architecture-building-systems/Wireless-Sensor-Network/Gateway/Gateway_Feather/Images/Gateway_collage.jpg

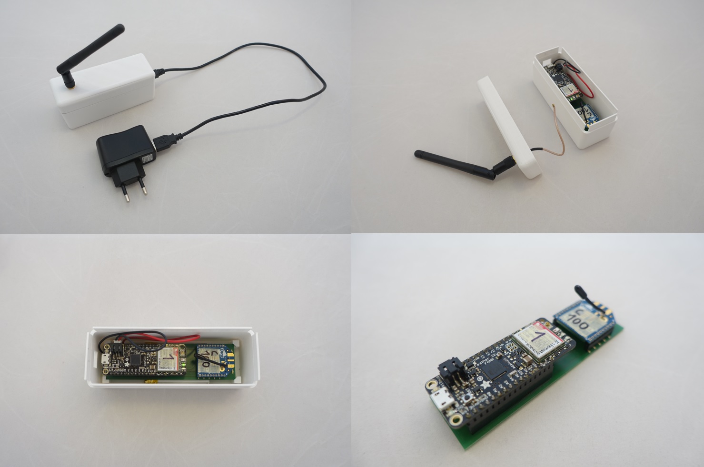
Gateway/Gateway_Feather/Images/Gateway_collage.jpg
