architecture-building-systems/Wireless-Sensor-Network/Gateway/Gateway_Mega/Images/gatweay_mega_with_enclosure_4.jpg

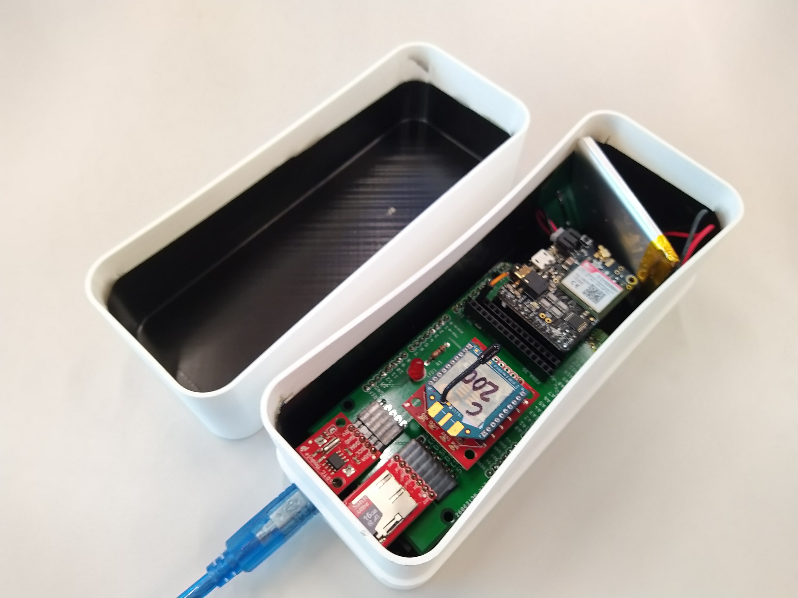
Gateway/Gateway_Mega/Images/gatweay_mega_with_enclosure_4.jpg
