architecture-building-systems/Wireless-Sensor-Network/Miscellaneous/Images/predecessor_systems/wsn_1_sensor_node_1.jpg

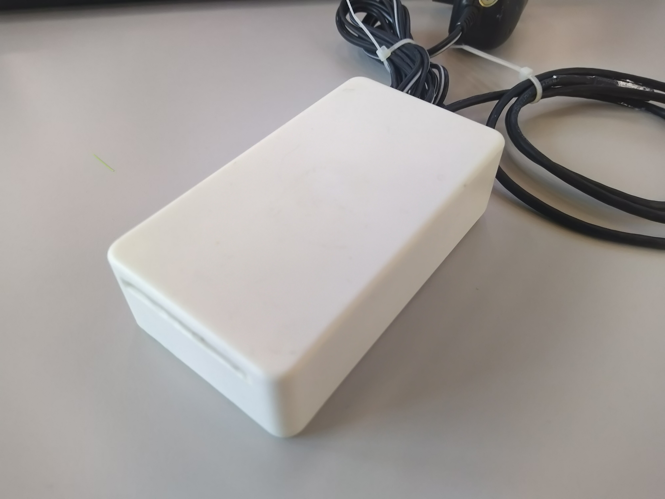
Miscellaneous/Images/predecessor_systems/wsn_1_sensor_node_1.jpg
