architecture-building-systems/Wireless-Sensor-Network/Miscellaneous/Images/predecessor_systems/wsn_2_router_node_2.jpg

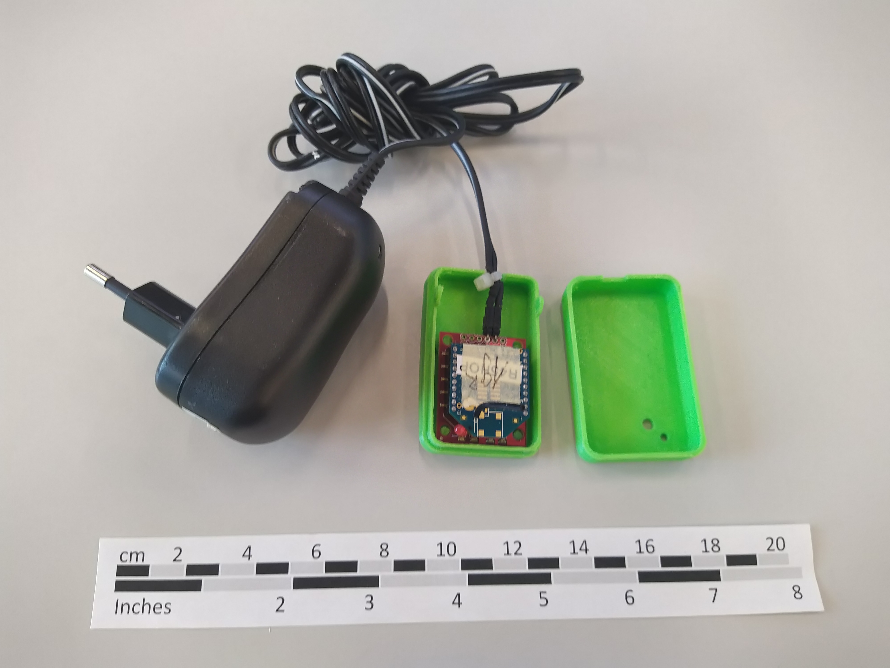
Miscellaneous/Images/predecessor_systems/wsn_2_router_node_2.jpg
