architecture-building-systems/Wireless-Sensor-Network/Miscellaneous/Images/predecessor_systems/wsn_2_router_node_4.jpg

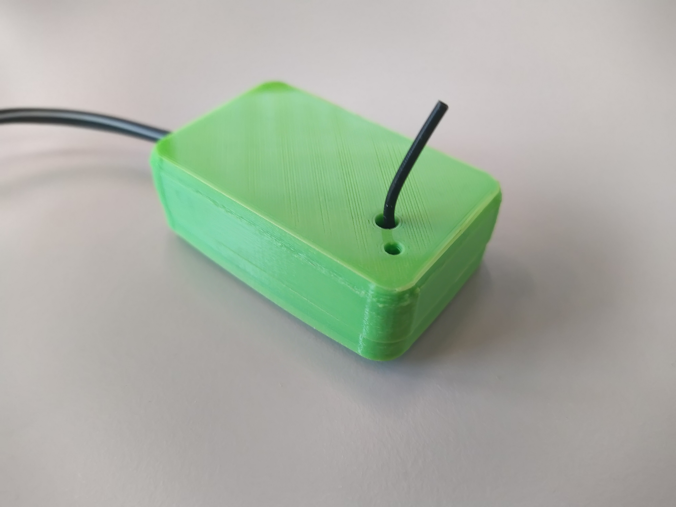
Miscellaneous/Images/predecessor_systems/wsn_2_router_node_4.jpg
