architecture-building-systems/Wireless-Sensor-Network/Miscellaneous/Images/predecessor_systems/wsn_2_sensor_node_5.jpg

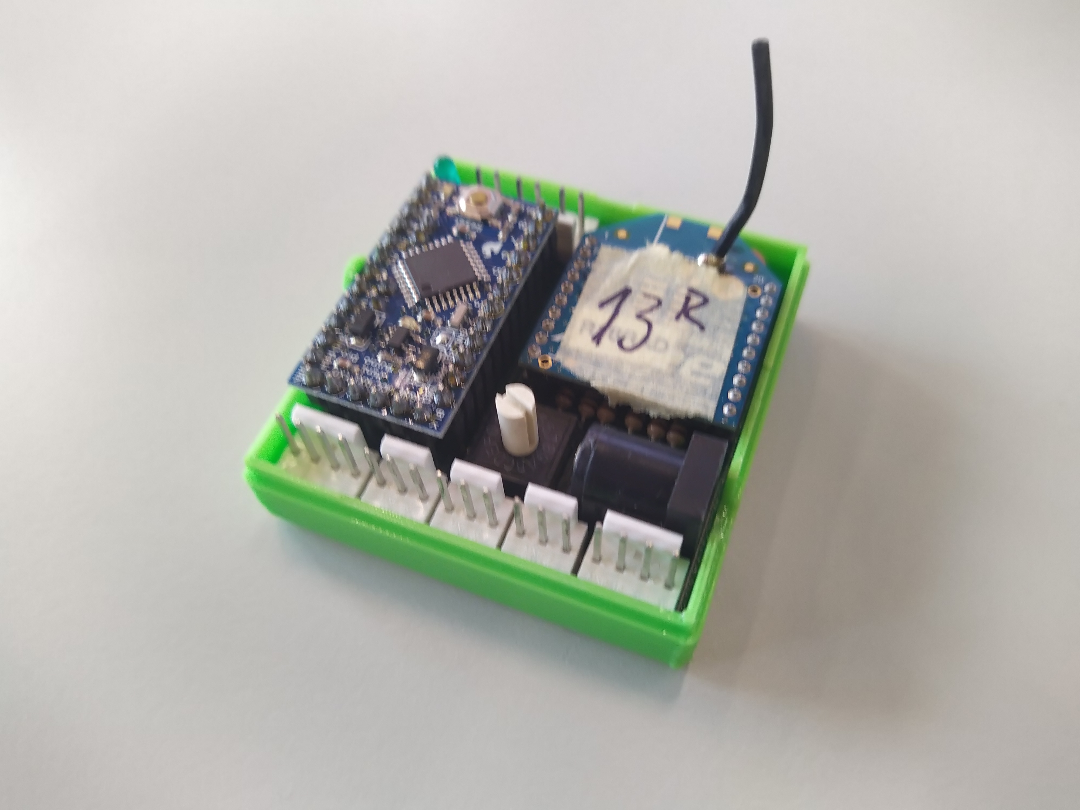
Miscellaneous/Images/predecessor_systems/wsn_2_sensor_node_5.jpg
