architecture-building-systems/Wireless-Sensor-Network/Miscellaneous/Images/Sensor_Kit_2.png

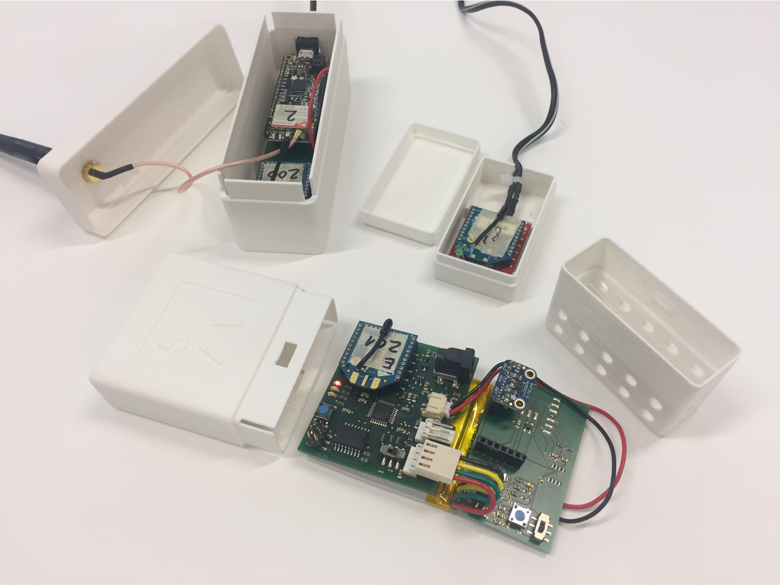
Miscellaneous/Images/Sensor_Kit_2.png
