architecture-building-systems/Wireless-Sensor-Network/Miscellaneous/Images/Sensor_Node_1.png

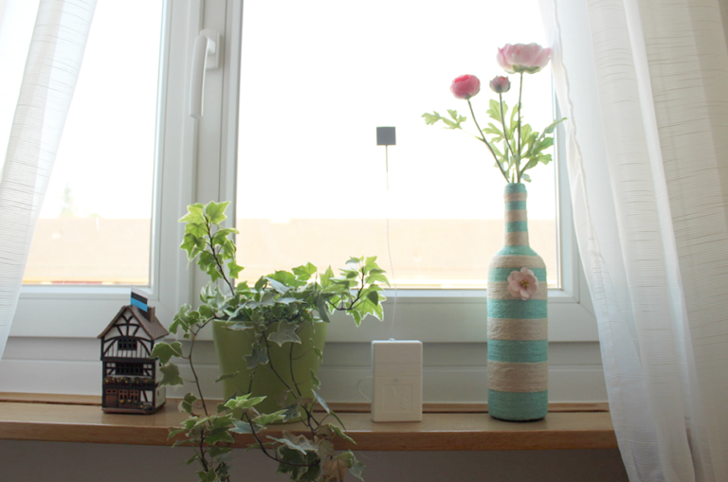
Miscellaneous/Images/Sensor_Node_1.png
