architecture-building-systems/Wireless-Sensor-Network/Miscellaneous/Images/Sensor_Node_2.png

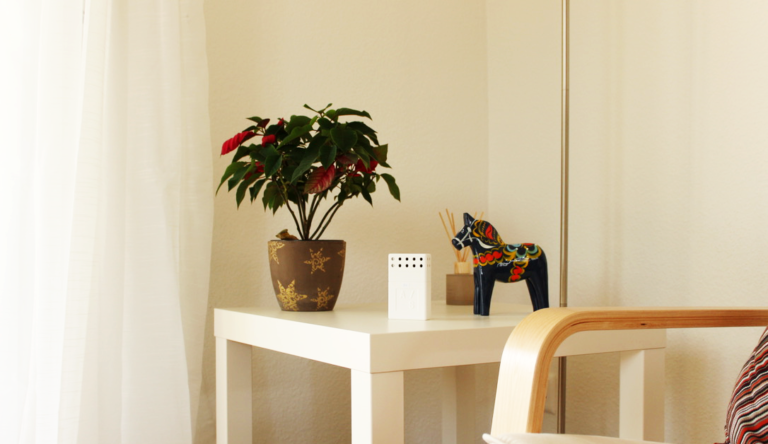
Miscellaneous/Images/Sensor_Node_2.png
