architecture-building-systems/Wireless-Sensor-Network/Miscellaneous/Images/Sensor_Node_3.png

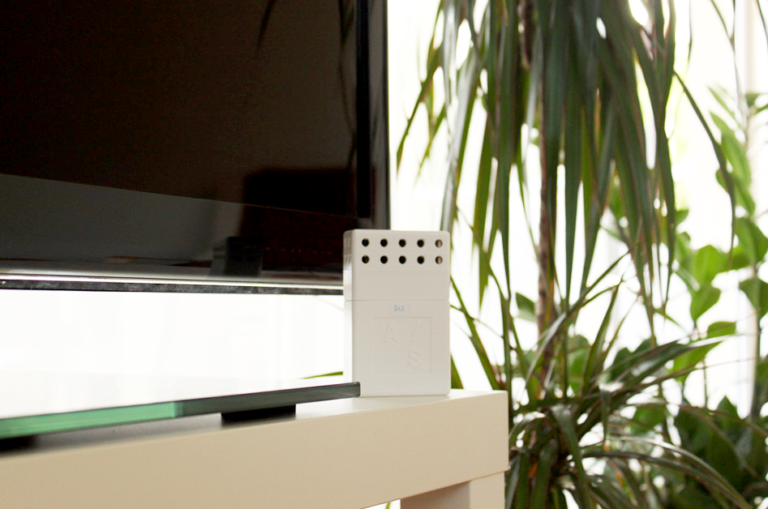
Miscellaneous/Images/Sensor_Node_3.png
