architecture-building-systems/Wireless-Sensor-Network/Sensor_Node/Main_module/Images/main_module_diode_orientation.jpg

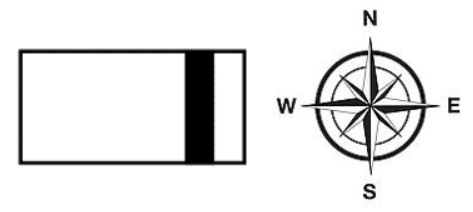
Sensor_Node/Main_module/Images/main_module_diode_orientation.jpg
