architecture-building-systems/Wireless-Sensor-Network/Sensor_Node/Main_module/Images/Main_module_high_side_switch_ic_orientation.jpg

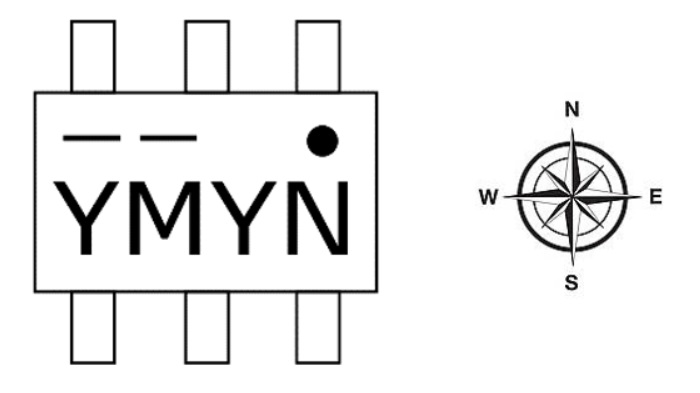
Sensor_Node/Main_module/Images/Main_module_high_side_switch_ic_orientation.jpg
