architecture-building-systems/Wireless-Sensor-Network/Sensor_Node/Main_module/Images/main_module_isp_connector_orientation.jpg

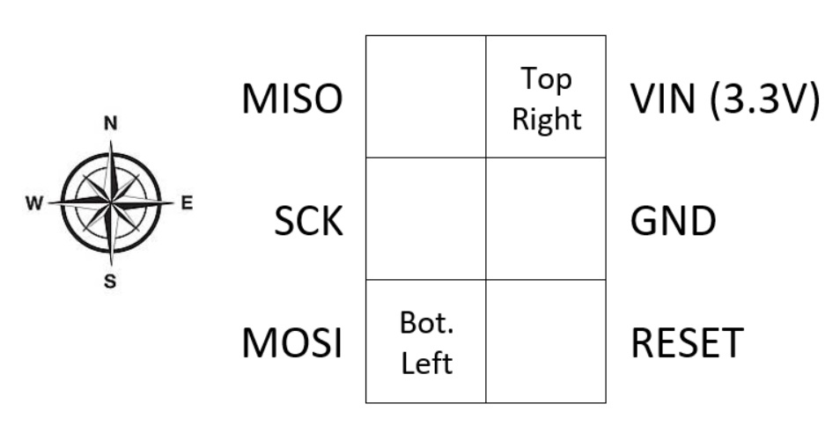
Sensor_Node/Main_module/Images/main_module_isp_connector_orientation.jpg
