architecture-building-systems/Wireless-Sensor-Network/Gateway/Gateway_Feather/CAD/Gateway_housing_bottom_v6.stl

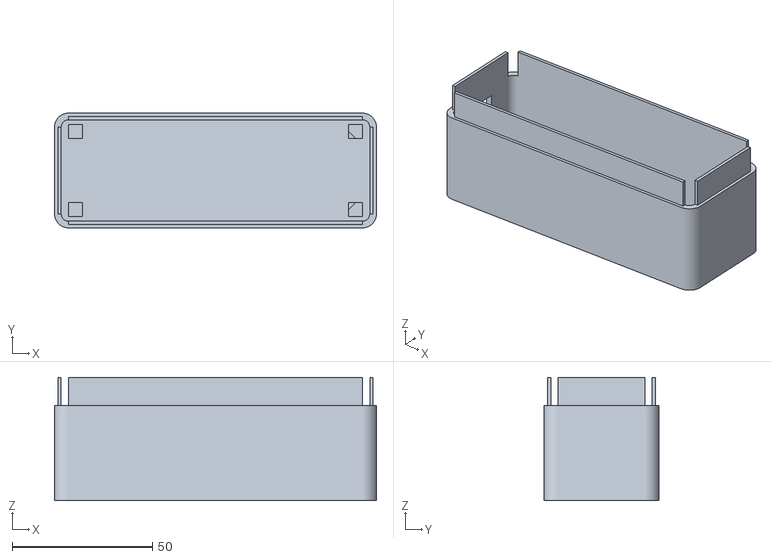
[picture p46: CAD file, 2017-03-10]
Gateway/Gateway_Feather/CAD/Gateway_housing_bottom_v6.stl
115.0 x 41.0 x 44.0
