architecture-building-systems/Wireless-Sensor-Network/Miscellaneous/CAD/cable_reel_v4.1_bottom.stl

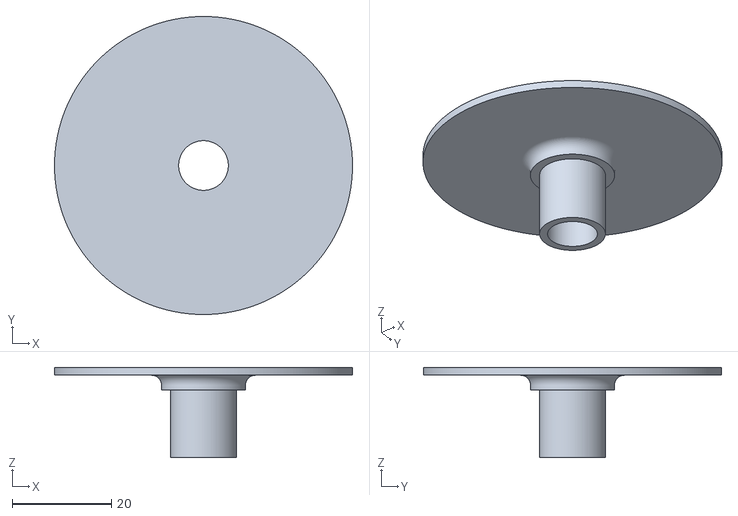
[picture p47: CAD file, 2018-12-11]
Miscellaneous/CAD/cable_reel_v4.1_bottom.stl
60.0 x 60.0 x 18.2
