architecture-building-systems/Wireless-Sensor-Network/Sensor_Node/CAD/u_value_angle_v5.stl

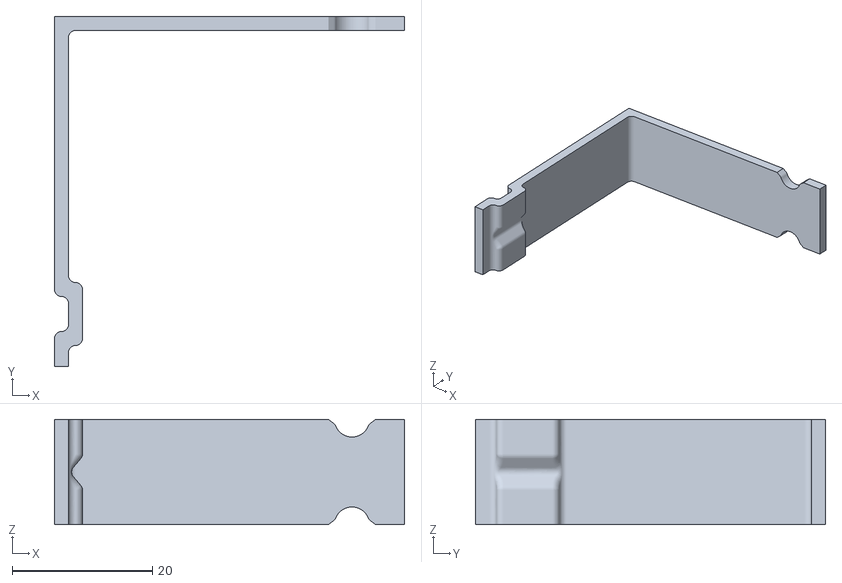
[picture p48: CAD file, 2017-05-09]
Sensor_Node/CAD/u_value_angle_v5.stl
50.0 x 50.0 x 15.0
