architecture-building-systems/Wireless-Sensor-Network/Miscellaneous/CAD/Reed_switch_transport_lock_v1.prt.stl

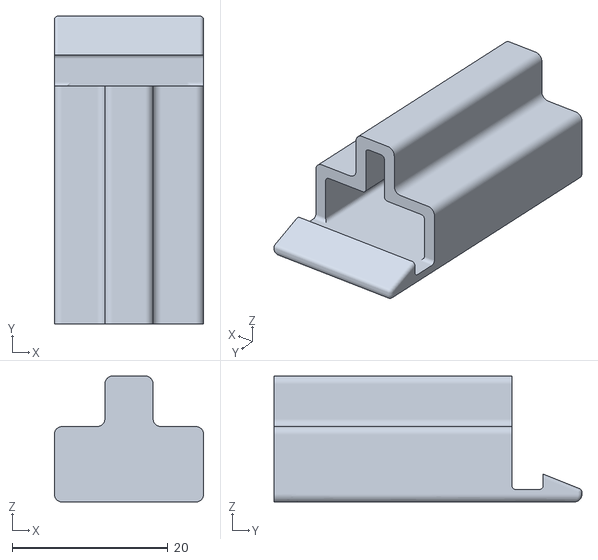
[picture p50: CAD file, 2018-12-06]
Miscellaneous/CAD/Reed_switch_transport_lock_v1.prt.stl
19.2 x 39.6 x 16.2
