architecture-building-systems/Wireless-Sensor-Network/Miscellaneous/CAD/battery_box_v2_small.stl

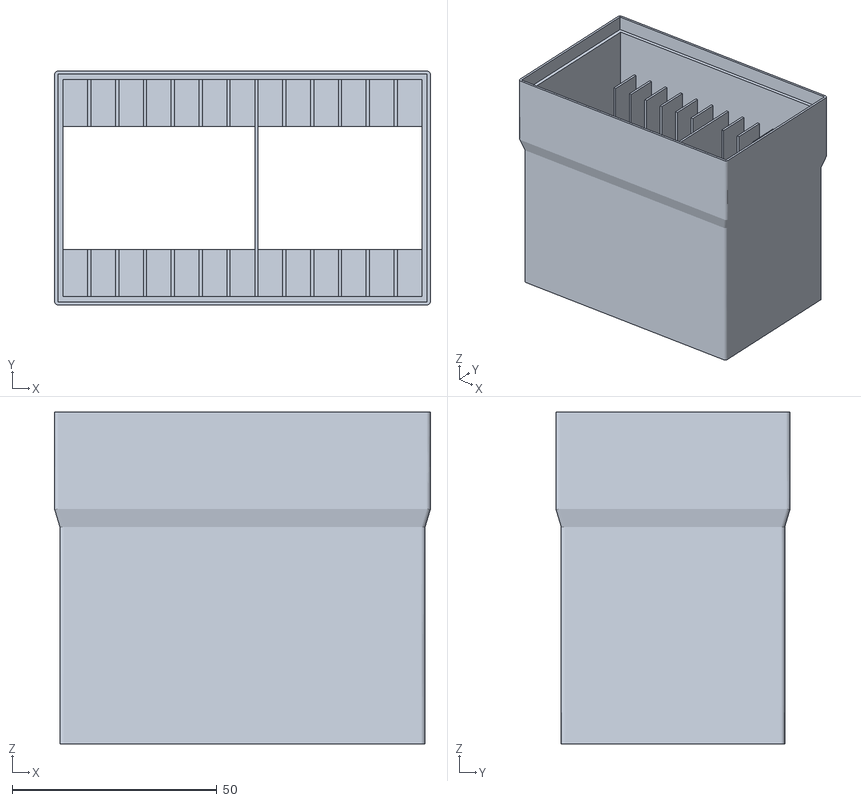
[picture p51: CAD file, 2018-12-06]
Miscellaneous/CAD/battery_box_v2_small.stl
91.8 x 57.2 x 81.0
