architecture-building-systems/Wireless-Sensor-Network/Miscellaneous/CAD/battery_box_v2.stl

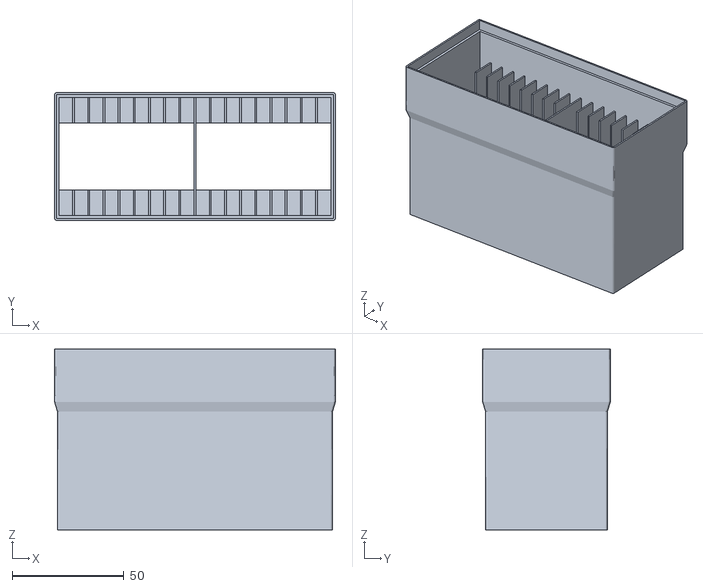
[picture p52: CAD file, 2018-02-06]
Miscellaneous/CAD/battery_box_v2.stl
125.8 x 57.2 x 81.0
