architecture-building-systems/Wireless-Sensor-Network/Miscellaneous/CAD/cable_reel_v2.stl

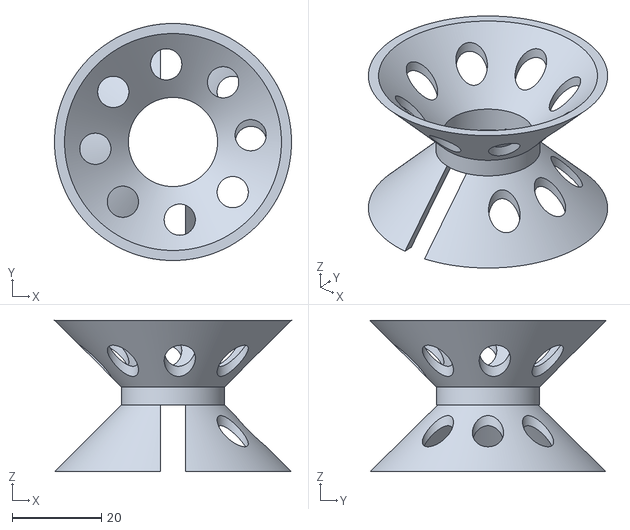
[picture p53: CAD file, 2018-02-04]
Miscellaneous/CAD/cable_reel_v2.stl
53.2 x 53.2 x 34.0
