architecture-building-systems/Wireless-Sensor-Network/Miscellaneous/CAD/dustpan_v1.stl

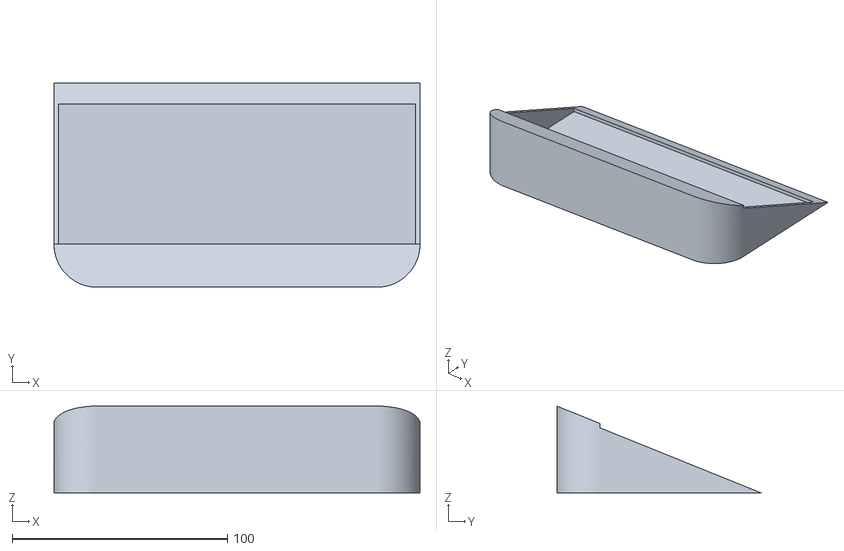
[picture p54: CAD file, 2017-06-19]
Miscellaneous/CAD/dustpan_v1.stl
170.0 x 95.0 x 40.4
