architecture-building-systems/Wireless-Sensor-Network/Miscellaneous/CAD/xbee_graber_v1.stl

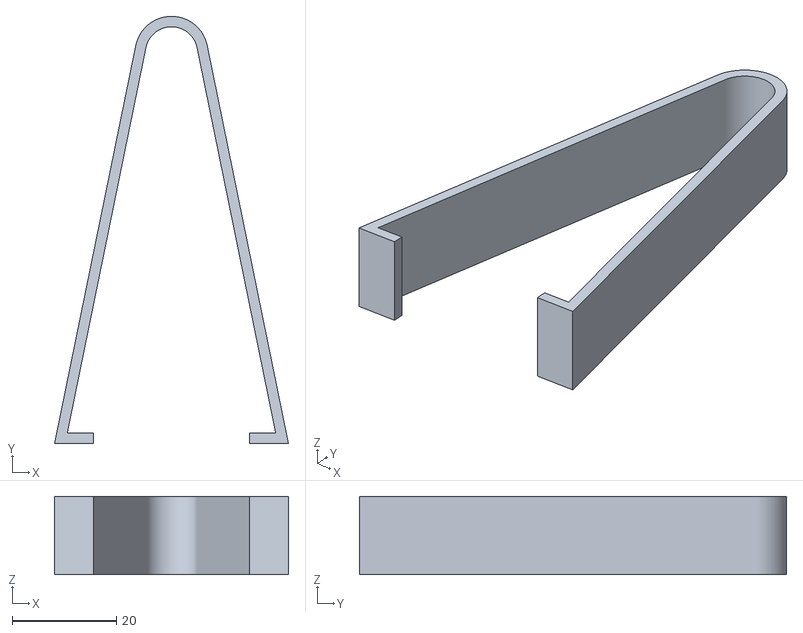
[picture p55: CAD file, 2017-04-19]
Miscellaneous/CAD/xbee_graber_v1.stl
44.9 x 82.0 x 15.0
