architecture-building-systems/Wireless-Sensor-Network/Miscellaneous/Images/instructions/arduino_ide_select_board_arduino_mega.png

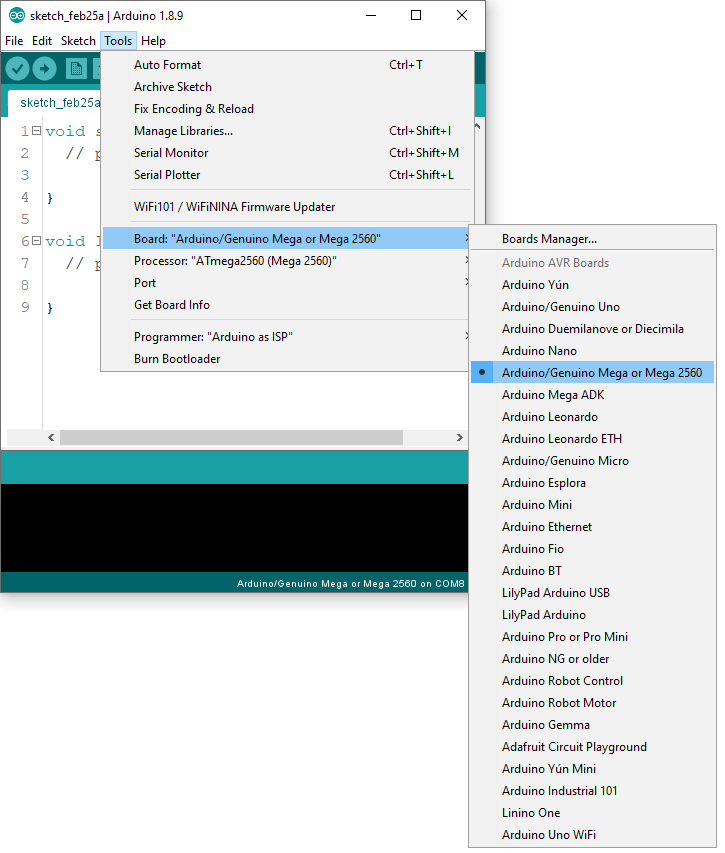
Miscellaneous/Images/instructions/arduino_ide_select_board_arduino_mega.png
