architecture-building-systems/Wireless-Sensor-Network/Miscellaneous/Images/instructions/arduino_ide_select_board_arduino_pro_mini.png

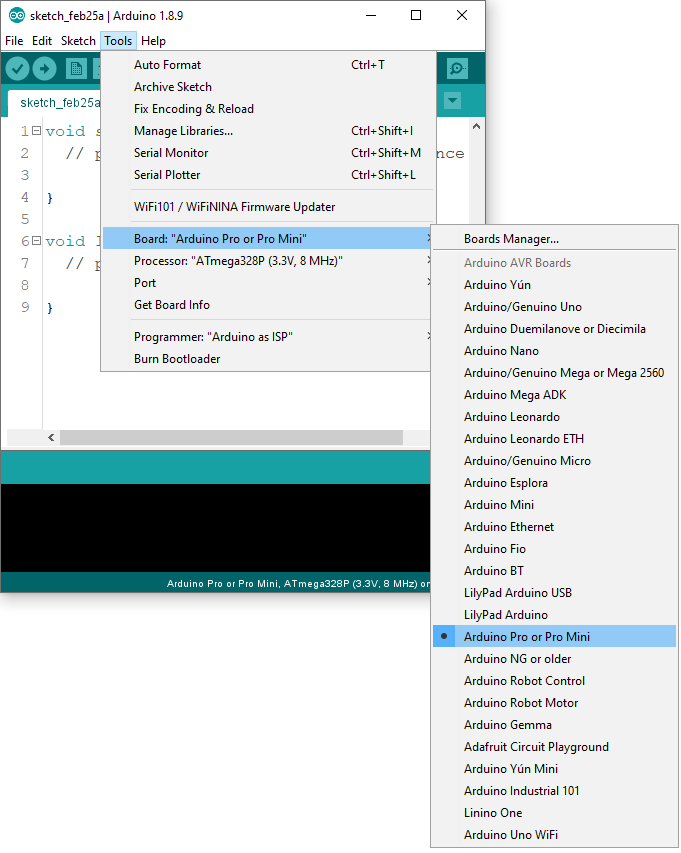
Miscellaneous/Images/instructions/arduino_ide_select_board_arduino_pro_mini.png
