architecture-building-systems/Wireless-Sensor-Network/Miscellaneous/Images/instructions/arduino_ide_select_processor_atmega328p_3.3v.png

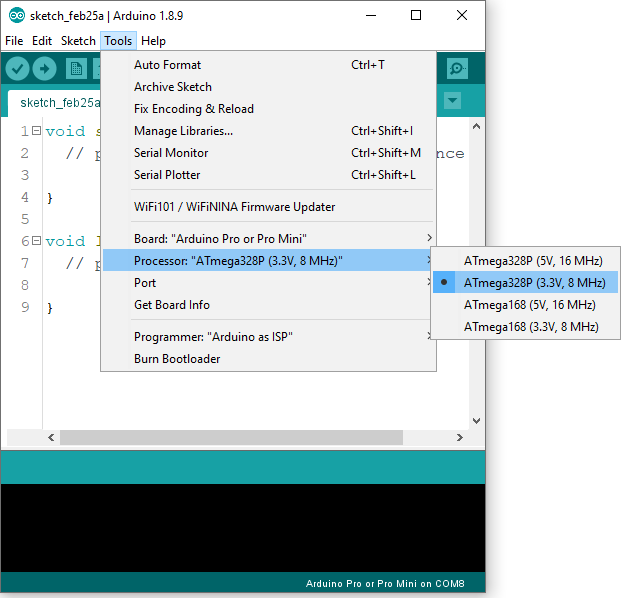
Miscellaneous/Images/instructions/arduino_ide_select_processor_atmega328p_3.3v.png
