architecture-building-systems/Wireless-Sensor-Network/Miscellaneous/Images/instructions/arduino_ide_select_processor_atmega2560.png

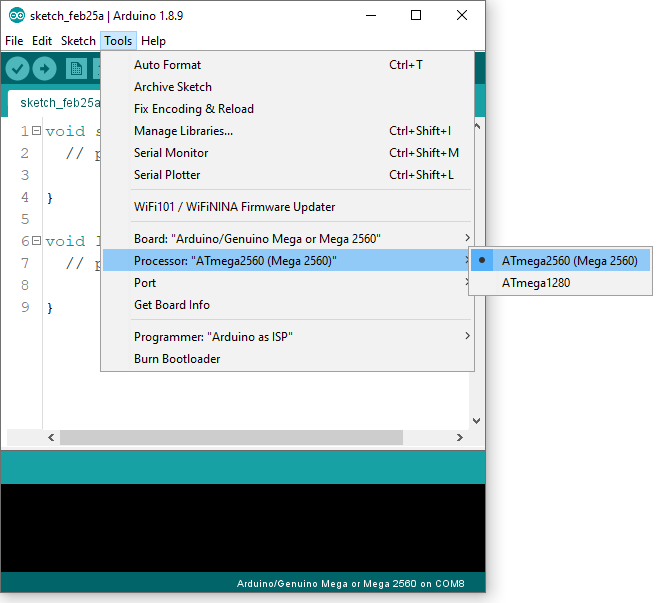
Miscellaneous/Images/instructions/arduino_ide_select_processor_atmega2560.png
