architecture-building-systems/Wireless-Sensor-Network/Miscellaneous/Images/instructions/arduino_ide_select_programmer_mega.png

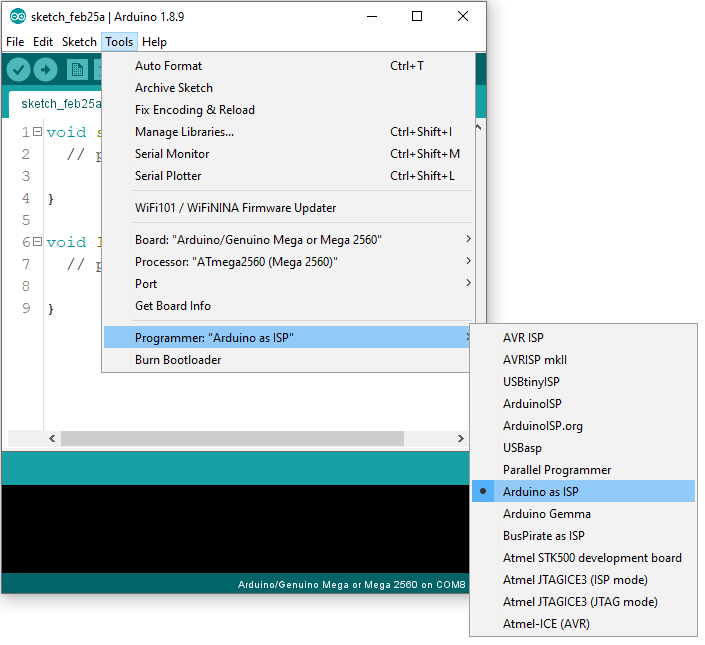
Miscellaneous/Images/instructions/arduino_ide_select_programmer_mega.png
