architecture-building-systems/Wireless-Sensor-Network/Miscellaneous/Images/instructions/arduino_ide_upload_sketch_to_atmega328p_with_programmer.png

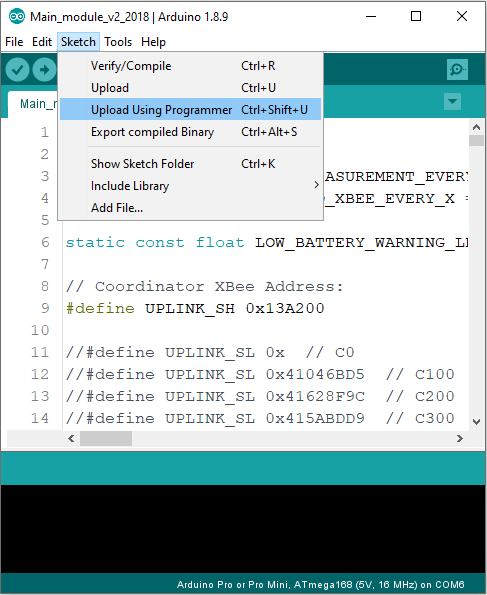
Miscellaneous/Images/instructions/arduino_ide_upload_sketch_to_atmega328p_with_programmer.png
