architecture-building-systems/Wireless-Sensor-Network/Miscellaneous/Images/instructions/arduino_ide_upload_sketch_to_atmega2560_via_serial.png

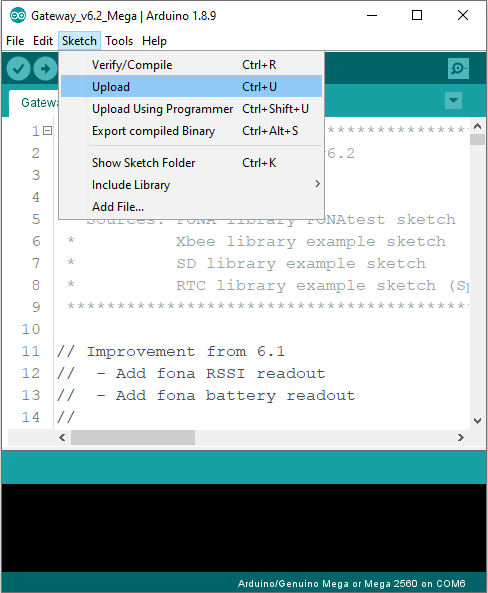
Miscellaneous/Images/instructions/arduino_ide_upload_sketch_to_atmega2560_via_serial.png
