architecture-building-systems/Wireless-Sensor-Network/Miscellaneous/Images/instructions/arduino_pro_mini_as_isp.jpg

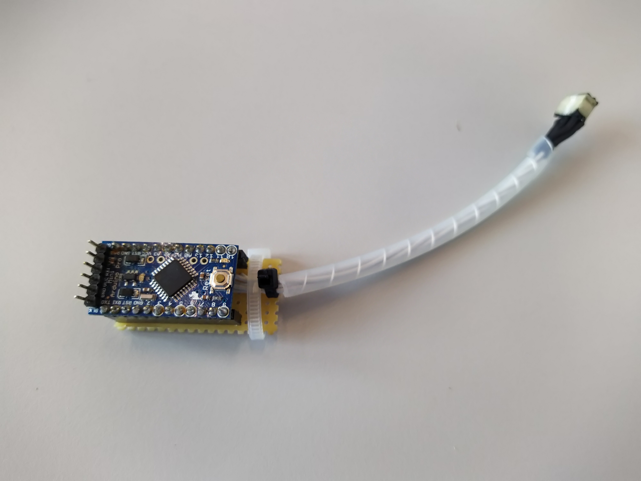
Miscellaneous/Images/instructions/arduino_pro_mini_as_isp.jpg
