architecture-building-systems/Wireless-Sensor-Network/Miscellaneous/Images/instructions/screenshot_x-ctu_select_profile.png

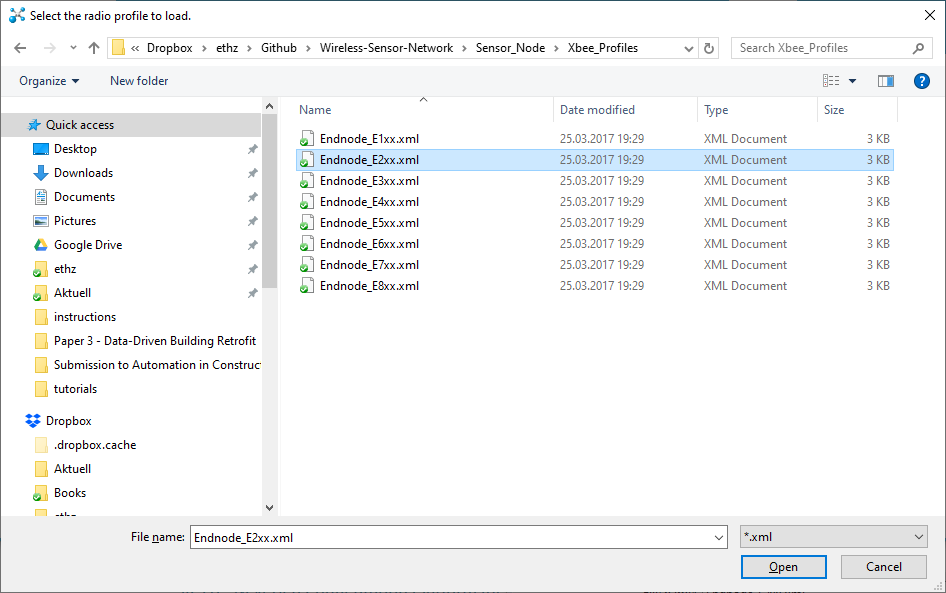
Miscellaneous/Images/instructions/screenshot_x-ctu_select_profile.png
