architecture-building-systems/Wireless-Sensor-Network/Miscellaneous/Images/instructions/screenshot_x-ctu_select_radio_module.png

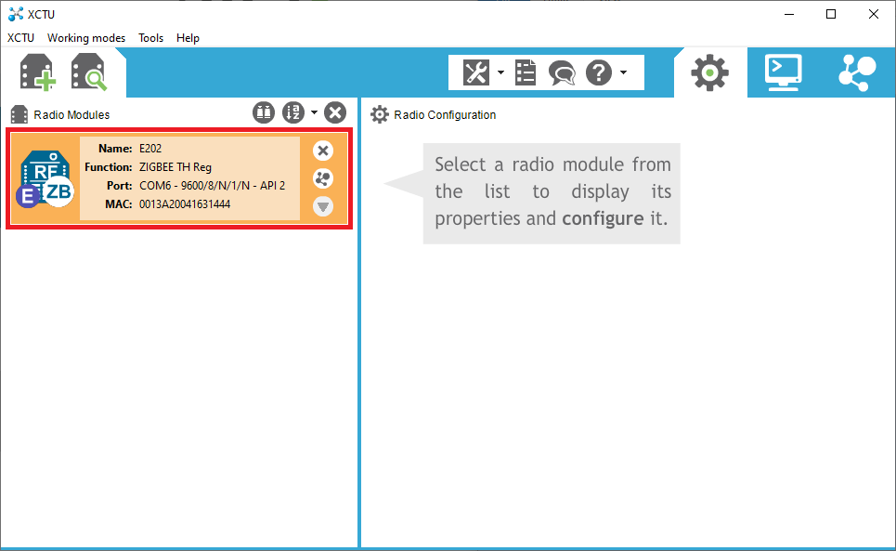
Miscellaneous/Images/instructions/screenshot_x-ctu_select_radio_module.png
