architecture-building-systems/Wireless-Sensor-Network/Miscellaneous/Images/instructions/arduino_ide_verify_sketch.png

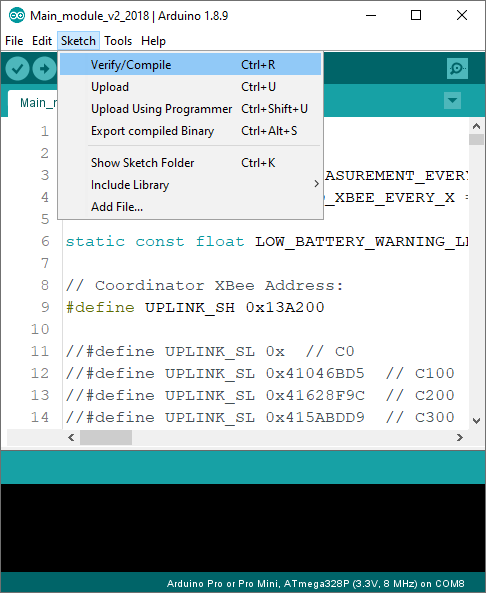
Miscellaneous/Images/instructions/arduino_ide_verify_sketch.png
