architecture-building-systems/Wireless-Sensor-Network/Miscellaneous/Images/instructions/screenshot_x-ctu_debugging_mesh_network_scan.png

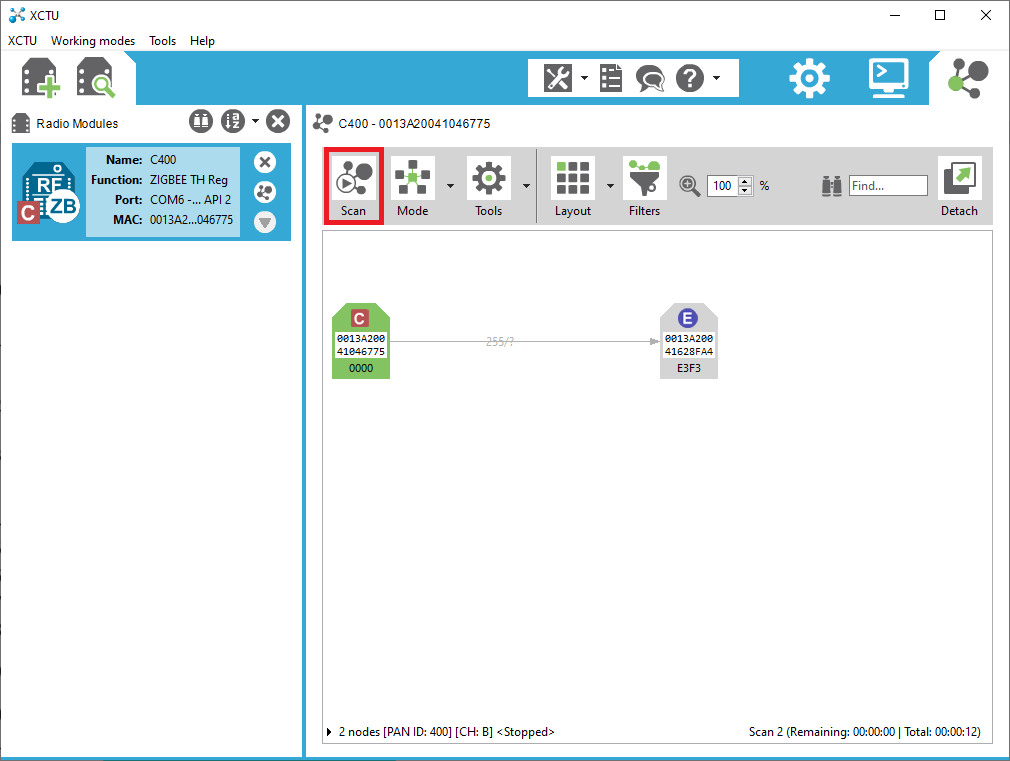
Miscellaneous/Images/instructions/screenshot_x-ctu_debugging_mesh_network_scan.png
