architecture-building-systems/Wireless-Sensor-Network/Sensor_Node/Sensor_modules/Sensor_Module_XX_Protoyping/Eagle/Sensor_Module_0xXX_Prototyping_v1_board.pdf

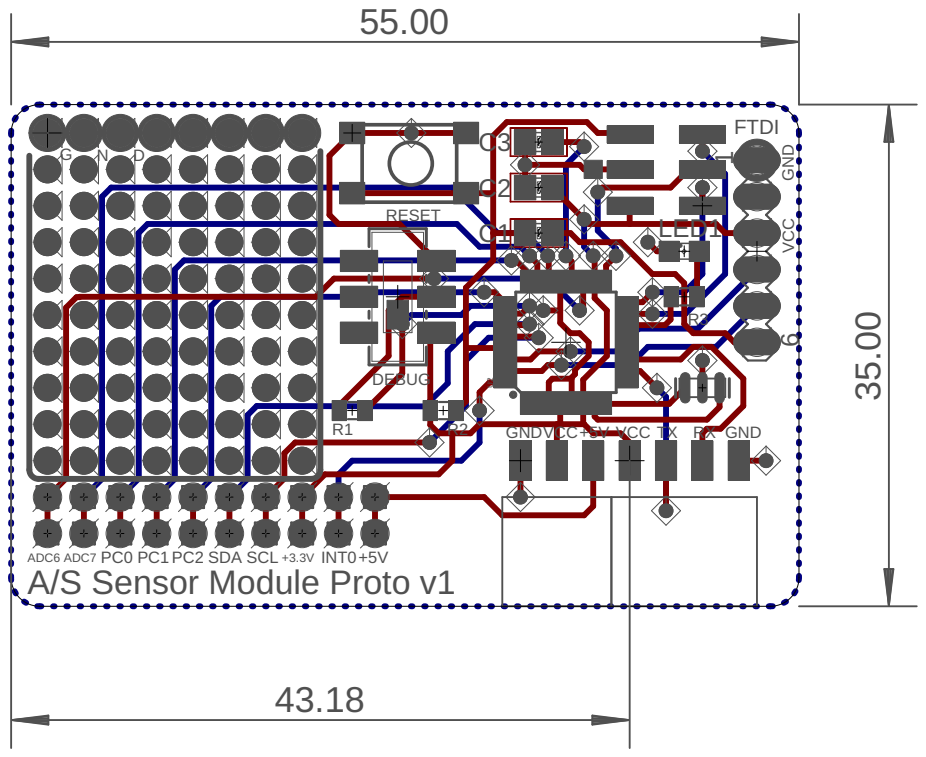
[picture p82: page 1]

VCC TX RX GND
