architecture-building-systems/Wireless-Sensor-Network/Sensor_Node/Sensor_modules/Sensor_Module_06_CO2_CCS811_v2/Eagle/Sensor_Module_0x06_CO2_CCS811_v2_board.pdf

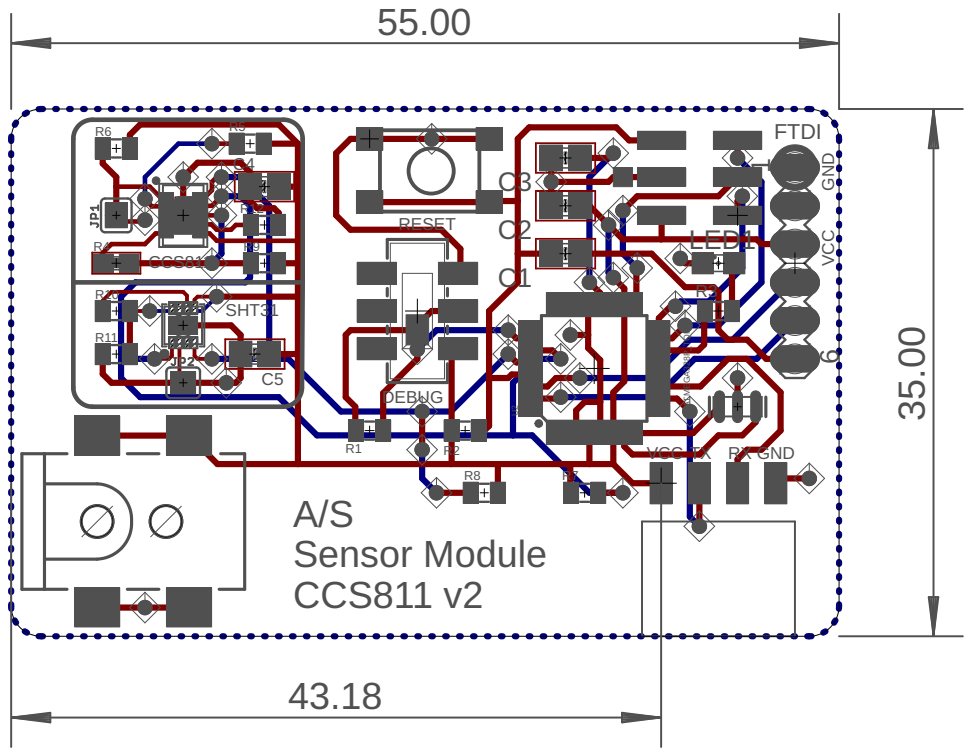
[picture p93: page 1]
