architecture-building-systems/Wireless-Sensor-Network/Sensor_Node/Sensor_modules/Sensor_Module_08_Dual_Temperatures_2xDS18B20_v1/Eagle/Sensor_Module_0x08_Dual_Temperatures_2xDS18B20_v1_board.pdf

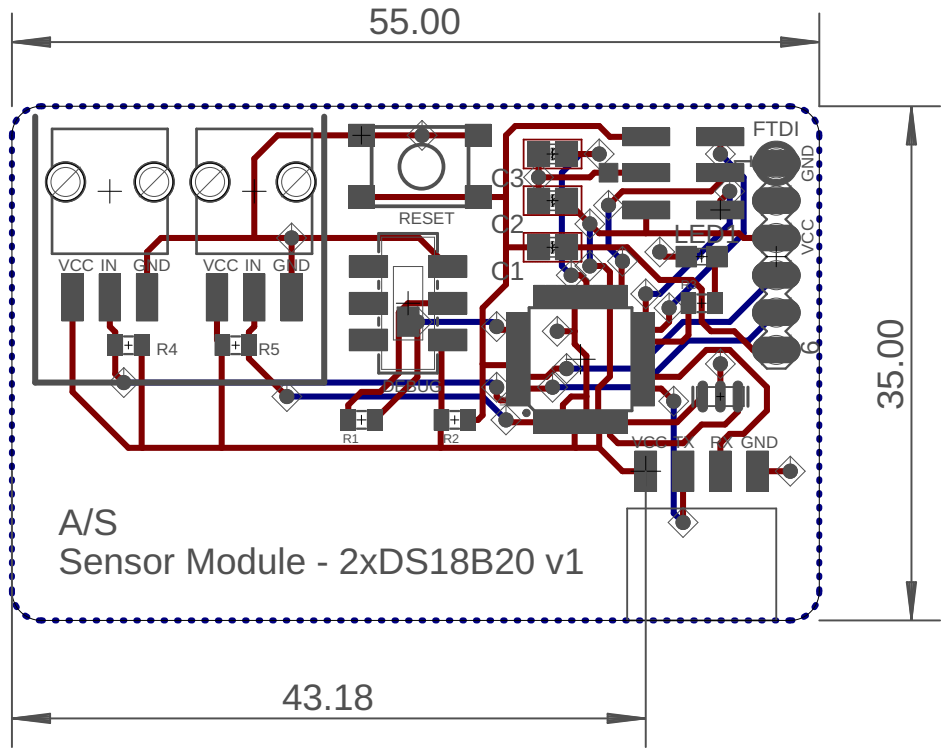
[picture p94: page 1]
