architecture-building-systems/Wireless-Sensor-Network/Sensor_Node/Sensor_modules/Sensor_Module_12_U-Value/Eagle/Sensor_Module_0x12_U-Value_v1_board.pdf

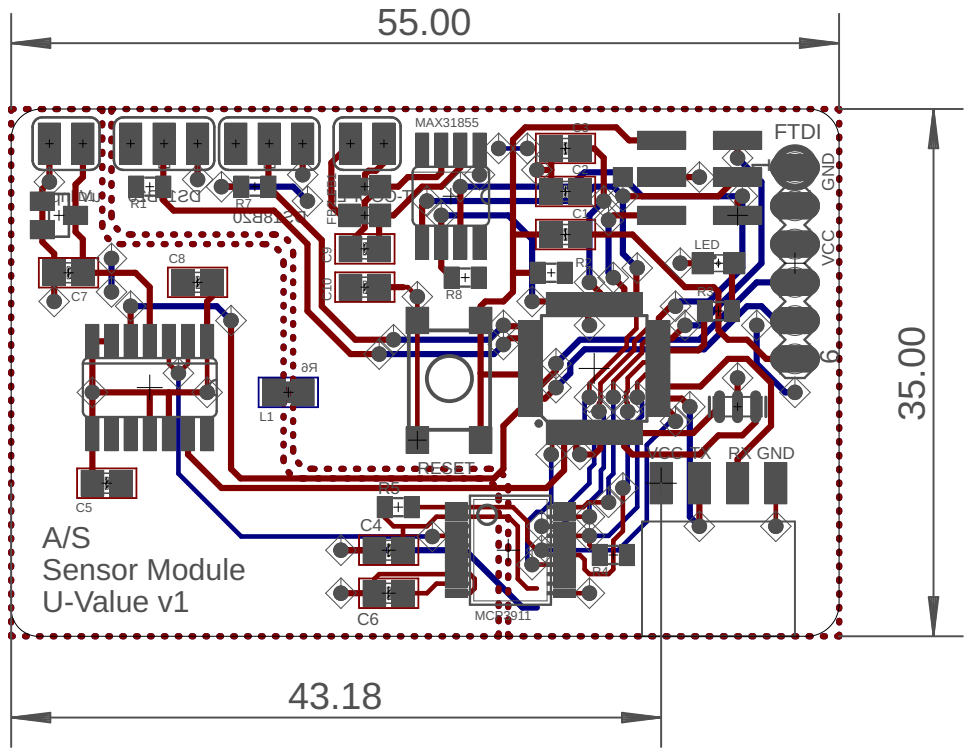
[picture p95: page 1]
