architecture-building-systems/Wireless-Sensor-Network/Sensor_Node/Sensor_modules/Sensor_Module_05_09_10_11_Pulse_v1/Eagle/Sensor_Module_0x09_0x10_Pulse_v1_board.pdf

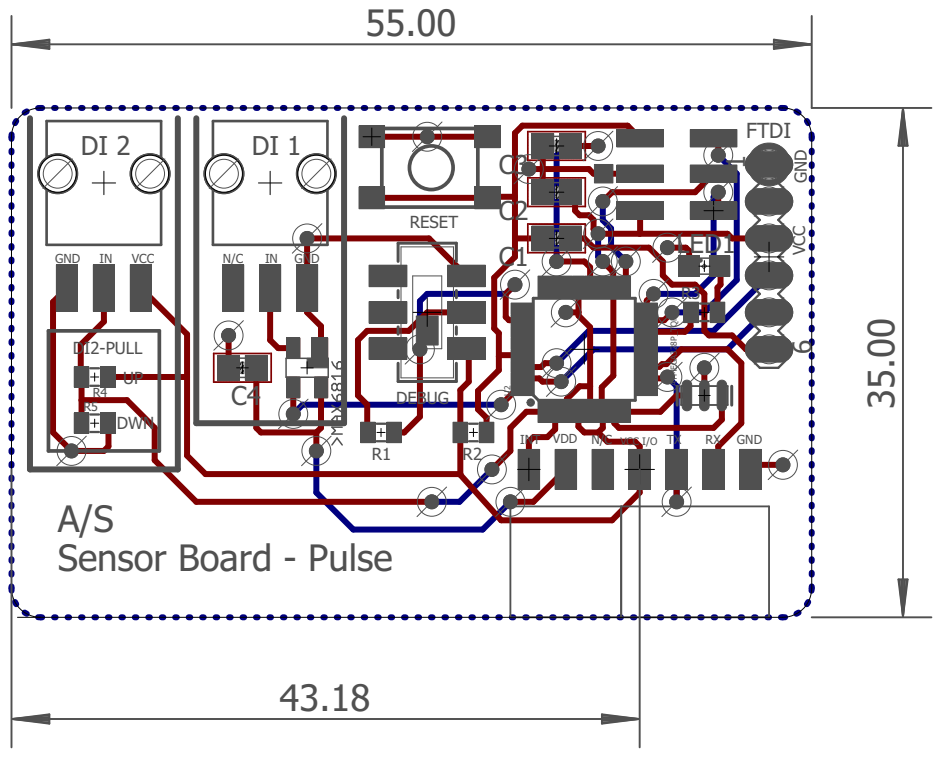
[picture p96: page 1]
