architecture-building-systems/Wireless-Sensor-Network/Sensor_Node/Sensor_modules/Previous Versions/Sensor_Module_0x02_TH_SHT31_v1/Eagle/Sensor_Module_0x02_TH_SHT31_v1_board.pdf

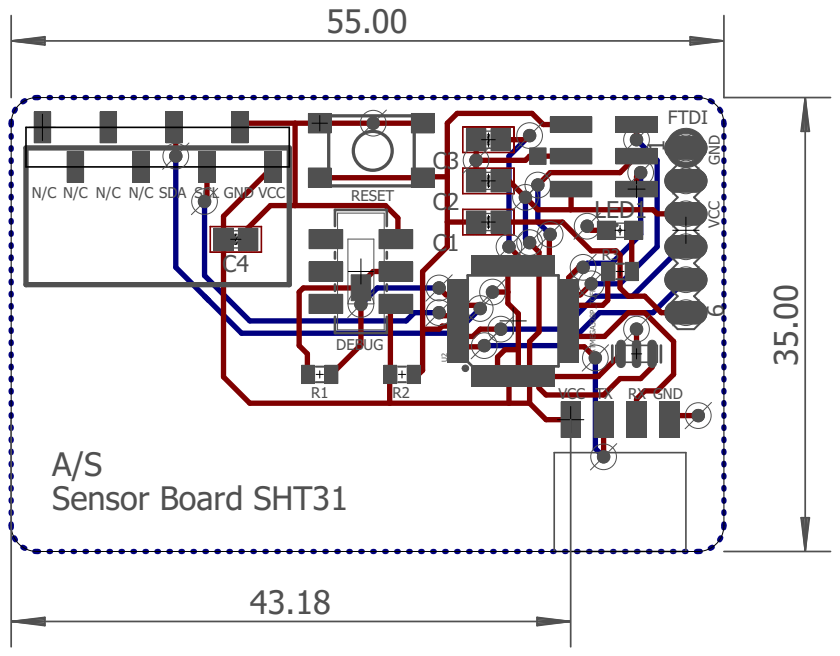
[picture p97: page 1]

N/C N/C N/C SDA SCL GND VCC
