architecture-building-systems/Wireless-Sensor-Network/Sensor_Node/Sensor_modules/Previous Versions/Sensor_Module_0x04_Luminosity_TSL2561_v1/Eagle/Sensor_Module_0x04_Luminosity_TSL2561_v1_board.pdf

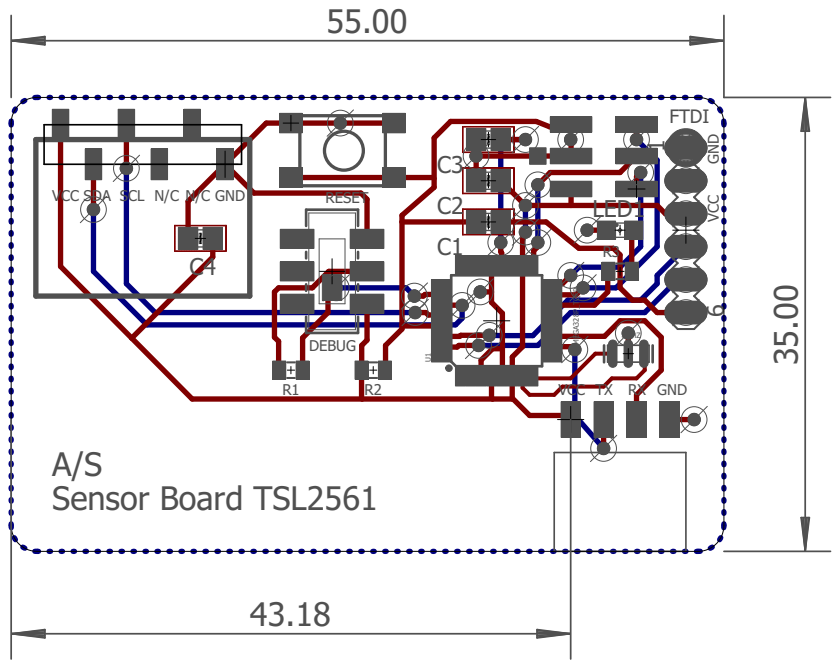
[picture p98: page 1]

VCC SDA SCL N/C N/C GND

VCC TX RX GND
