architecture-building-systems/Wireless-Sensor-Network/Sensor_Node/Sensor_modules/Previous Versions/Sensor_Module_0x02_TH_SHT31_v1/Eagle/Sensor_Module_0x02_TH_SHT31_v1_schematic.pdf

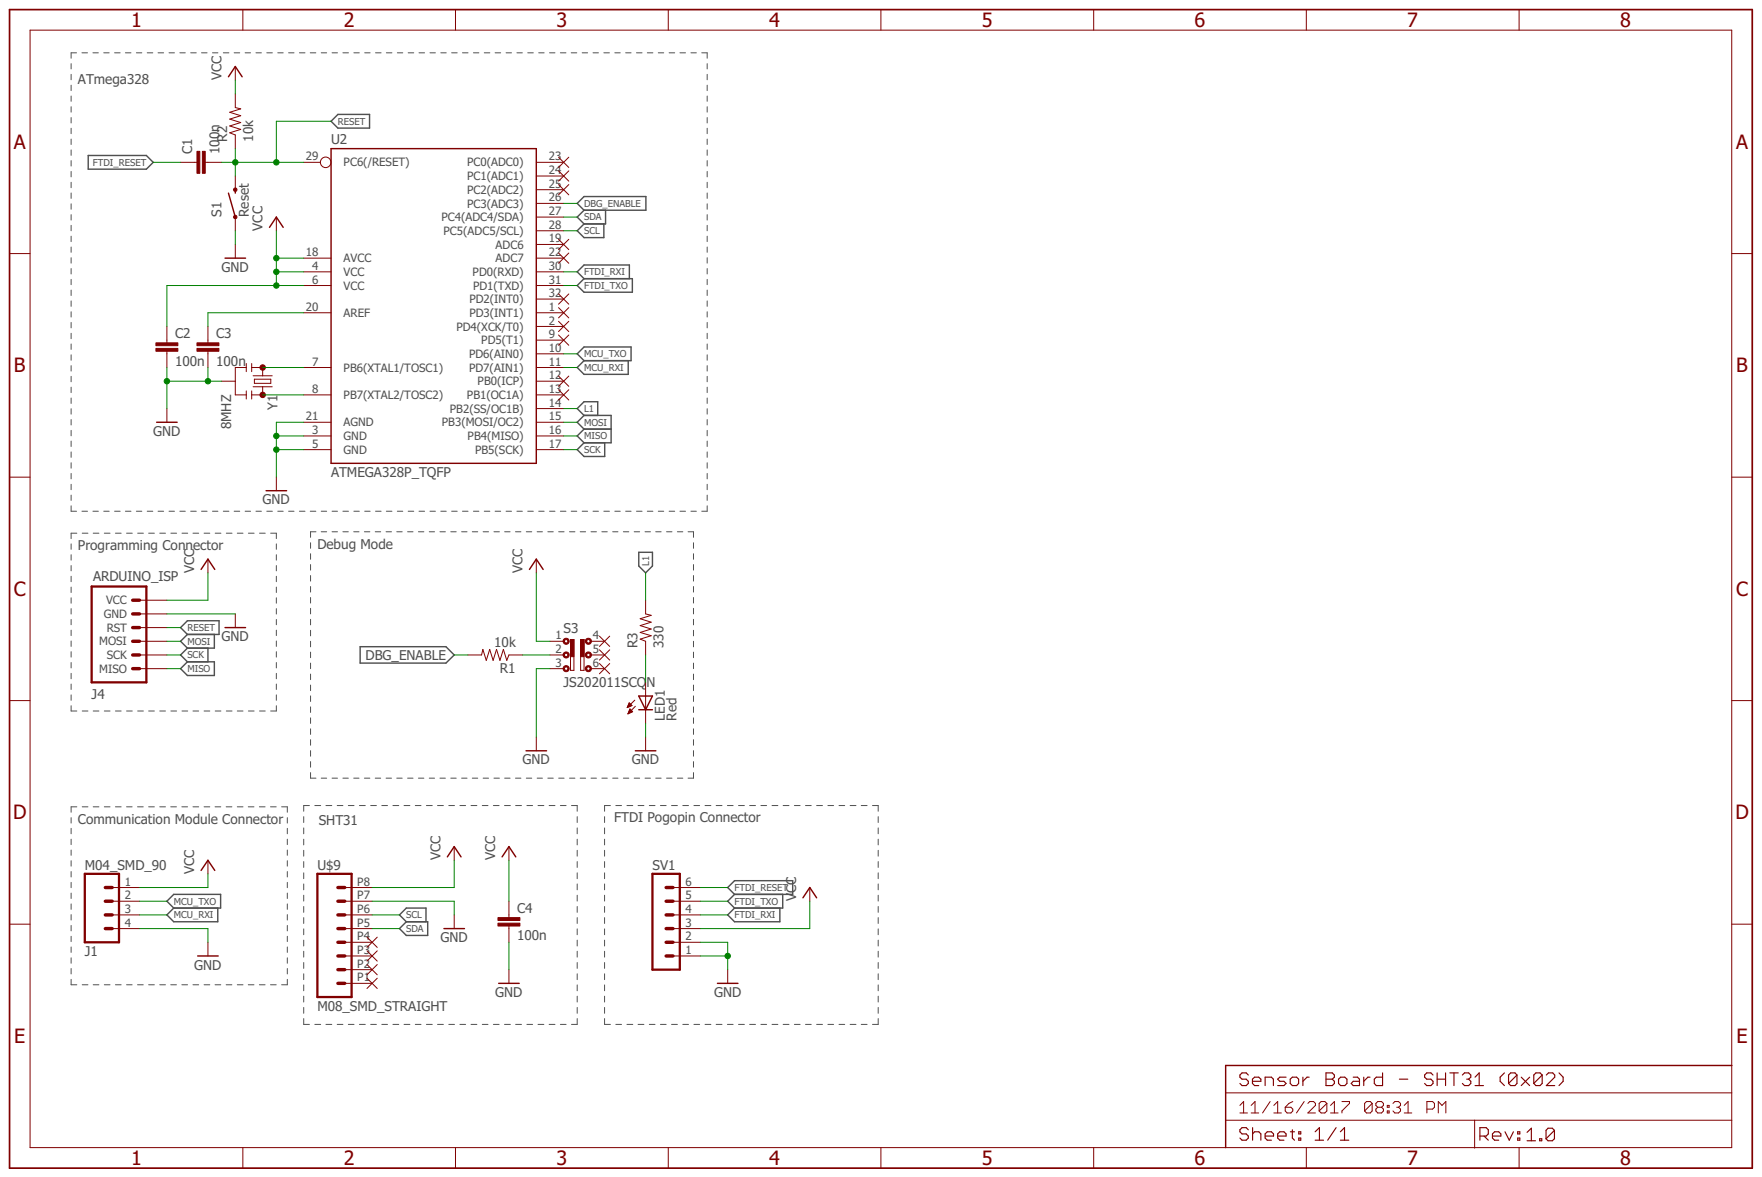
[picture p99: page 1]
