architecture-building-systems/Wireless-Sensor-Network/Sensor_Node/Sensor_modules/Previous Versions/Sensor_Module_0x04_Luminosity_TSL2561_v1/Eagle/Sensor_Module_0x04_Luminosity_TSL2561_v1_schematic.pdf

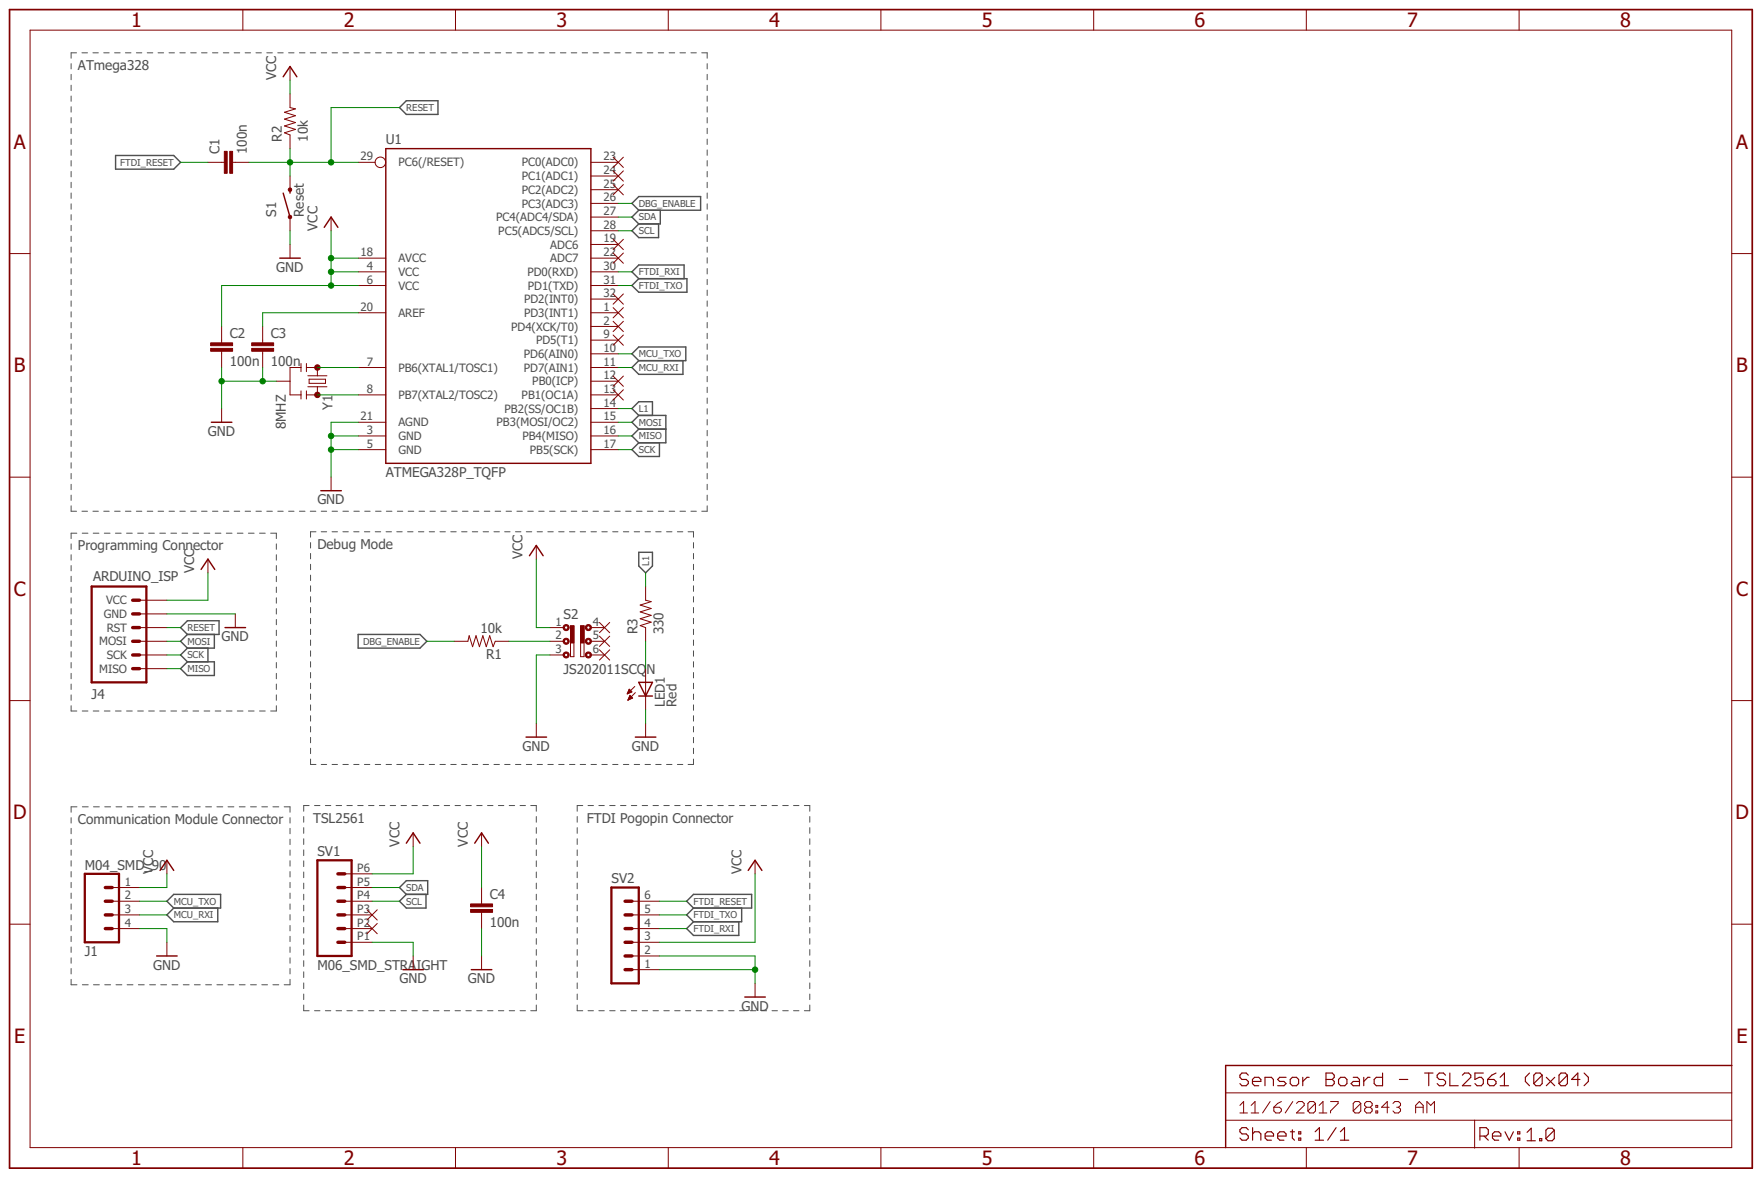
[picture p100: page 1]
