architecture-building-systems/Wireless-Sensor-Network/Sensor_Node/Sensor_modules/Previous Versions/Sensor_Module_0x06_CO2_S8_v1/Eagle/Sensor_Module_0x06_CO2_S8_v1_board.pdf

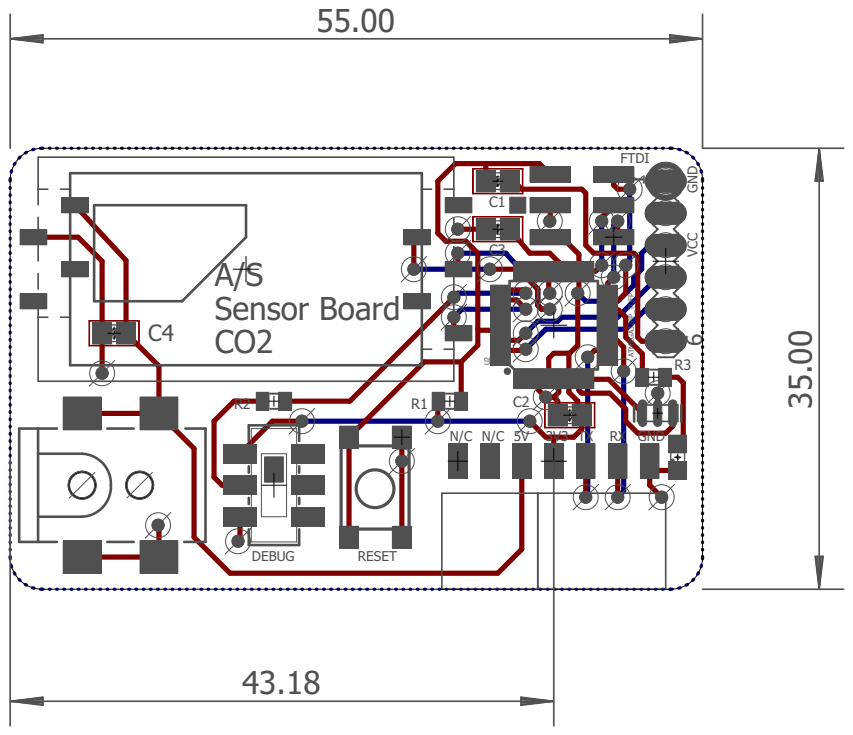
[picture p102: page 1]
