architecture-building-systems/Wireless-Sensor-Network/Sensor_Node/Main_module/Eagle/Main_module_v2.brd

## EAGLE design Sensor_Node/Main_module/Eagle/Main_module_v2.brd (2017-03-10)

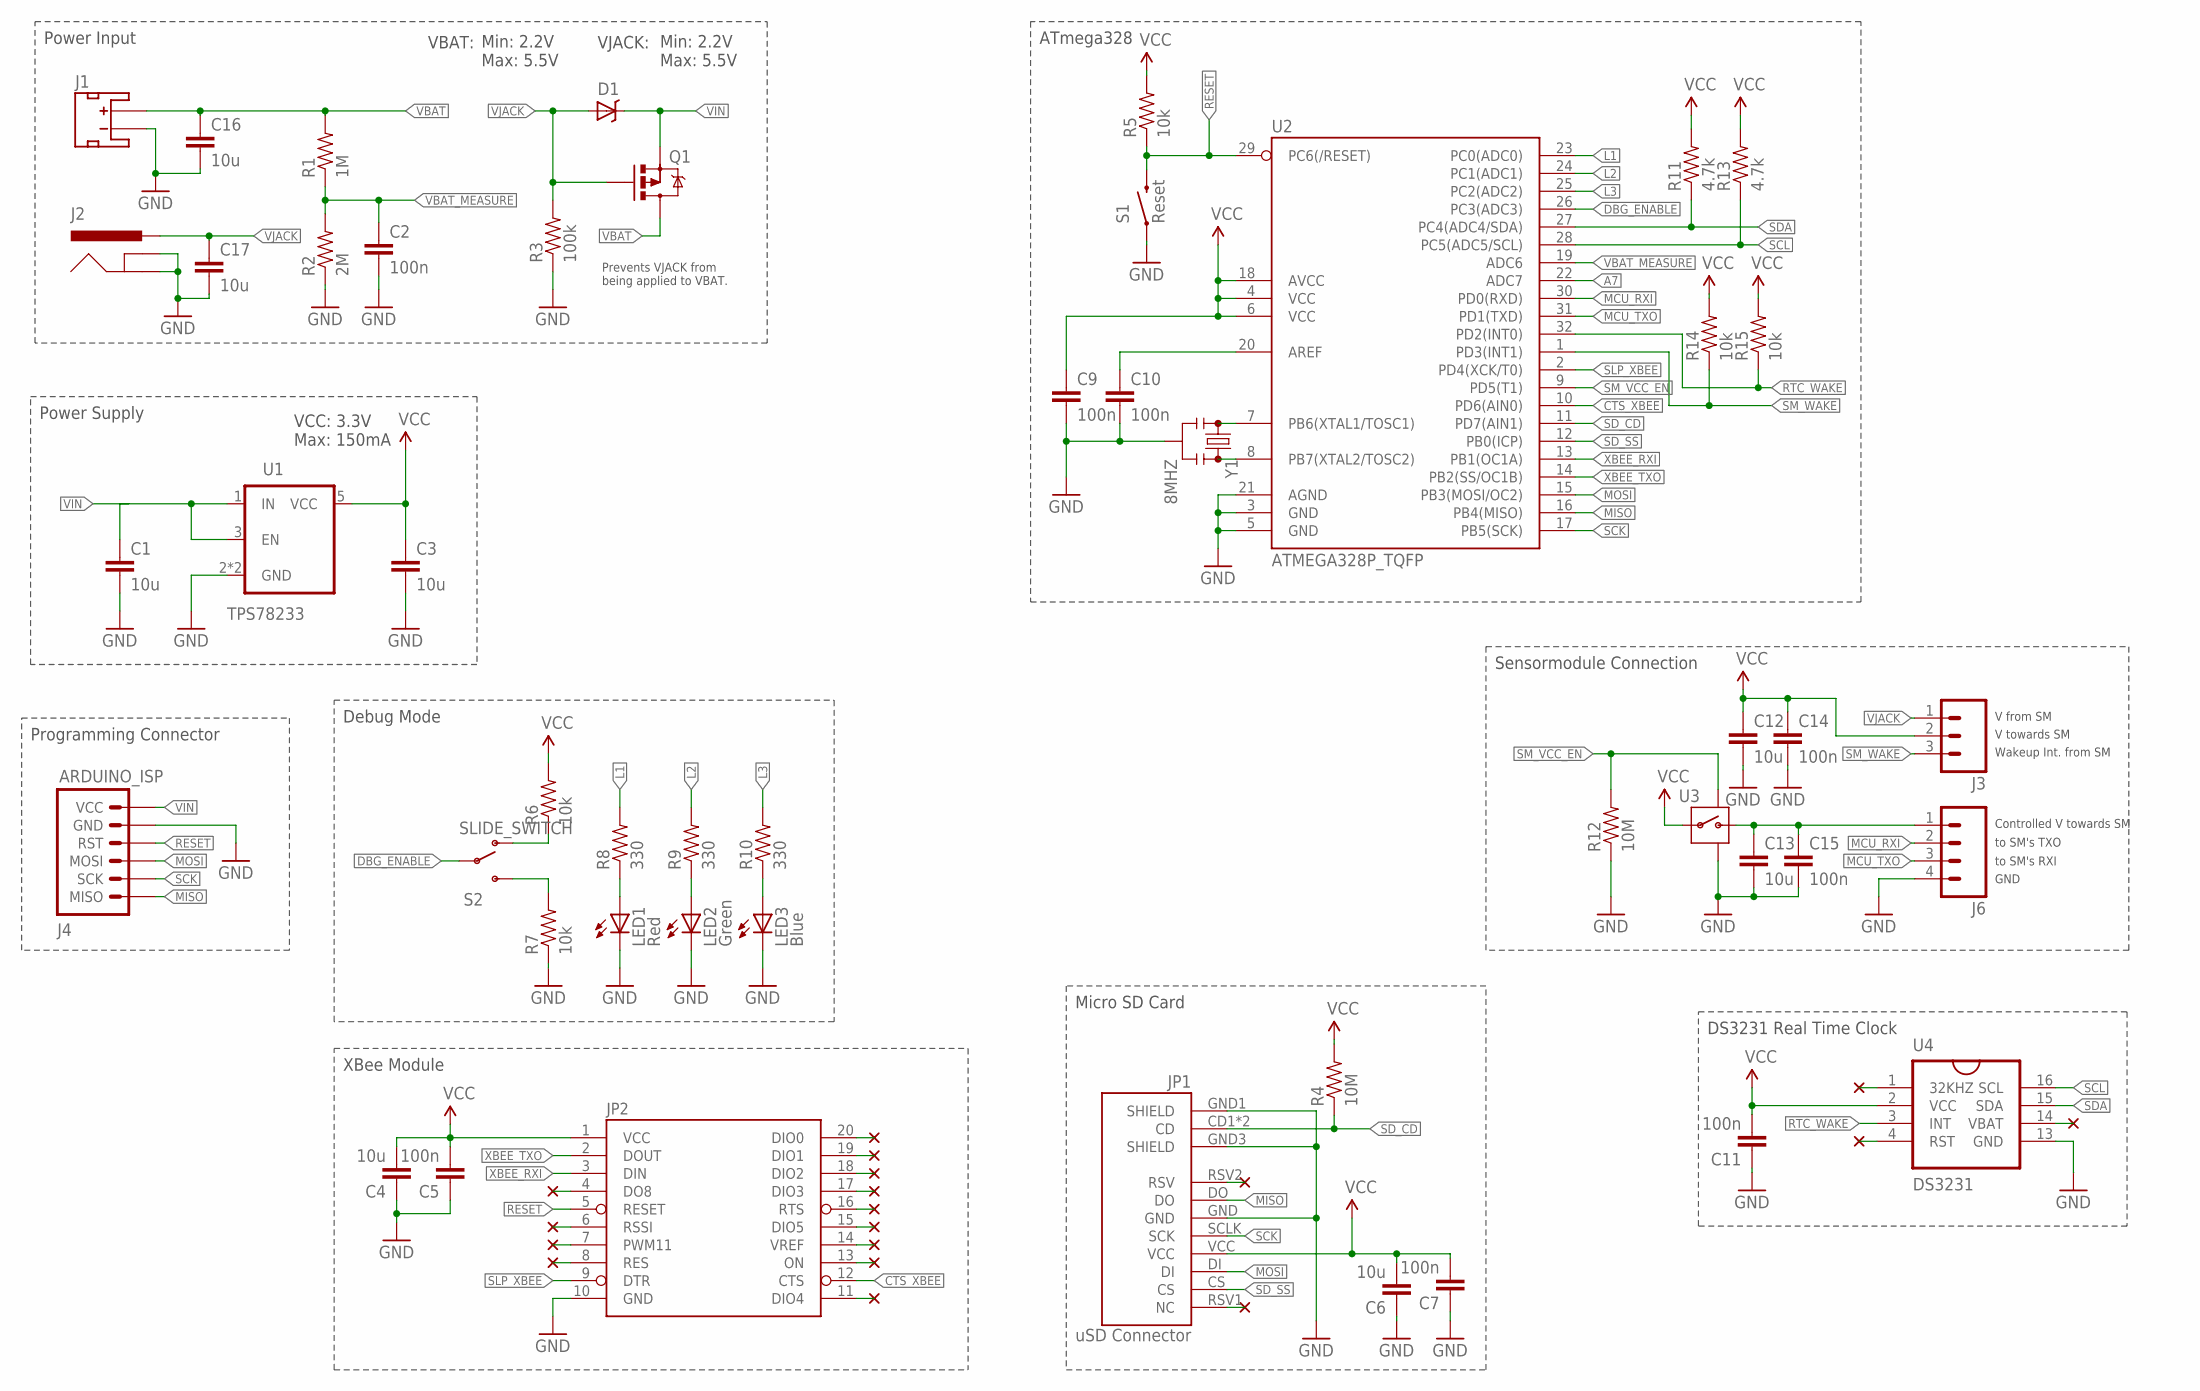
[picture p111: schematic Main_module_v2.sch]

Parts:
C1, C3, C4, C6, C12, C13, C16, C17: 10u; C0805
C2, C5, C7, C9, C10, C11, C14, C15: 100n; C0805
D1: DIODE-SCHOTTKY; 0603-DIODE
J1: JST_2MM_MALE; JST-2-SMD
J2: 5.5x2.1mm Barrel; POWER_JACK_SMD
J3: M03PTH; 1X03
J4: ARDUINO_ISP; M-2X3
J6: M04PTH; 1X04
JP1: USD-SOCKETNEW; MICRO-SD-SOCKET-PP
JP2: XBEEB3; XBEE-SMD
LED1: Red; SML0805
LED2: Green; SML0805
LED3: Blue; SML0805
Q1: PFET; SOT23-3
R1: 1M; 0805
R2: 2M; 0805
R3: 100k; 0805
R4, R12: 10M; 0805
R5, R6, R7, R14, R15: 10k; 0805
R8, R9, R10: 330; 0805
R11, R13: 4.7k; 0805
S1: Reset; M-PUSHBUTTON-SMD
S2: SLIDE_SWITCH; P-JS202011SCQN
U1: TPS78233; SOT23-5
U2: ATMEGA328P_TQFP; TQFP32-08
U3: SIP32431; SC70
U4: DS3231SOIC16; SO016
Y1: 8MHZ; RESONATOR-SMD

Connections:
A7: U2.22 (ADC7)
CTS_XBEE: JP2.12 (CTS), U2.10 (PD6(AIN0))
DBG_ENABLE: S2.P$2 (MIDDLE), S2.P$5 (MIDDLE), U2.26 (PC3(ADC3))
GND: C1.2, C2.2, C3.2, C4.1, C5.1, C6.1, C7.1, C9.2, C10.2, C11.1, C12.2, C13.2, C14.2, C15.2, C16.2, C17.2, J1.1 (-), J2.GND (GNDBREAK), J2.P$4 (GND), J4.P$5 (GND), J6.4, JP1.GND, JP1.GND1 (SHIELD), JP1.GND3 (SHIELD), JP2.10 (GND), LED1.C, LED2.C, LED3.C, R2.1, R3.1, R7.1, R12.1, S1.1 (LEFT), S1.2 (LEFT), U1.2 (GND), U1.4 (GND), U2.3 (GND), U2.5 (GND), U2.21 (AGND), U3.2 (GND), U3.5 (GND), U3.6 (GND), U4.13 (GND), Y1.2
L1: R8.2, U2.23 (PC0(ADC0))
L2: R9.2, U2.24 (PC1(ADC1))
L3: R10.2, U2.25 (PC2(ADC2))
MCU_RXI: J6.2, U2.30 (PD0(RXD))
MCU_TXO: J6.3, U2.31 (PD1(TXD))
MISO: J4.P$1 (MISO), JP1.DO, U2.16 (PB4(MISO))
MOSI: J4.P$3 (MOSI), JP1.DI, U2.15 (PB3(MOSI/OC2))
unnamed: U2.8 (PB7(XTAL2/TOSC2)), Y1.3
unnamed: U2.7 (PB6(XTAL1/TOSC1)), Y1.1
unnamed: LED3.A, R10.1
unnamed: LED2.A, R9.1
unnamed: C13.1, C15.1, J6.1, U3.1 (OUT)
unnamed: C10.1, U2.20 (AREF)
unnamed: LED1.A, R8.1
unnamed: R7.2, S2.P$1 (LOWER), S2.P$4 (LOWER)
unnamed: R6.1, S2.P$3 (UPPER), S2.P$6 (UPPER)
RESET: J4.P$4 (RST), JP2.5 (RESET), R5.1, S1.3 (RIGHT), S1.4 (RIGHT), U2.29 (PC6(/RESET))
RTC_WAKE: R15.1, U2.32 (PD2(INT0)), U4.3 (INT)
SCK: J4.P$2 (SCK), JP1.SCLK (SCK), U2.17 (PB5(SCK))
SCL: R13.1, U2.28 (PC5(ADC5/SCL)), U4.16 (SCL)
SDA: R11.1, U2.27 (PC4(ADC4/SDA)), U4.15 (SDA)
SD_CD: JP1.CD1 (CD), JP1.CD2 (CD), R4.1, U2.11 (PD7(AIN1))
SD_SS: JP1.CS, U2.12 (PB0(ICP))
SLP_XBEE: JP2.9 (DTR), U2.2 (PD4(XCK/T0))
SM_VCC_EN: R12.2, U2.9 (PD5(T1)), U3.3 (ON)
SM_WAKE: J3.3, R14.1, U2.1 (PD3(INT1))
VBAT: C16.1, J1.2 (+), Q1.3 (D), R1.2
VBAT_MEASURE: C2.1, R1.1, R2.2, U2.19 (ADC6)
VCC: C3.1, C4.2, C5.2, C6.2, C7.2, C9.1, C11.2, C12.1, C14.1, J3.2, JP1.VCC, JP2.1 (VCC), R4.2, R5.2, R6.2, R11.2, R13.2, R14.2, R15.2, U1.5 (VCC), U2.4 (VCC), U2.6 (VCC), U2.18 (AVCC), U3.4 (IN), U4.2 (VCC)
VIN: C1.1, D1.C, J4.P$6 (VCC), Q1.2 (S), U1.1 (IN), U1.3 (EN)
VJACK: C17.1, D1.A, J2.VIN0 (PWR), J2.VIN1 (PWR), J3.1, Q1.1 (G), R3.2
XBEE_RXI: JP2.3 (DIN), U2.13 (PB1(OC1A))
XBEE_TXO: JP2.2 (DOUT), U2.14 (PB2(SS/OC1B))

Notes on the sheet:
Min: 2.2V Max: 5.5V
VCC: 3.3V Max: 150mA
Sensormodule Connection
Debug Mode
Power Supply
Micro SD Card
Programming Connector
XBee Module
DS3231 Real Time Clock
ATmega328
Prevents VJACK from being applied to VBAT.
VJACK:
VBAT:
Power Input
V towards SM
V from SM
Wakeup Int. from SM
Controlled V towards SM
to SM's TXO
to SM's RXI
GND

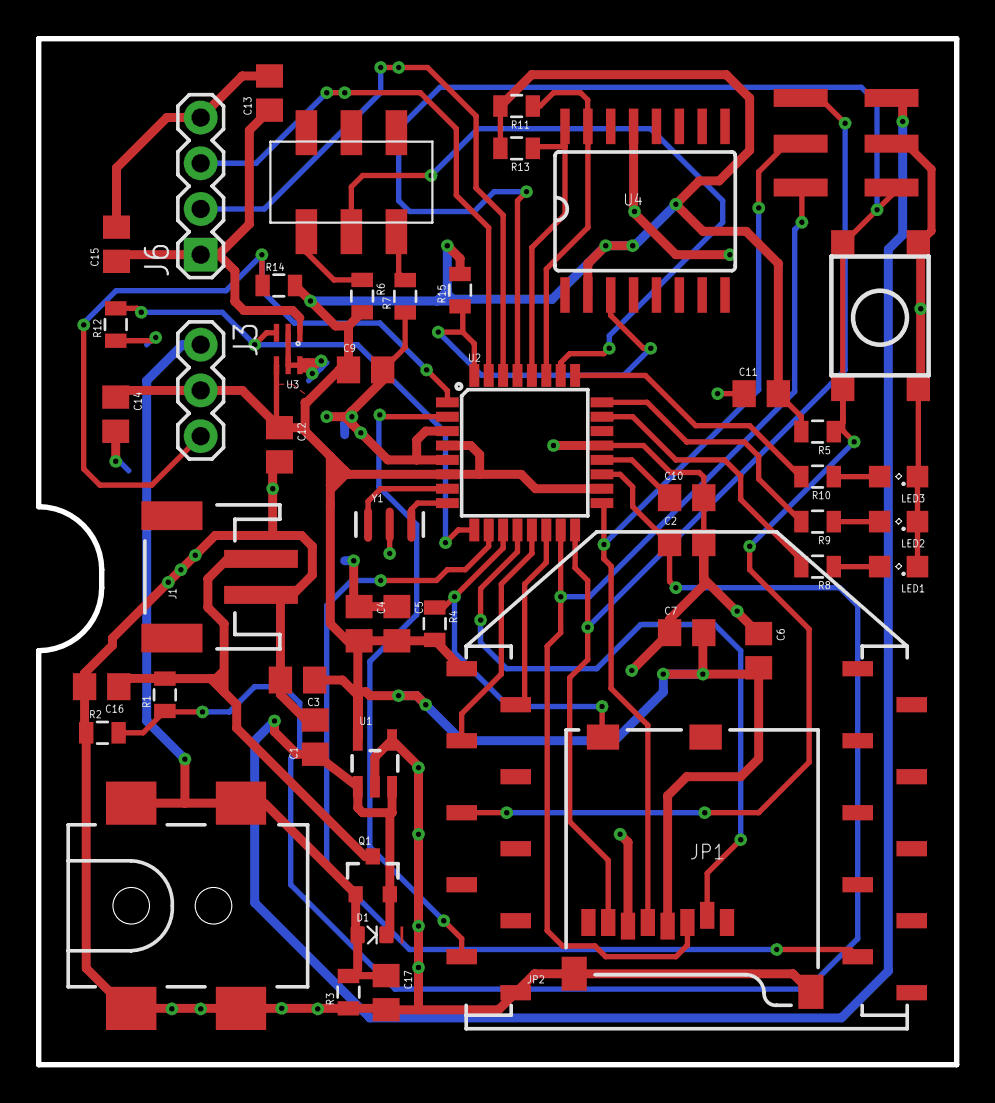
[picture p112: board Main_module_v2.brd from above]

Board: 2 copper layers, 51.0 x 57.0 mm, 50 parts (0 on the bottom side), 36 nets.
