architecture-building-systems/Wireless-Sensor-Network/Sensor_Node/Sensor_modules/Previous Versions/Sensor_Module_0x07_Heat_Flux_v1/Eagle/Sensor_Module_0x07_Heat_Flux.brd

## EAGLE design Sensor_Node/Sensor_modules/Previous Versions/Sensor_Module_0x07_Heat_Flux_v1/Eagle/Sensor_Module_0x07_Heat_Flux.brd (2018-06-01, an earlier design)

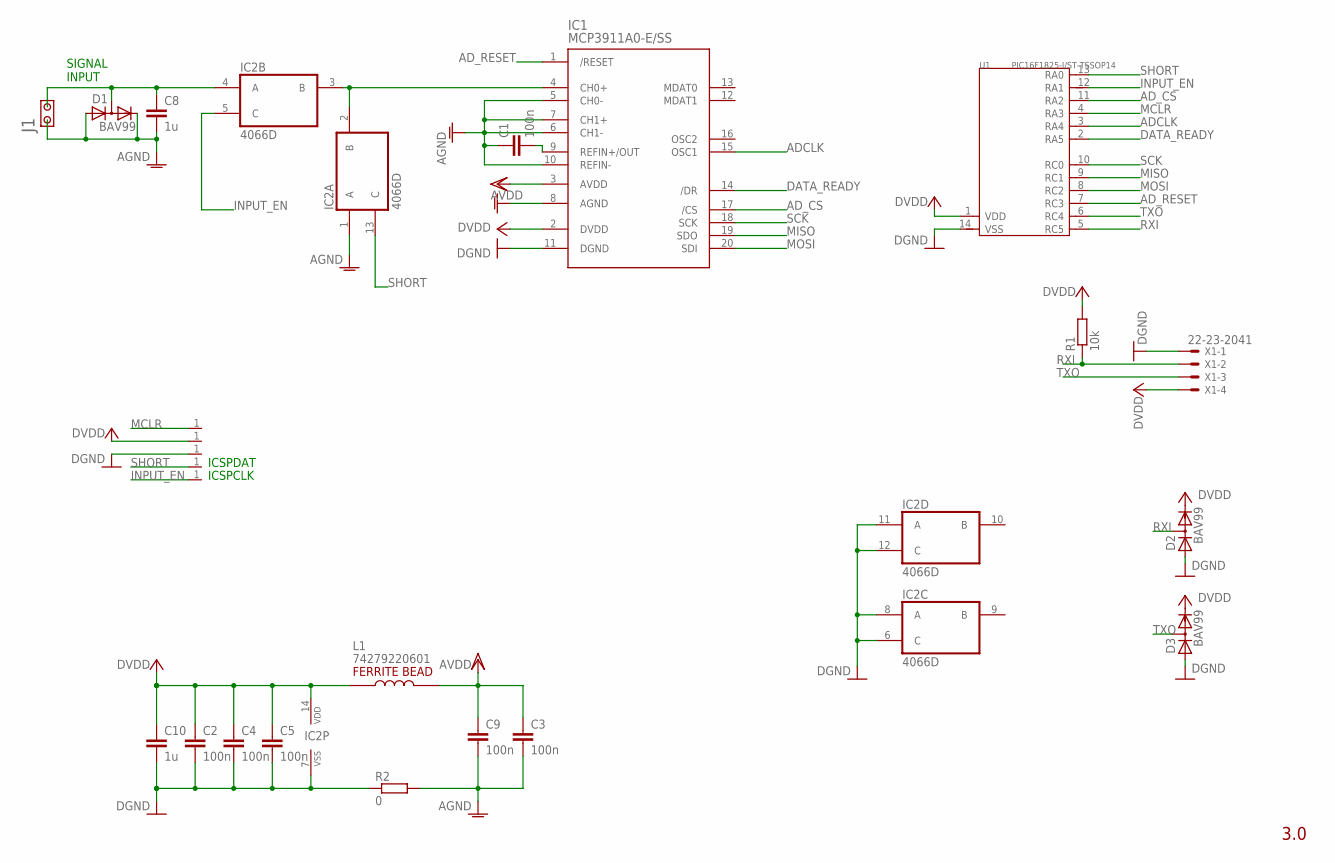
[picture p113: schematic Sensor_Module_0x07_Heat_Flux.sch]

Parts:
C1, C2, C3, C4, C5, C9: 100n; C0805
C8, C10: 1u; C0805
D1, D2, D3: BAV99; SOT23
IC1: MCP3911A0-E/SS; SSOP20
IC2: 4066D; SO14
J1: CON2X1
L1: 74279220601; 0805
PIN1, PIN2, PIN3, PIN4, PIN5: CON1X1
R1: 10k; M0805
R2: 0; M0805
U1: PIC16F1825-I/ST-TSSOP14; TSSOP14-0.65-5X4.4MM
X1: 22-23-2041

Connections:
ADCLK: IC1.15 (OSC1), U1.3 (RA4)
AD_CS: IC1.17 (/CS), U1.11 (RA2)
AD_RESET: IC1.1 (/RESET), U1.7 (RC3)
AGND: C1.1, C3.2, C8.2, C9.2, D1.1 (A), D1.2 (C), IC1.5 (CH0-), IC1.6 (CH1-), IC1.7 (CH1+), IC1.8 (AGND), IC1.10 (REFIN-), IC2.1 (A), J1.1, R2.2
AVDD: C3.1, C9.1, IC1.3 (AVDD), L1.2
DATA_READY: IC1.14 (/DR), U1.2 (RA5)
DGND: C2.2, C4.2, C5.2, C10.2, D2.1 (A), D3.1 (A), IC1.11 (DGND), IC2.6 (C), IC2.7 (VSS), IC2.8 (A), IC2.11 (A), IC2.12 (C), PIN3.1, R2.1, U1.14 (VSS), X1.1
DVDD: C2.1, C4.1, C5.1, C10.1, D2.2 (C), D3.2 (C), IC1.2 (DVDD), IC2.14 (VDD), L1.1, PIN2.1, R1.2, U1.1 (VDD), X1.4
INPUT_EN: IC2.5 (C), PIN5.1, U1.12 (RA1)
MCLR: PIN1.1, U1.4 (RA3)
MISO: IC1.19 (SDO), U1.9 (RC1)
MOSI: IC1.20 (SDI), U1.8 (RC2)
unnamed: C1.2, IC1.9 (REFIN+/OUT)
unnamed: IC1.4 (CH0+), IC2.2 (B), IC2.3 (B)
unnamed: C8.1, D1.3 (AC), IC2.4 (A), J1.2
RXI: D2.3 (AC), R1.1, U1.5 (RC5), X1.2
SCK: IC1.18 (SCK), U1.10 (RC0)
SHORT: IC2.13 (C), PIN4.1, U1.13 (RA0)
TXO: D3.3 (AC), U1.6 (RC4), X1.3

Notes on the sheet:
SIGNAL INPUT
ICSPCLK
ICSPDAT
3.0

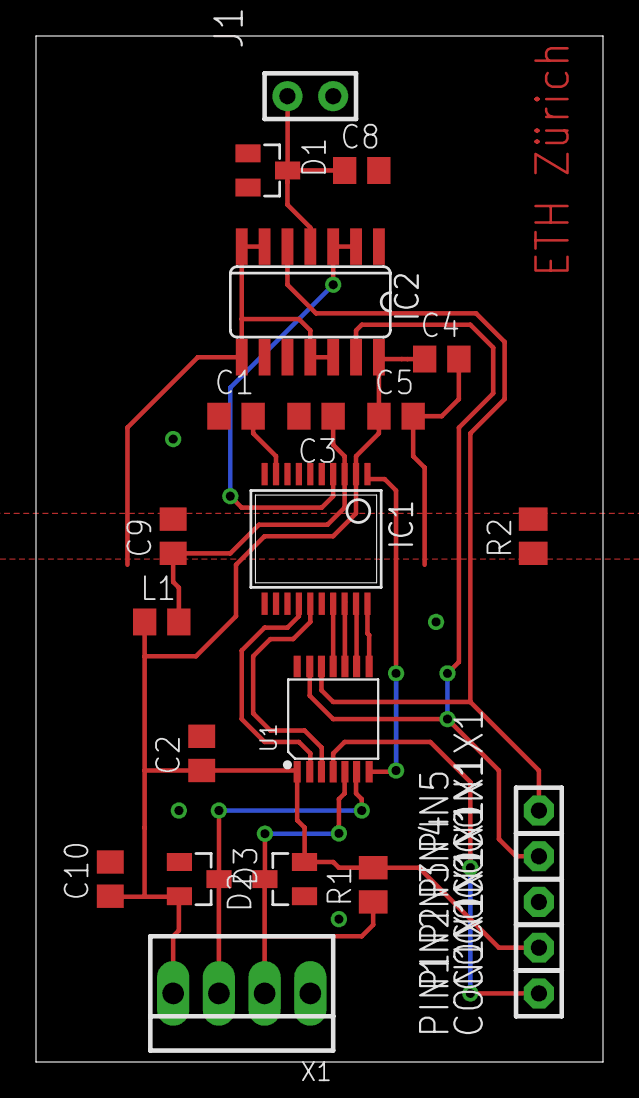
[picture p114: board Sensor_Module_0x07_Heat_Flux.brd from above]

Board: 2 copper layers, 31.5 x 57.0 mm, 24 parts (0 on the bottom side), 19 nets.
