architecture-building-systems/Wireless-Sensor-Network/Sensor_Node/Sensor_modules/Previous Versions/Sensor_Module_0x04_Luminosity_TSL2561_v1/Eagle/Sensor_Module_0x04_Luminosity_TSL2561_v1.brd

## EAGLE design Sensor_Node/Sensor_modules/Previous Versions/Sensor_Module_0x04_Luminosity_TSL2561_v1/Eagle/Sensor_Module_0x04_Luminosity_TSL2561_v1.brd (2018-01-10, an earlier design)

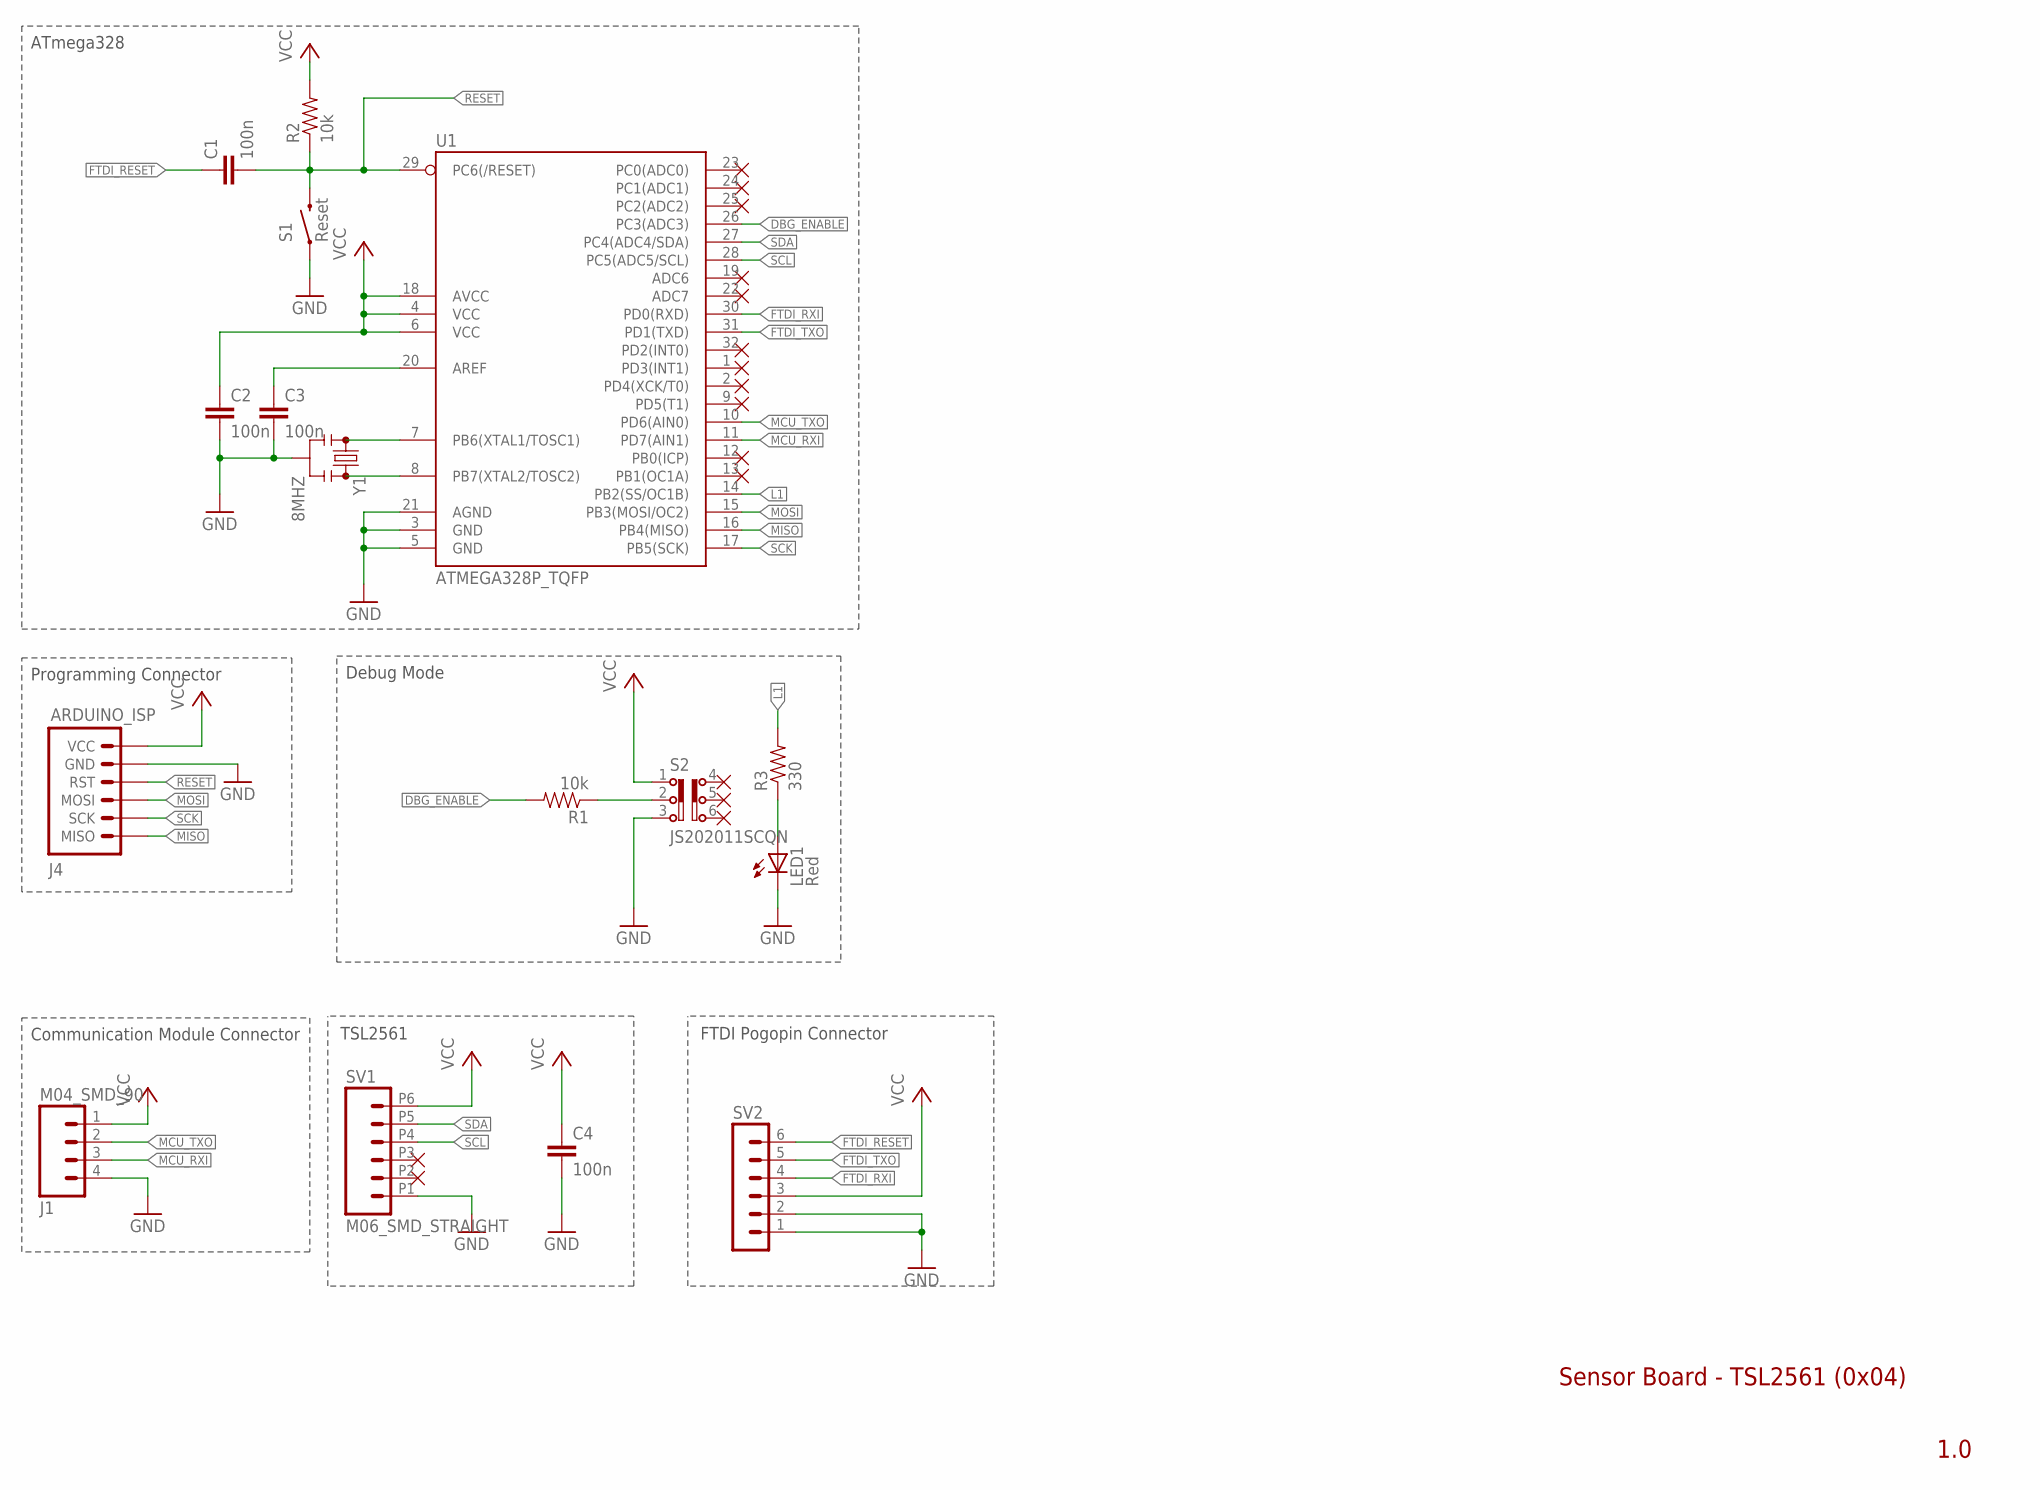
[picture p115: schematic Sensor_Module_0x04_Luminosity_TSL2561_v1.sch]

Parts:
C1, C2, C3, C4: 100n; C0805
J1: M04_SMD_90
J4: ARDUINO_ISP; M-2X3
LED1: Red; SML0805
R1, R2: 10k; 0805
R3: 330; 0805
S1: Reset; M-PUSHBUTTON-SMD
S2: JS202011SCQN
SV1: M06_SMD_STRAIGHT
SV2: MA06-1
U1: ATMEGA328P_TQFP; TQFP32-08
Y1: 8MHZ; RESONATOR-SMD

Connections:
DBG_ENABLE: R1.2, U1.26 (PC3(ADC3))
FTDI_RESET: C1.1, SV2.6
FTDI_RXI: SV2.4, U1.30 (PD0(RXD))
FTDI_TXO: SV2.5, U1.31 (PD1(TXD))
GND: C2.2, C3.2, C4.2, J1.4, J4.P$5 (GND), LED1.C, S1.1 (LEFT), S1.2 (LEFT), S2.3, SV1.P1 (1), SV2.1, SV2.2, U1.3 (GND), U1.5 (GND), U1.21 (AGND), Y1.2
L1: R3.2, U1.14 (PB2(SS/OC1B))
MCU_RXI: J1.3, U1.11 (PD7(AIN1))
MCU_TXO: J1.2, U1.10 (PD6(AIN0))
MISO: J4.P$1 (MISO), U1.16 (PB4(MISO))
MOSI: J4.P$3 (MOSI), U1.15 (PB3(MOSI/OC2))
unnamed: U1.8 (PB7(XTAL2/TOSC2)), Y1.3
unnamed: U1.7 (PB6(XTAL1/TOSC1)), Y1.1
unnamed: R1.1, S2.2
unnamed: C3.1, U1.20 (AREF)
unnamed: LED1.A, R3.1
RESET: C1.2, J4.P$4 (RST), R2.1, S1.3 (RIGHT), S1.4 (RIGHT), U1.29 (PC6(/RESET))
SCK: J4.P$2 (SCK), U1.17 (PB5(SCK))
SCL: SV1.P4 (4), U1.28 (PC5(ADC5/SCL))
SDA: SV1.P5 (5), U1.27 (PC4(ADC4/SDA))
VCC: C2.1, C4.1, J1.1, J4.P$6 (VCC), R2.2, S2.1, SV1.P6 (6), SV2.3, U1.4 (VCC), U1.6 (VCC), U1.18 (AVCC)

Notes on the sheet:
Debug Mode
Programming Connector
ATmega328
Communication Module Connector
TSL2561
Sensor Board - TSL2561 (0x04)
1.0
FTDI Pogopin Connector

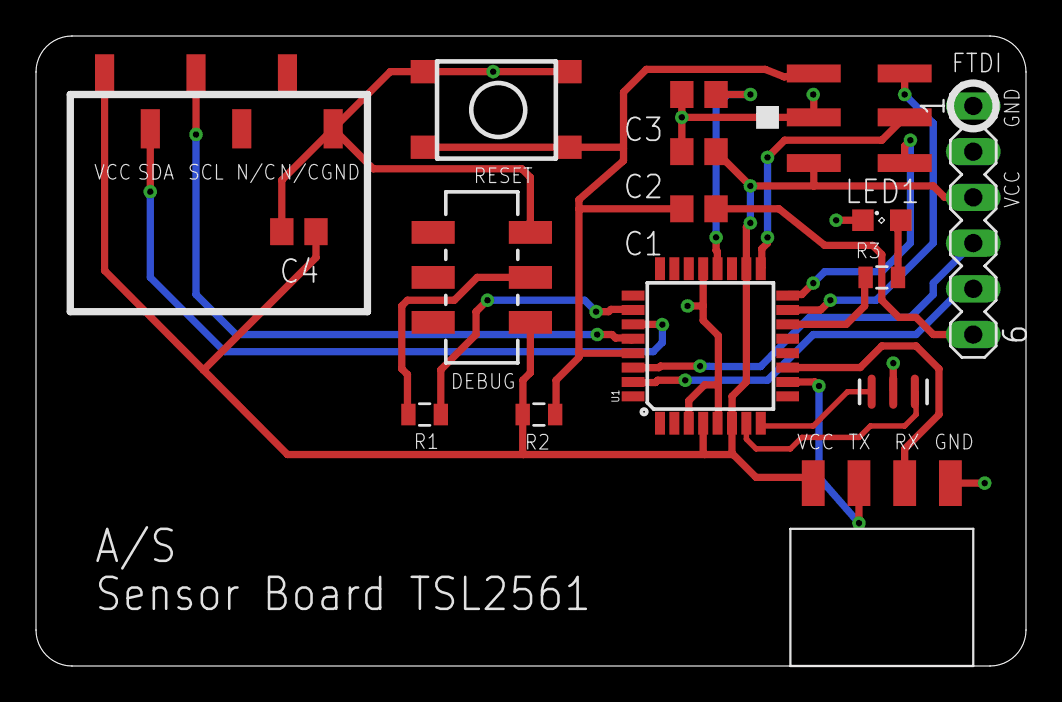
[picture p116: board Sensor_Module_0x04_Luminosity_TSL2561_v1.brd from above]

Board: 2 copper layers, 55.0 x 35.0 mm, 16 parts (0 on the bottom side), 20 nets.
