architecture-building-systems/Wireless-Sensor-Network/Sensor_Node/Sensor_Boards/Sensor_Board_0x12_U-Value/Eagle/Sensor_Board_U-Value.brd

## EAGLE design Sensor_Node/Sensor_Boards/Sensor_Board_0x12_U-Value/Eagle/Sensor_Board_U-Value.brd (2017-06-30)

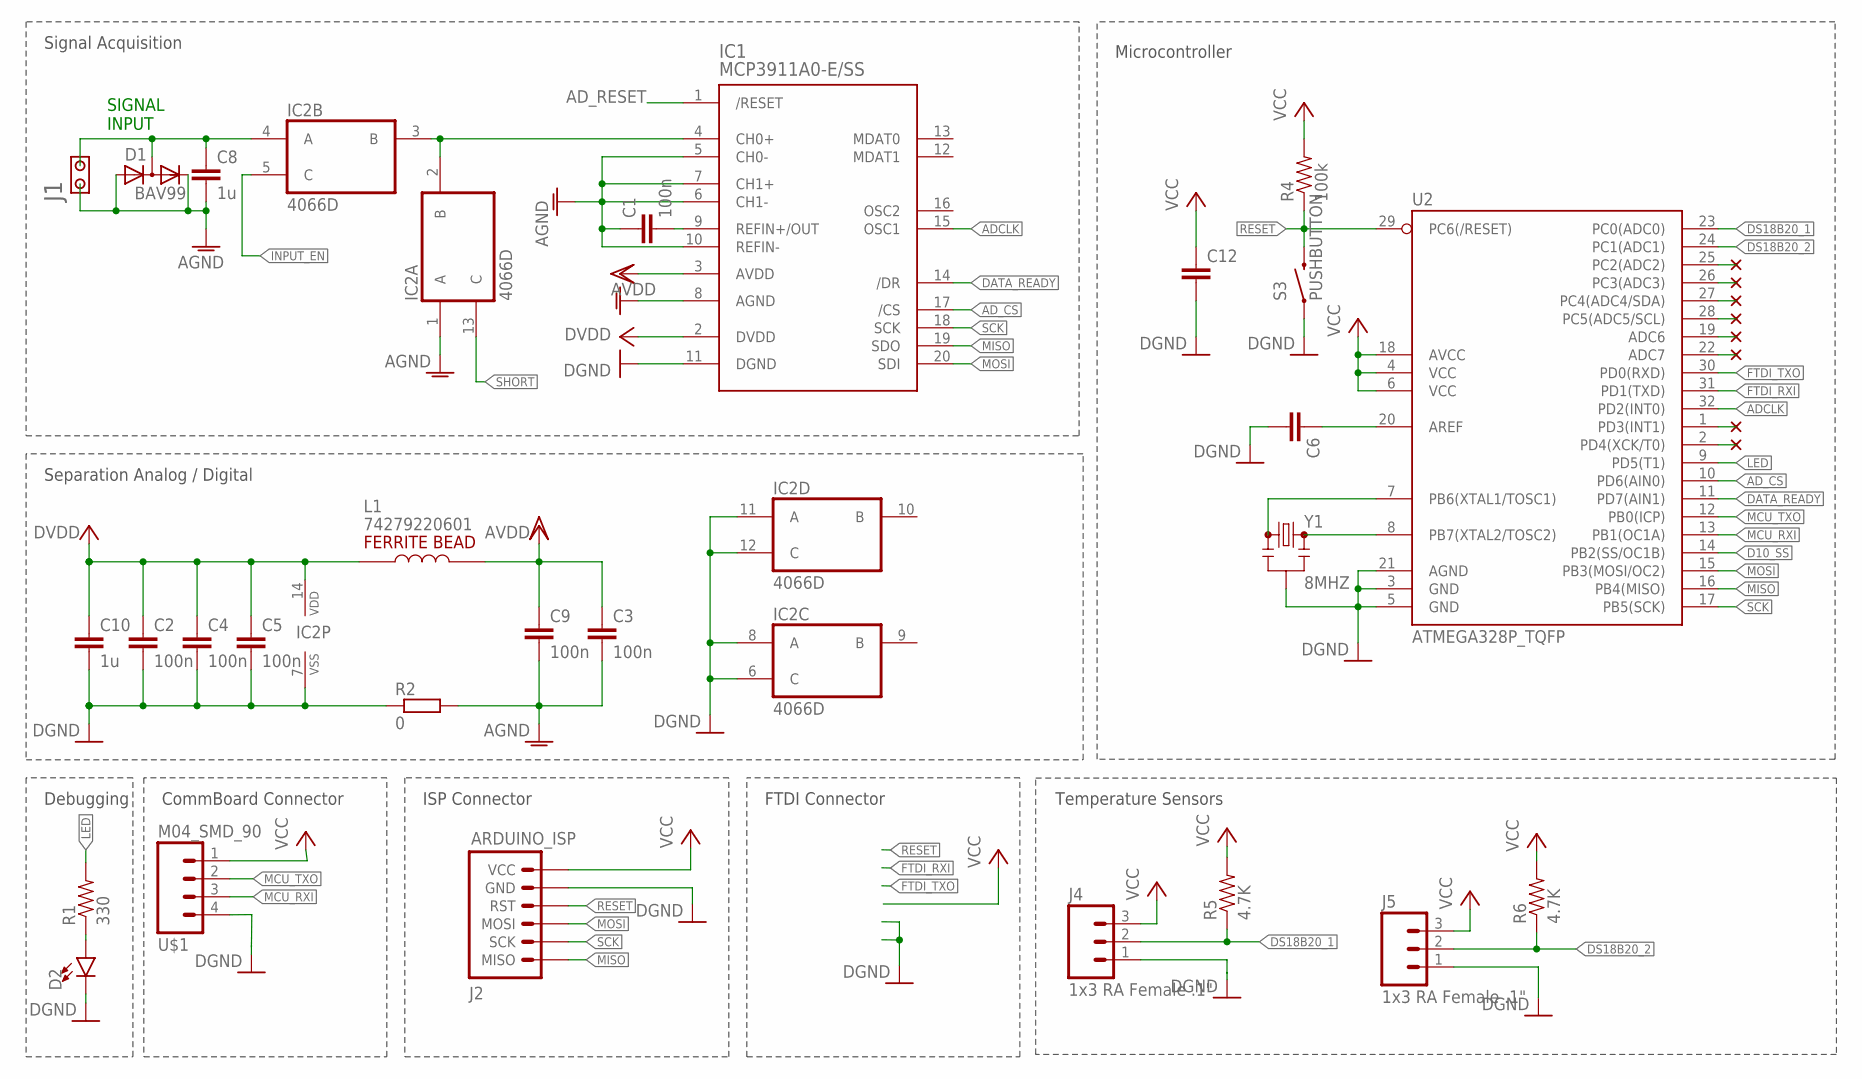
[picture p117: schematic Sensor_Board_U-Value.sch]

Parts:
C1, C2, C3, C4, C5, C9: 100n; C0805
C6, C12: CAP0805; 0805
C8, C10: 1u; C0805
D1: BAV99; SOT23
D2: LED0603; LED-0603
IC1: MCP3911A0-E/SS; SSOP20
IC2: 4066D; SO14
J1: CON2X1
J2: ARDUINO_ISP; M-2X3
J4, J5: 1x3 RA Female .1"; 1X03_SMD_RA_FEMALE
L1: 74279220601; 0805
R1: 330; 0805
R2: 0; M0805
R4: 100k; 0805
R5, R6: 4.7K; 0805
S3: PUSHBUTTON; M-PUSHBUTTON-SMD
U2: ATMEGA328P_TQFP; TQFP32-08
U$1: M04_SMD_90
Y1: 8MHZ; RESONATOR-SMD

Connections:
ADCLK: IC1.15 (OSC1), U2.32 (PD2(INT0))
AD_CS: IC1.17 (/CS), U2.10 (PD6(AIN0))
AD_RESET: IC1.1 (/RESET)
AGND: C1.1, C3.2, C8.2, C9.2, D1.1 (A), D1.2 (C), IC1.5 (CH0-), IC1.6 (CH1-), IC1.7 (CH1+), IC1.8 (AGND), IC1.10 (REFIN-), IC2.1 (A), J1.1, R2.2
AVDD: C3.1, C9.1, IC1.3 (AVDD), L1.2
D10_SS: U2.14 (PB2(SS/OC1B))
DATA_READY: IC1.14 (/DR), U2.11 (PD7(AIN1))
DGND: C2.2, C4.2, C5.2, C10.2, IC1.11 (DGND), IC2.6 (C), IC2.7 (VSS), IC2.8 (A), IC2.11 (A), IC2.12 (C), R2.1
DS18B20_1: J4.2, R5.1, U2.23 (PC0(ADC0))
DS18B20_2: J5.2, R6.1, U2.24 (PC1(ADC1))
DVDD: C2.1, C4.1, C5.1, C10.1, IC1.2 (DVDD), IC2.14 (VDD), L1.1
FTDI_RXI: U2.31 (PD1(TXD))
FTDI_TXO: U2.30 (PD0(RXD))
GND: C6.2, C12.2, D2.C, J2.P$5 (GND), J5.1, S3.1 (LEFT), S3.2 (LEFT), U2.3 (GND), U2.5 (GND), U2.21 (AGND), Y1.2
INPUT_EN: IC2.5 (C)
LED: R1.2, U2.9 (PD5(T1))
MCU_RXI: U2.13 (PB1(OC1A)), U$1.3
MCU_TXO: U2.12 (PB0(ICP)), U$1.2
MISO: IC1.19 (SDO), J2.P$1 (MISO), U2.16 (PB4(MISO))
MOSI: IC1.20 (SDI), J2.P$3 (MOSI), U2.15 (PB3(MOSI/OC2))
unnamed: C1.2, IC1.9 (REFIN+/OUT)
unnamed: C6.1, U2.20 (AREF)
unnamed: IC1.4 (CH0+), IC2.2 (B), IC2.3 (B)
unnamed: C8.1, D1.3 (AC), IC2.4 (A), J1.2
unnamed: U2.8 (PB7(XTAL2/TOSC2)), Y1.3
unnamed: D2.A, R1.1
unnamed: U2.7 (PB6(XTAL1/TOSC1)), Y1.1
RESET: J2.P$4 (RST), R4.1, S3.3 (RIGHT), S3.4 (RIGHT), U2.29 (PC6(/RESET))
SCK: IC1.18 (SCK), J2.P$2 (SCK), U2.17 (PB5(SCK))
SHORT: IC2.13 (C)
VCC: C12.1, J2.P$6 (VCC), J4.3, J5.3, R4.2, R5.2, R6.2, U2.4 (VCC), U2.6 (VCC), U2.18 (AVCC), U$1.1

Notes on the sheet:
SIGNAL INPUT
Debugging
Microcontroller
Signal Acquisition
Separation Analog / Digital
CommBoard Connector
ISP Connector
FTDI Connector
Temperature Sensors

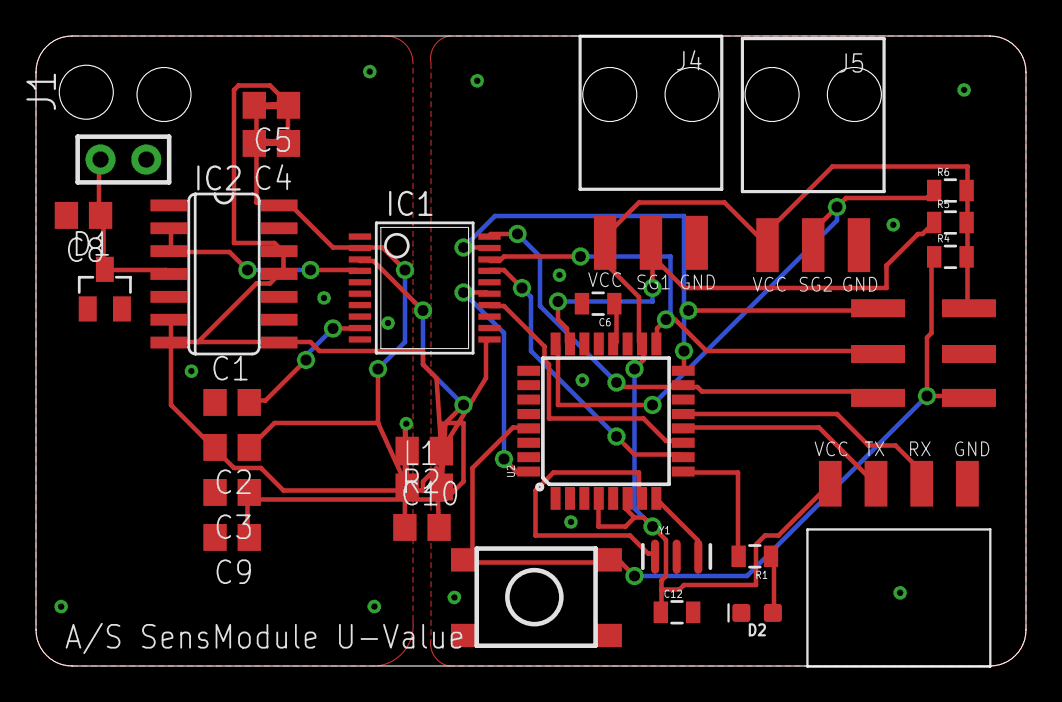
[picture p118: board Sensor_Board_U-Value.brd from above]

Board: 2 copper layers, 55.0 x 35.0 mm, 28 parts (0 on the bottom side), 25 nets.
