architecture-building-systems/Wireless-Sensor-Network/Miscellaneous/Eagle/Sensor_Modules_Combined_Mask_20_01_2018.brd

## EAGLE design Miscellaneous/Eagle/Sensor_Modules_Combined_Mask_20_01_2018.brd (2018-01-22)

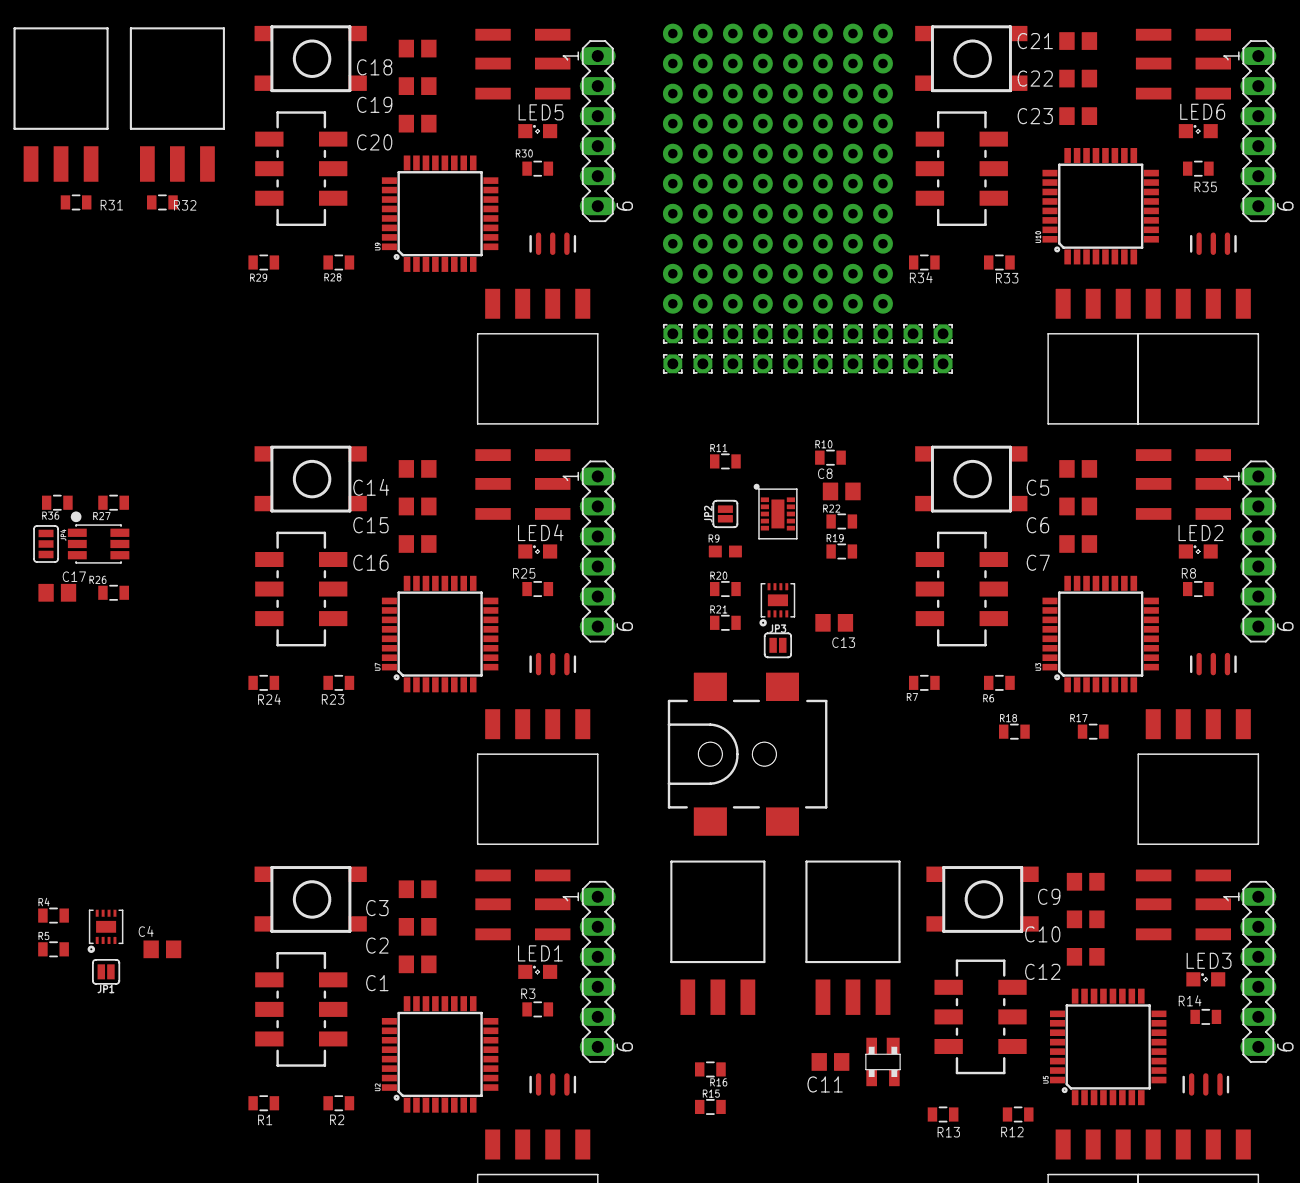
[picture p119: board Sensor_Modules_Combined_Mask_20_01_2018.brd from above]

Board: 2 copper layers, 144 parts (0 on the bottom side), 141 nets, no tracks yet.

Parts:
C1, C2, C3, C4, C5, C6, C7, C8, C9, C10, C11, C12, C13, C14, C15, C16, C17, C18, C19, C20, C21, C22, C23: 100n; C0805
J1, J3, J7, J12: M04_SMD_90
J2, J4, J6, J8, J11: ARDUINO_ISP; M-2X3
J5: 5.5x2.1mm Barrel; POWER_JACK_SMD
J9, J10: 1x3 RA Female .1"; 1X03_SMD_RA_FEMALE
JP1, JP2, JP3: SPARKFUN-JUMPERS_SMT-JUMPER_2_NO_SILK
JP4: MIKE-TEMP_SJ_3
LED1, LED2, LED3, LED4, LED5, LED6: Red; SML0805
PAD1, PAD2, PAD3, PAD4, PAD5, PAD6, PAD7, PAD8, PAD9, PAD10, PAD11, PAD12, PAD13, PAD14, PAD15, PAD16, PAD17, PAD18, PAD19, PAD20: 1,6/0,9
R1, R2, R4, R6, R7, R10, R12, R13, R15, R16, R17, R18, R19, R20, R23, R24, R26, R27, R28, R29, R33, R34, R36: 10k; 0805
R3, R8, R14, R25, R30, R35: 330; 0805
R5, R11, R21, R22: 100k; 0805
R9: 10k; CCS811_BREAKOUT_TEMP_0603
R31, R32: 4.7k; 0805
S1, S2, S5, S7, S9, S11: Reset; M-PUSHBUTTON-SMD
S3, S4, S6, S8, S10, S12: JS202011SCQN
SV1, SV2, SV8, SV9, SV10, SV11: MA06-1
SV3: M03_SMD_90
SV4, SV5: 1x3 RA Female .1"; 1X03_SMD_RA_FEMALE
SV6: ARDUINO_ISP; M-2X3
SV7: M04_SMD_90
U1, U6: MICROBUILDER_SHT3X
U2, U3, U5, U7, U9, U10: ATMEGA328P_TQFP; TQFP32-08
U4: CCS811; CCS811_BREAKOUT_TEMP_LGA10
U8: MIKE-TEMP_TSL2561T; MIKE-TEMP_TMB-6
U$1: M04_SMD_90
U$2: MAX6816EUS; SOT143
U$3: M03_SMD_90
U$4: 10X8_PROTOTYPE_AREA
Y1, Y2, Y3, Y4, Y5, Y6: 8MHZ; RESONATOR-SMD

Connections:
+5V: PAD19.1, PAD20.1, U$3.3
ADC6: PAD3.1, PAD12.1, U10.19
ADC7: PAD4.1, PAD13.1, U10.22
AUX: R9.1, R19.1, U4.8
DBG_ENABLE: R1.2, U2.26
DBG_ENABLE1: R7.2, U3.26
DBG_ENABLE2: R13.2, U5.26
DBG_ENABLE3: R24.2, U7.26
DBG_ENABLE4: R29.2, U9.26
DBG_ENABLE5: R34.2, U10.26
DIGITAL_INPUT_1: U5.32, U$2.OUT
DIGITAL_INPUT_2: R15.1, R16.1, SV5.2, U5.1
DS18B20_DATA_1: J10.2, R31.1, U9.32
DS18B20_DATA_2: J9.2, R32.1, U9.1
FTDI_RESET: C1.1, SV1.6
FTDI_RESET1: C7.1, SV2.6
FTDI_RESET2: C12.1, SV8.6
FTDI_RESET3: C16.1, SV9.6
FTDI_RESET4: C20.1, SV10.6
FTDI_RESET5: C23.1, SV11.6
FTDI_RXI: SV1.4, U2.30
FTDI_RXI1: SV2.4, U3.30
FTDI_RXI2: SV8.4, U5.30
FTDI_RXI3: SV9.4, U7.30
FTDI_RXI4: SV10.4, U9.30
FTDI_RXI5: SV11.4, U10.30
FTDI_TXO: SV1.5, U2.31
FTDI_TXO1: SV2.5, U3.31
FTDI_TXO2: SV8.5, U5.31
FTDI_TXO3: SV9.5, U7.31
FTDI_TXO4: SV10.5, U9.31
FTDI_TXO5: SV11.5, U10.31
GND: C2.2, C3.2, C4.2, J1.4, J4.P$5, JP1.1, LED1.C, S1.1, S1.2, S3.3, SV1.1, SV1.2, U1.7, U1.8, U1.THERMAL, U2.3, U2.5, U2.21, Y1.2
GND1: C5.2, C6.2, C8.2, C13.2, J2.P$5, J3.4, J5.GND, J5.P$4, JP2.1, JP3.1, LED2.C, R22.1, S2.1, S2.2, S4.3, SV2.1, SV2.2, U3.3, U3.5, U3.21, U4.EP, U6.7, U6.8, U6.THERMAL, Y2.2
GND2: C9.2, C10.2, LED3.C, R15.2, S5.1, S5.2, S6.3, SV4.1, SV5.3, SV6.P$5, SV7.4, SV8.1, SV8.2, U5.3, U5.5, U5.21, U$2.GND, Y3.2
GND3: C14.2, C15.2, C17.1, J6.P$5, J7.4, JP4.3, LED4.C, S7.1, S7.2, S8.3, SV9.1, SV9.2, U7.3, U7.5, U7.21, U8.3, Y4.2
GND4: C18.2, C19.2, J8.P$5, J9.1, J10.1, LED5.C, S9.1, S9.2, S10.3, SV10.1, SV10.2, U9.3, U9.5, U9.21, U$1.4, Y5.2
GND5: C21.2, C22.2, J11.P$5, J12.4, LED6.C, S11.1, S11.2, S12.3, SV11.1, SV11.2, U10.3, U10.5, U10.21, U$3.1, U$4.P$1, U$4.P$2, U$4.P$3, U$4.P$4, U$4.P$5, U$4.P$6, U$4.P$7, U$4.P$8, Y6.2
INT0: PAD6.1, PAD15.1, U10.32
INT_TO_COM: SV3.1, U5.2
L1: R3.2, U2.14
L2: R8.2, U3.14
L3: R14.2, U5.14
L4: R25.2, U7.14
L5: R30.2, U9.14
L6: R35.2, U10.14
MCU_RXI: J1.3, U2.11
MCU_RXI1: J3.3, U3.11
MCU_RXI2: SV7.3, U5.11
MCU_RXI3: J7.3, U7.11
MCU_RXI4: U9.11, U$1.3
MCU_RXI5: J12.3, U10.11
MCU_TXO: J1.2, U2.10
MCU_TXO1: J3.2, U3.10
MCU_TXO2: SV7.2, U5.10
MCU_TXO3: J7.2, U7.10
MCU_TXO4: U9.10, U$1.2
MCU_TXO5: J12.2, U10.10
MISO: J4.P$1, U2.16
MISO1: J2.P$1, U3.16
MISO2: SV6.P$1, U5.16
MISO3: J6.P$1, U7.16
MISO4: J8.P$1, U9.16
MISO5: J11.P$1, U10.16
MOSI: J4.P$3, U2.15
MOSI1: J2.P$3, U3.15
MOSI2: SV6.P$3, U5.15
MOSI3: J6.P$3, U7.15
MOSI4: J8.P$3, U9.15
MOSI5: J11.P$3, U10.15
unnamed: U2.8, Y1.3
unnamed: U2.7, Y1.1
unnamed: R1.1, S3.2
unnamed: R4.1, U1.6
unnamed: JP1.2, R5.1, U1.2
unnamed: U3.8, Y2.3
unnamed: U3.7, Y2.1
unnamed: LED2.A, R8.1
unnamed: C5.1, U3.20
unnamed: R7.1, S4.2
unnamed: JP2.2, R11.1, U4.1
unnamed: R20.1, U6.6
unnamed: U5.8, Y3.3
unnamed: U5.7, Y3.1
unnamed: C3.1, U2.20
unnamed: LED3.A, R14.1
unnamed: C9.1, U5.20
unnamed: SV4.2, U$2.IN
unnamed: R13.1, S6.2
unnamed: JP3.2, R21.1, U6.2
unnamed: R22.2, U4.7
unnamed: U7.8, Y4.3
unnamed: U7.7, Y4.1
unnamed: LED4.A, R25.1
unnamed: C14.1, U7.20
unnamed: R24.1, S8.2
unnamed: JP4.1, R36.1
unnamed: U9.8, Y5.3
unnamed: U9.7, Y5.1
unnamed: LED1.A, R3.1
unnamed: LED5.A, R30.1
unnamed: C18.1, U9.20
unnamed: R29.1, S10.2
unnamed: U10.8, Y6.3
unnamed: U10.7, Y6.1
unnamed: LED6.A, R35.1
unnamed: C21.1, U10.20
unnamed: R34.1, S12.2
unnamed: JP4.2, U8.2
NTC_SENSE: R9.2, U4.4, U4.5
PC0: PAD7.1, PAD16.1, U10.23
PC1: PAD8.1, PAD17.1, U10.24
PC2: PAD9.1, PAD18.1, U10.25
RESET: C1.2, J4.P$4, R2.1, S1.3, S1.4, U2.29
RESET1: C7.2, J2.P$4, R6.1, S2.3, S2.4, U3.29
RESET2: C12.2, R12.1, S5.3, S5.4, SV6.P$4, U5.29
RESET3: C16.2, J6.P$4, R23.1, S7.3, S7.4, U7.29
RESET4: C20.2, J8.P$4, R28.1, S9.3, S9.4, U9.29
RESET5: C23.2, J11.P$4, R33.1, S11.3, S11.4, U10.29
SCK: J4.P$2, U2.17
SCK1: J2.P$2, U3.17
SCK2: SV6.P$2, U5.17
SCK3: J6.P$2, U7.17
SCK4: J8.P$2, U9.17
SCK5: J11.P$2, U10.17
SCL: U1.4, U2.28
SCL1: R18.1, U3.28, U4.10, U6.4
SCL2: R26.1, U7.28, U8.4
SCL3: PAD2.1, PAD11.1, U10.28
SDA: U1.1, U2.27
SDA1: R17.1, U3.27, U4.9, U6.1
SDA2: R27.1, U7.27, U8.6
SDA3: PAD1.1, PAD10.1, U10.27
SENS_RES: R10.1, U4.2
VCC: C2.1, C4.1, J1.1, J4.P$6, R2.2, R4.2, R5.2, S3.1, SV1.3, U1.5, U2.4, U2.6, U2.18
VCC1: C6.1, C8.1, C13.1, J2.P$6, J3.1, J5.VIN0, J5.VIN1, R6.2, R10.2, R11.2, R17.2, R18.2, R19.2, R20.2, R21.2, S4.1, SV2.3, U3.4, U3.6, U3.18, U4.6, U6.5
VCC2: C10.1, R12.2, R16.2, S6.1, SV5.1, SV6.P$6, SV7.1, SV8.3, U5.4, U5.6, U5.18
VCC3: C15.1, C17.2, J6.P$6, J7.1, R23.2, R26.2, R27.2, R36.2, S8.1, SV9.3, U7.4, U7.6, U7.18, U8.1
VCC4: C19.1, J8.P$6, J9.3, J10.3, R28.2, R31.2, R32.2, S10.1, SV10.3, U9.4, U9.6, U9.18, U$1.1
VCC5: C22.1, J11.P$6, J12.1, PAD5.1, PAD14.1, R33.2, S12.1, SV11.3, U10.4, U10.6, U10.18, U$3.2
VDD: C11.1, SV3.2, U$2.VCC
