architecture-building-systems/Wireless-Sensor-Network/Sensor_Node/Sensor_Boards/Sensor_Board_0x08_Dual_Temperatures_2xDS18B20_v1/Eagle/Sensor_Board_0x08_Dual_Temperatures_2xDS18B20_v1.brd

## EAGLE design Sensor_Node/Sensor_Boards/Sensor_Board_0x08_Dual_Temperatures_2xDS18B20_v1/Eagle/Sensor_Board_0x08_Dual_Temperatures_2xDS18B20_v1.brd (2017-08-06)

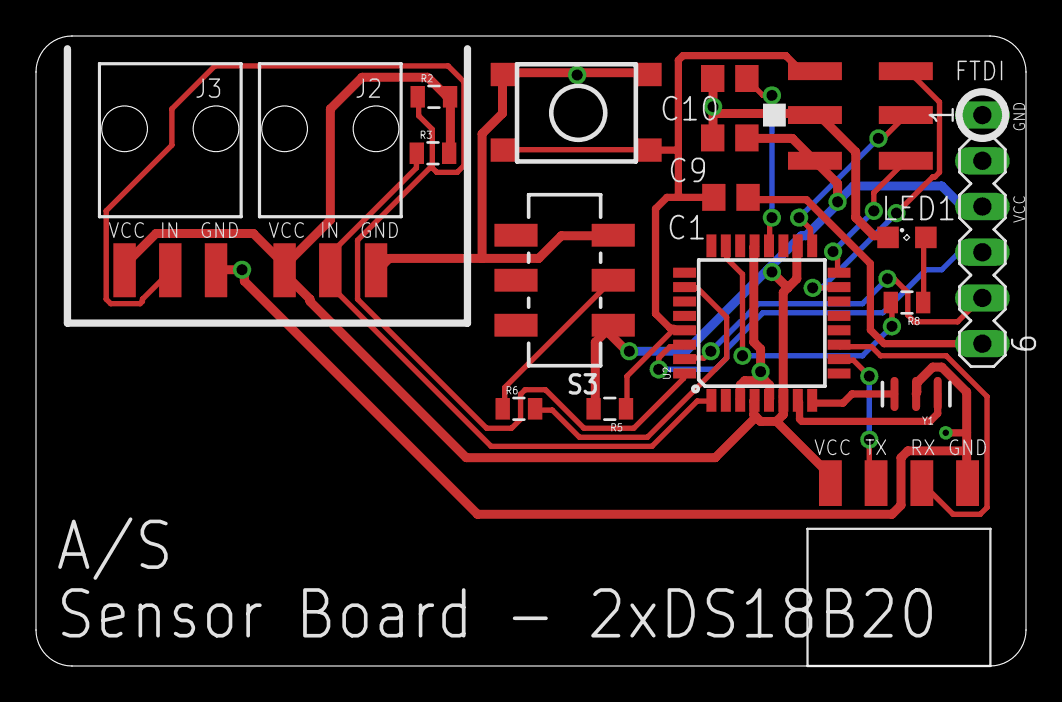
[picture p120: board Sensor_Board_0x08_Dual_Temperatures_2xDS18B20_v1.brd from above]

Board: 2 copper layers, 55.0 x 35.0 mm, 18 parts (0 on the bottom side), 20 nets.

Parts:
C1, C9, C10: 100n; C0805
J2, J3: 1x3 RA Female .1"; 1X03_SMD_RA_FEMALE
J4: ARDUINO_ISP; M-2X3
LED1: Red; SML0805
R2, R3: 4.7k; 0805
R5, R6: 10k; 0805
R8: 330; 0805
S1: Reset; M-PUSHBUTTON-SMD
S3: JS202011SCQN
SV1: MA06-1
U2: ATMEGA328P_TQFP; TQFP32-08
U$1: M04_SMD_90
Y1: 8MHZ; RESONATOR-SMD

Connections:
DBG_ENABLE: R6.2, U2.26
DS18B20_DATA_1: J3.2, R2.1, U2.32
DS18B20_DATA_2: J2.2, R3.1, U2.1
FTDI_RESET: C1.1, SV1.6
FTDI_RXI: SV1.4, U2.30
FTDI_TXO: SV1.5, U2.31
GND: C9.2, C10.2, J2.1, J3.1, J4.P$5, LED1.C, S1.1, S1.2, S3.3, SV1.1, SV1.2, U2.3, U2.5, U2.21, U$1.4, Y1.2
L1: R8.2, U2.23
MCU_RXI: U2.11, U$1.3
MCU_TXO: U2.10, U$1.2
MISO: J4.P$1, U2.16
MOSI: J4.P$3, U2.15
unnamed: U2.8, Y1.3
unnamed: U2.7, Y1.1
unnamed: R6.1, S3.2
unnamed: C10.1, U2.20
unnamed: LED1.A, R8.1
RESET: C1.2, J4.P$4, R5.1, S1.3, S1.4, U2.29
SCK: J4.P$2, U2.17
VCC: C9.1, J2.3, J3.3, J4.P$6, R2.2, R3.2, R5.2, S3.1, SV1.3, U2.4, U2.6, U2.18, U$1.1
