architecture-building-systems/Wireless-Sensor-Network/Sensor_Node/Sensor_Boards/Sensor_Board_0x04_Luminosity_TSL2561_v2/Eagle/Sensor_Board_0x04_Luminosity_TSL2561_v2.sch

## EAGLE design Sensor_Node/Sensor_Boards/Sensor_Board_0x04_Luminosity_TSL2561_v2/Eagle/Sensor_Board_0x04_Luminosity_TSL2561_v2.sch (2018-01-10)

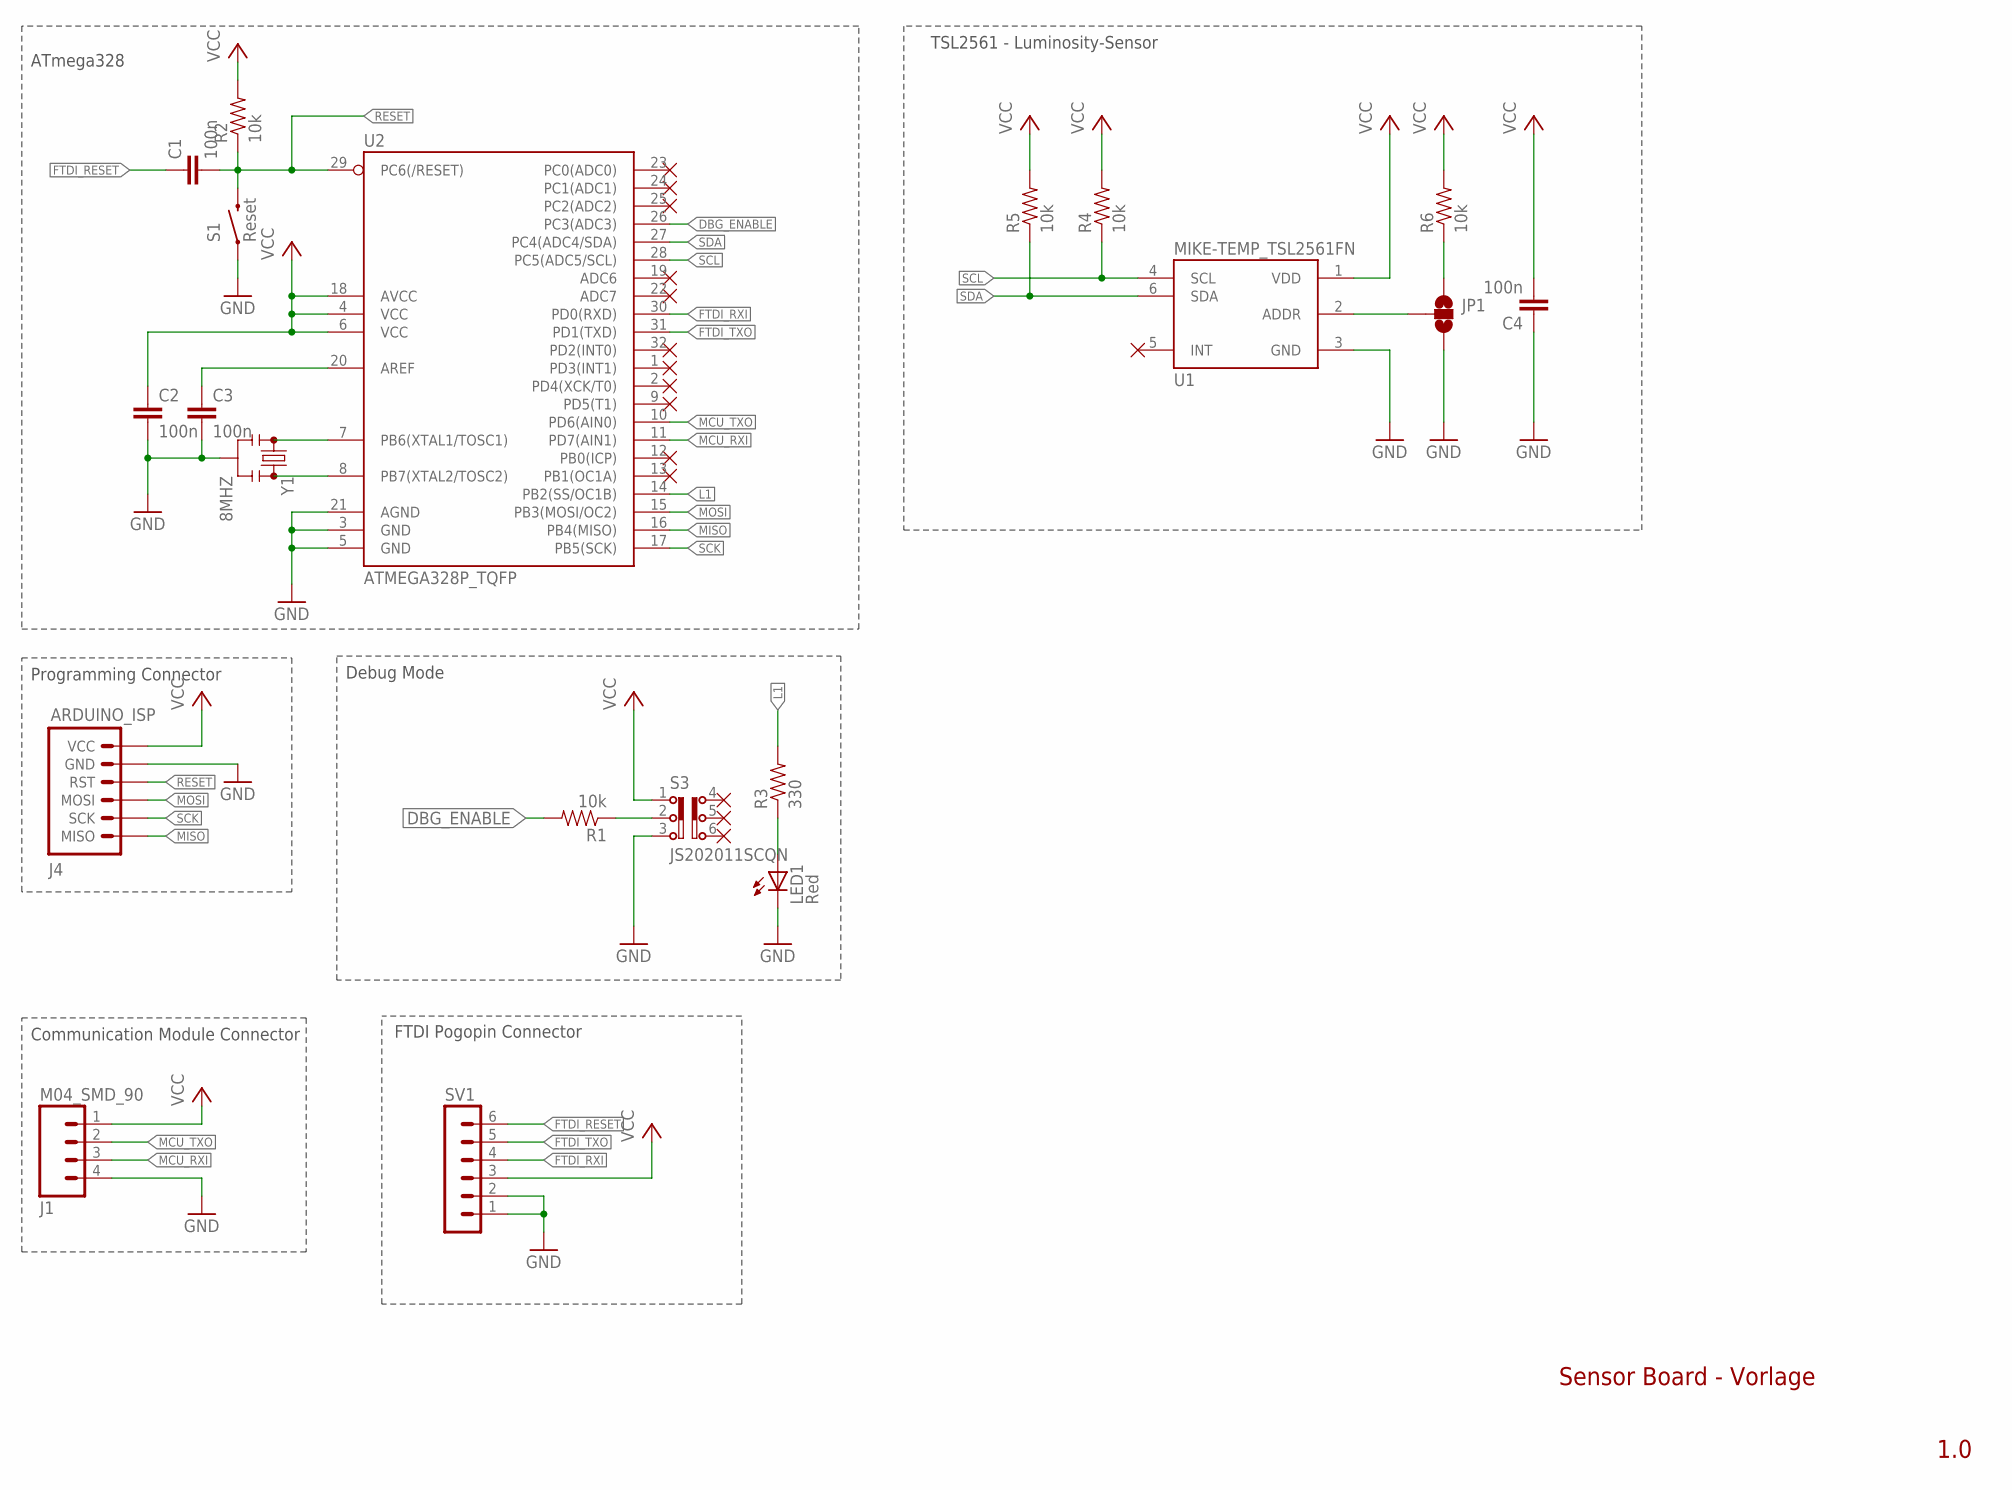
[picture p121: schematic Sensor_Board_0x04_Luminosity_TSL2561_v2.sch]

Parts:
C1, C2, C3, C4: 100n; C0805
J1: M04_SMD_90
J4: ARDUINO_ISP; M-2X3
JP1: MIKE-TEMP_SOLDERJUMPER_2WAYS; MIKE-TEMP_SJ_3
LED1: Red; SML0805
R1, R2, R4, R5, R6: 10k; 0805
R3: 330; 0805
S1: Reset; M-PUSHBUTTON-SMD
S3: JS202011SCQN
SV1: MA06-1
U1: MIKE-TEMP_TSL2561FN; MIKE-TEMP_FN-6
U2: ATMEGA328P_TQFP; TQFP32-08
Y1: 8MHZ; RESONATOR-SMD

Connections:
DBG_ENABLE: R1.2, U2.26 (PC3(ADC3))
FTDI_RESET: C1.1, SV1.6
FTDI_RXI: SV1.4, U2.30 (PD0(RXD))
FTDI_TXO: SV1.5, U2.31 (PD1(TXD))
GND: C2.2, C3.2, C4.1, J1.4, J4.P$5 (GND), JP1.3, LED1.C, S1.1 (LEFT), S3.3, SV1.1, SV1.2, U1.3 (GND), U2.3 (GND), U2.5 (GND), U2.21 (AGND), Y1.2
L1: R3.2, U2.14 (PB2(SS/OC1B))
MCU_RXI: J1.3, U2.11 (PD7(AIN1))
MCU_TXO: J1.2, U2.10 (PD6(AIN0))
MISO: J4.P$1 (MISO), U2.16 (PB4(MISO))
MOSI: J4.P$3 (MOSI), U2.15 (PB3(MOSI/OC2))
unnamed: U2.8 (PB7(XTAL2/TOSC2)), Y1.3
unnamed: U2.7 (PB6(XTAL1/TOSC1)), Y1.1
unnamed: R1.1, S3.2
unnamed: JP1.1, R6.1
unnamed: JP1.2, U1.2 (ADDR)
unnamed: C3.1, U2.20 (AREF)
unnamed: LED1.A, R3.1
RESET: C1.2, J4.P$4 (RST), R2.1, S1.3 (RIGHT), U2.29 (PC6(/RESET))
SCK: J4.P$2 (SCK), U2.17 (PB5(SCK))
SCL: R4.1, U1.4 (SCL), U2.28 (PC5(ADC5/SCL))
SDA: R5.1, U1.6 (SDA), U2.27 (PC4(ADC4/SDA))
VCC: C2.1, C4.2, J1.1, J4.P$6 (VCC), R2.2, R4.2, R5.2, R6.2, S3.1, SV1.3, U1.1 (VDD), U2.4 (VCC), U2.6 (VCC), U2.18 (AVCC)

Notes on the sheet:
Debug Mode
Programming Connector
ATmega328
Communication Module Connector
Sensor Board - Vorlage
1.0
FTDI Pogopin Connector
TSL2561 - Luminosity-Sensor
