architecture-building-systems/Wireless-Sensor-Network/Sensor_Node/Sensor_Boards/Sensor_Board_0x06_CO2_CCS811_v2/Eagle/Sensor_Board_0x06_CO2_CCS811_v2.sch

## EAGLE design Sensor_Node/Sensor_Boards/Sensor_Board_0x06_CO2_CCS811_v2/Eagle/Sensor_Board_0x06_CO2_CCS811_v2.sch (2018-01-10)

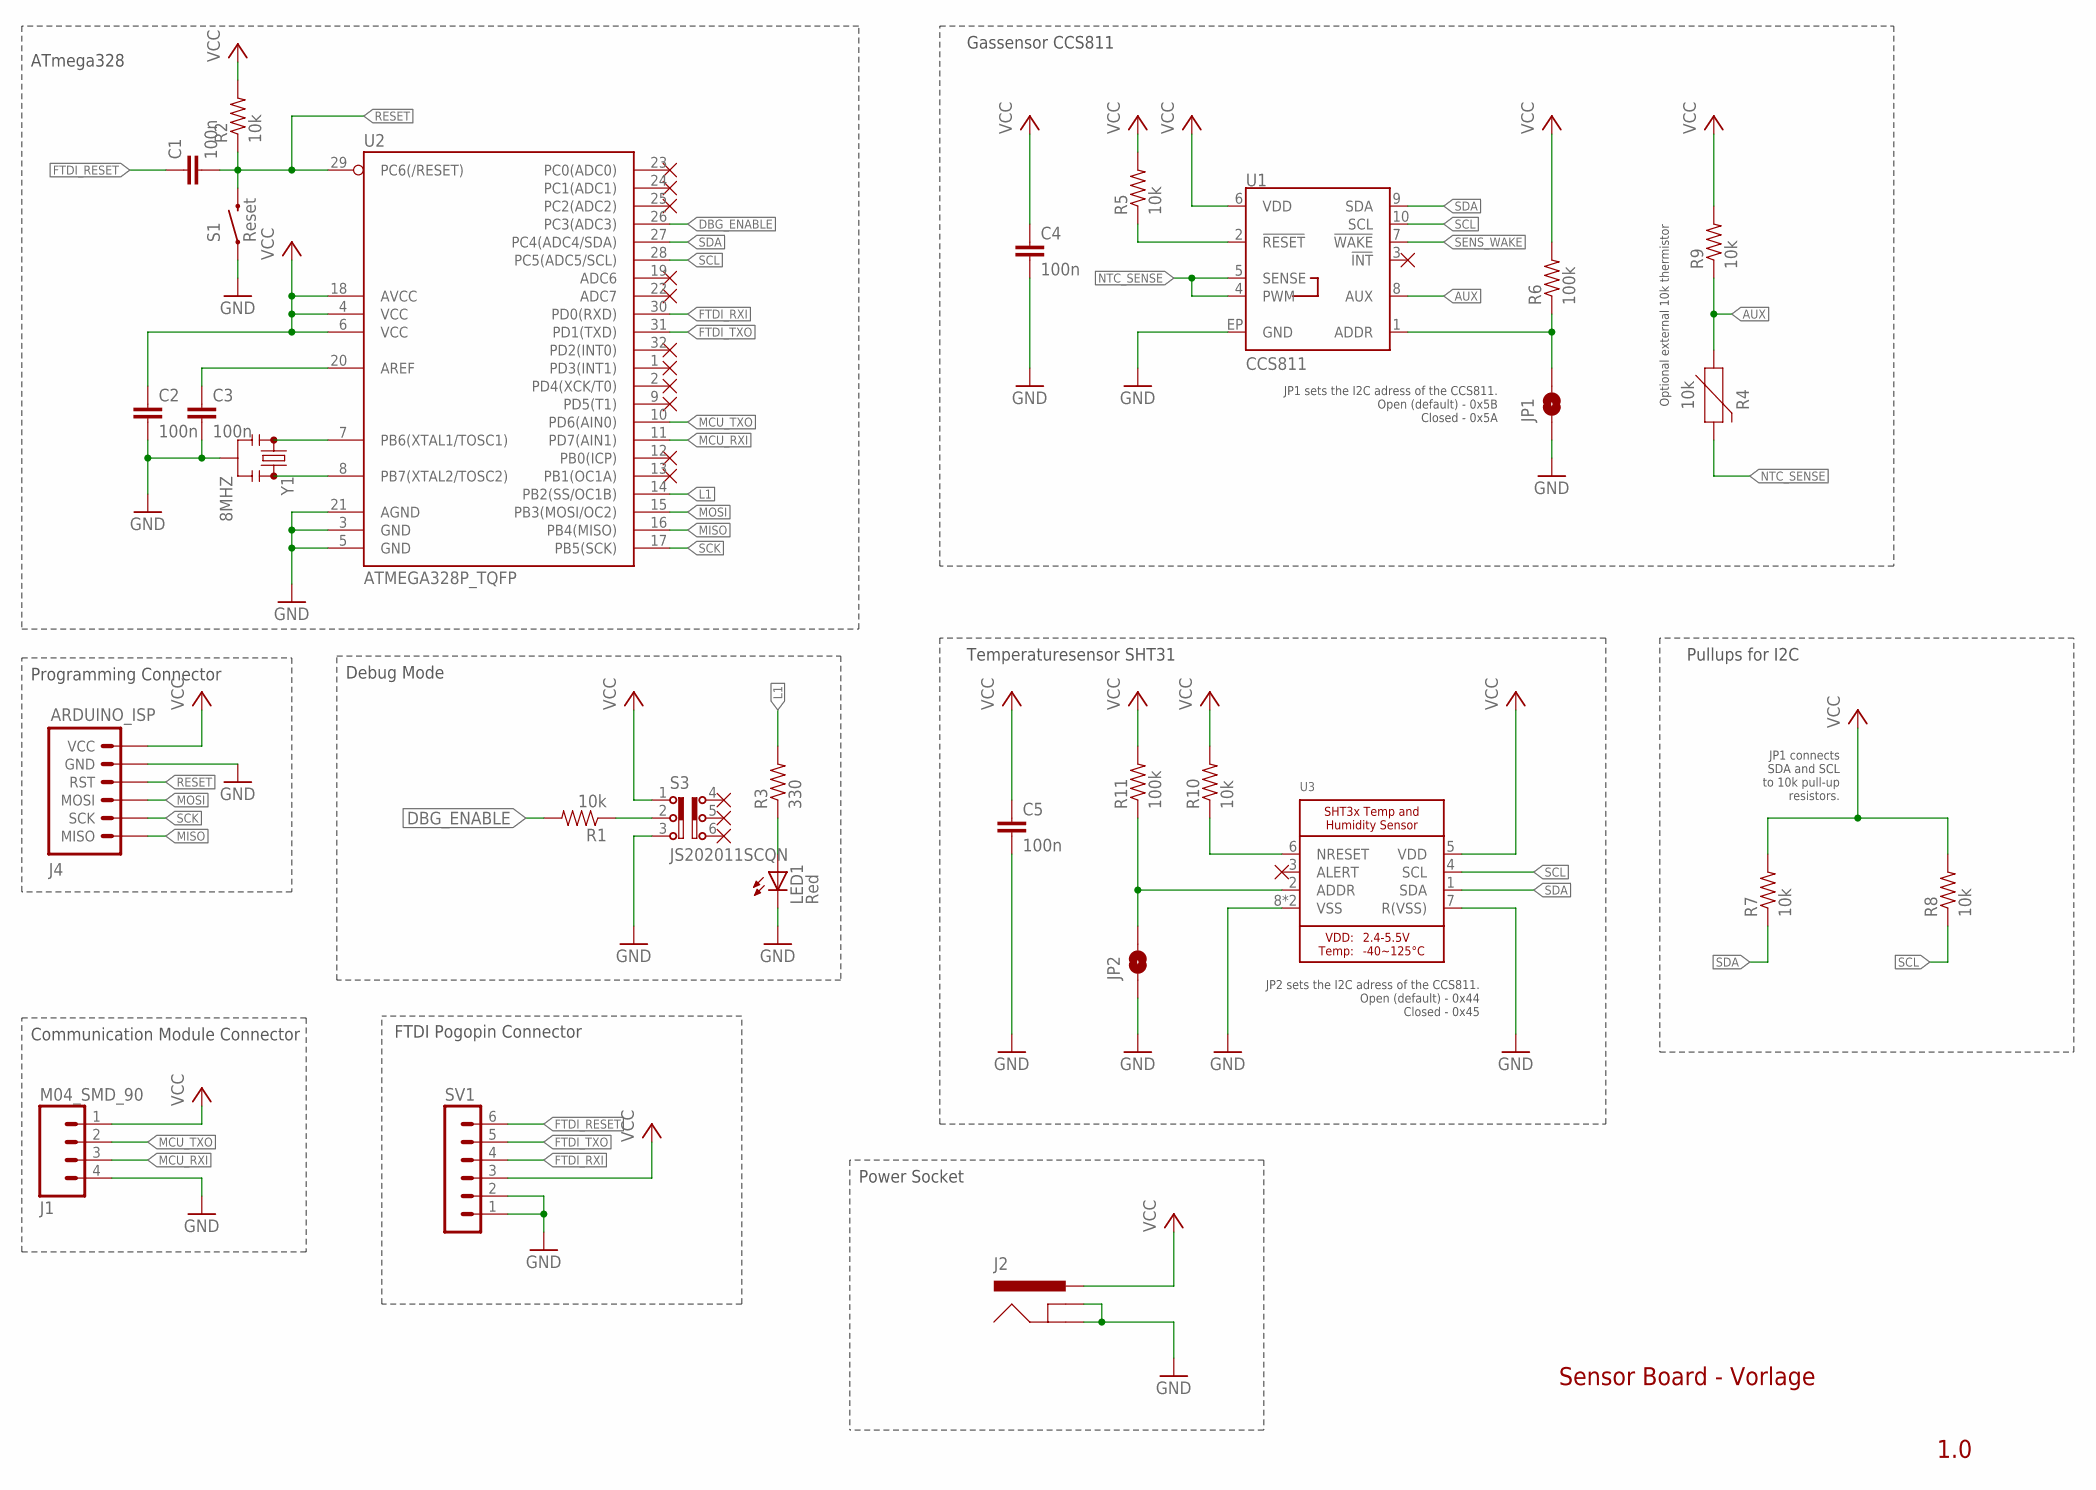
[picture p122: schematic Sensor_Board_0x06_CO2_CCS811_v2.sch]

Parts:
C1, C2, C3, C4, C5: 100n; C0805
J1: M04_SMD_90
J2: 5.5x2.1mm Barrel; POWER_JACK_SMD
J4: ARDUINO_ISP; M-2X3
JP1, JP2: SPARKFUN-JUMPERS_JUMPER-SMT_2_NO_SILK; SPARKFUN-JUMPERS_SMT-JUMPER_2_NO_SILK
LED1: Red; SML0805
R1, R2, R5, R7, R8, R9, R10: 10k; 0805
R3: 330; 0805
R4: 10k; CCS811_BREAKOUT_TEMP_0603
R6, R11: 100k; 0805
S1: Reset; M-PUSHBUTTON-SMD
S3: JS202011SCQN
SV1: MA06-1
U1: CCS811; CCS811_BREAKOUT_TEMP_LGA10
U2: ATMEGA328P_TQFP; TQFP32-08
U3: MICROBUILDER_SHT3X
Y1: 8MHZ; RESONATOR-SMD

Connections:
AUX: R4.1, R9.1, U1.8 (AUX)
DBG_ENABLE: R1.2, U2.26 (PC3(ADC3))
FTDI_RESET: C1.1, SV1.6
FTDI_RXI: SV1.4, U2.30 (PD0(RXD))
FTDI_TXO: SV1.5, U2.31 (PD1(TXD))
GND: C2.2, C3.2, C4.2, C5.2, J1.4, J2.GND (GNDBREAK), J2.P$4 (GND), J4.P$5 (GND), JP1.1, JP2.1, LED1.C, S1.1 (LEFT), S3.3, SV1.1, SV1.2, U1.EP (GND), U2.3 (GND), U2.5 (GND), U2.21 (AGND), U3.7 (R(VSS)), U3.8 (VSS), Y1.2
L1: R3.2, U2.14 (PB2(SS/OC1B))
MCU_RXI: J1.3, U2.11 (PD7(AIN1))
MCU_TXO: J1.2, U2.10 (PD6(AIN0))
MISO: J4.P$1 (MISO), U2.16 (PB4(MISO))
MOSI: J4.P$3 (MOSI), U2.15 (PB3(MOSI/OC2))
unnamed: U2.8 (PB7(XTAL2/TOSC2)), Y1.3
unnamed: U2.7 (PB6(XTAL1/TOSC1)), Y1.1
unnamed: R1.1, S3.2
unnamed: JP1.2, R6.1, U1.1 (ADDR)
unnamed: R10.1, U3.6 (NRESET)
unnamed: JP2.2, R11.1, U3.2 (ADDR)
unnamed: C3.1, U2.20 (AREF)
unnamed: LED1.A, R3.1
NTC_SENSE: R4.2, U1.4 (PWM), U1.5 (SENSE)
RESET: C1.2, J4.P$4 (RST), R2.1, S1.3 (RIGHT), U2.29 (PC6(/RESET))
SCK: J4.P$2 (SCK), U2.17 (PB5(SCK))
SCL: R8.1, U1.10 (SCL), U2.28 (PC5(ADC5/SCL)), U3.4 (SCL)
SDA: R7.1, U1.9 (SDA), U2.27 (PC4(ADC4/SDA)), U3.1 (SDA)
SENS_RES: R5.1, U1.2 (!RESET!)
SENS_WAKE: U1.7 (!WAKE!)
VCC: C2.1, C4.1, C5.1, J1.1, J2.VIN0 (PWR), J4.P$6 (VCC), R2.2, R5.2, R6.2, R7.2, R8.2, R9.2, R10.2, R11.2, S3.1, SV1.3, U1.6 (VDD), U2.4 (VCC), U2.6 (VCC), U2.18 (AVCC), U3.5 (VDD)

Notes on the sheet:
Debug Mode
Programming Connector
ATmega328
Communication Module Connector
Sensor Board - Vorlage
1.0
FTDI Pogopin Connector
JP1 sets the I2C adress of the CCS811. Open (default) - 0x5B Closed - 0x5A
JP1 connects SDA and SCL to 10k pull-up resistors.
Optional external 10k thermistor
JP2 sets the I2C adress of the CCS811. Open (default) - 0x44 Closed - 0x45
Gassensor CCS811
Temperaturesensor SHT31
Pullups for I2C
Power Socket
