architecture-building-systems/Wireless-Sensor-Network/Sensor_Node/Sensor_Boards/Sensor_Board_0xXX_Protoyping/Eagle/Sensor_Board_0xXX_Prototyping_v1.sch

## EAGLE design Sensor_Node/Sensor_Boards/Sensor_Board_0xXX_Protoyping/Eagle/Sensor_Board_0xXX_Prototyping_v1.sch (2017-08-06)

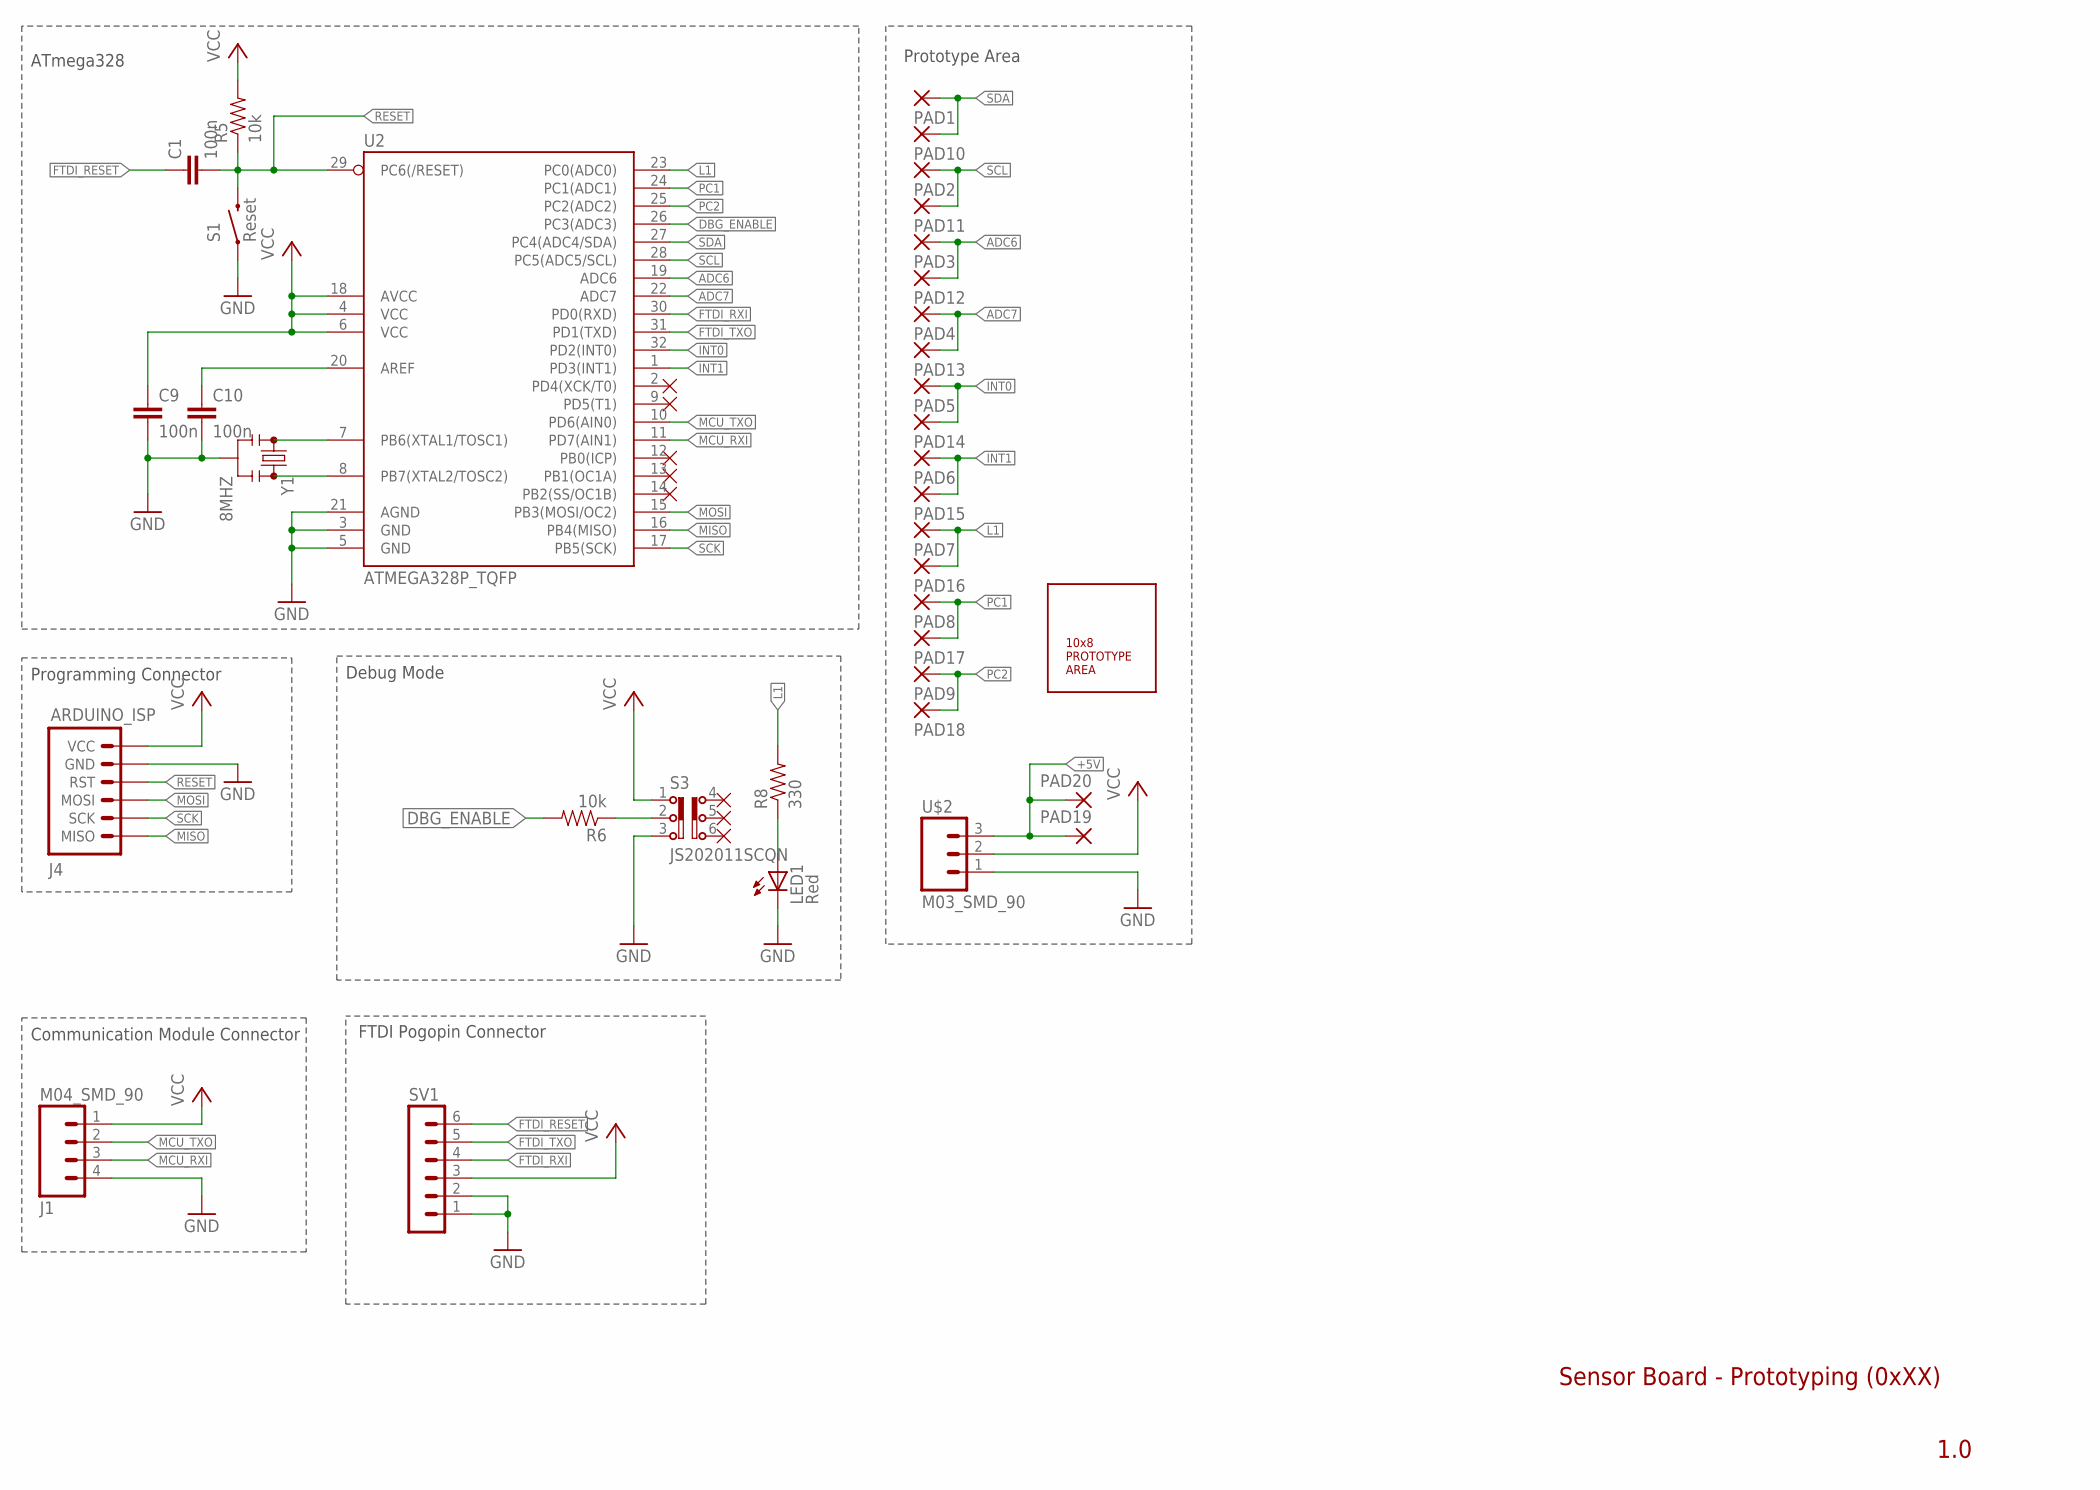
[picture p123: schematic Sensor_Board_0xXX_Prototyping_v1.sch]

Parts:
C1, C9, C10: 100n; C0805
J1: M04_SMD_90
J4: ARDUINO_ISP; M-2X3
LED1: Red; SML0805
PAD1, PAD2, PAD3, PAD4, PAD5, PAD6, PAD7, PAD8, PAD9, PAD10, PAD11, PAD12, PAD13, PAD14, PAD15, PAD16, PAD17, PAD18, PAD19, PAD20: 1,6/0,9
R5, R6: 10k; 0805
R8: 330; 0805
S1: Reset; M-PUSHBUTTON-SMD
S3: JS202011SCQN
SV1: MA06-1
U2: ATMEGA328P_TQFP; TQFP32-08
U$1: 10X8_PROTOTYPE_AREA
U$2: M03_SMD_90
Y1: 8MHZ; RESONATOR-SMD

Connections:
+5V: PAD19.1, PAD20.1, U$2.3
ADC6: PAD3.1, PAD12.1, U2.19 (ADC6)
ADC7: PAD4.1, PAD13.1, U2.22 (ADC7)
DBG_ENABLE: R6.2, U2.26 (PC3(ADC3))
FTDI_RESET: C1.1, SV1.6
FTDI_RXI: SV1.4, U2.30 (PD0(RXD))
FTDI_TXO: SV1.5, U2.31 (PD1(TXD))
GND: C9.2, C10.2, J1.4, J4.P$5 (GND), LED1.C, S1.1 (LEFT), S3.3, SV1.1, SV1.2, U2.3 (GND), U2.5 (GND), U2.21 (AGND), U$2.1, Y1.2
INT0: PAD5.1, PAD14.1, U2.32 (PD2(INT0))
INT1: PAD6.1, PAD15.1, U2.1 (PD3(INT1))
L1: PAD7.1, PAD16.1, R8.2, U2.23 (PC0(ADC0))
MCU_RXI: J1.3, U2.11 (PD7(AIN1))
MCU_TXO: J1.2, U2.10 (PD6(AIN0))
MISO: J4.P$1 (MISO), U2.16 (PB4(MISO))
MOSI: J4.P$3 (MOSI), U2.15 (PB3(MOSI/OC2))
unnamed: U2.8 (PB7(XTAL2/TOSC2)), Y1.3
unnamed: U2.7 (PB6(XTAL1/TOSC1)), Y1.1
unnamed: R6.1, S3.2
unnamed: C10.1, U2.20 (AREF)
unnamed: LED1.A, R8.1
PC1: PAD8.1, PAD17.1, U2.24 (PC1(ADC1))
PC2: PAD9.1, PAD18.1, U2.25 (PC2(ADC2))
RESET: C1.2, J4.P$4 (RST), R5.1, S1.3 (RIGHT), U2.29 (PC6(/RESET))
SCK: J4.P$2 (SCK), U2.17 (PB5(SCK))
SCL: PAD2.1, PAD11.1, U2.28 (PC5(ADC5/SCL))
SDA: PAD1.1, PAD10.1, U2.27 (PC4(ADC4/SDA))
VCC: C9.1, J1.1, J4.P$6 (VCC), R5.2, S3.1, SV1.3, U2.4 (VCC), U2.6 (VCC), U2.18 (AVCC), U$2.2

Notes on the sheet:
Debug Mode
Programming Connector
ATmega328
Communication Module Connector
Sensor Board - Prototyping (0xXX)
1.0
FTDI Pogopin Connector
Prototype Area
