architecture-building-systems/Wireless-Sensor-Network/Sensor_Node/Sensor_modules/Sensor_Module_19_door_opening/Arduino/door_opening/door_opening.ino

/****
 * DS18B20x2
 * For creating a sensormodule with a new sensor:
 * Only change:
 * - struct SMpayload to contain the appropriate variables
 * - in setup(), between // START SENSOR MEASUREMENT and // END SENSOR MEASUREMENT add code that gets the measurement and fills the payload's variables with the data.
 */

static const uint8_t SENSORMODULE_TYPE = 0x13;  // HEX: 0x13 = DEC: 19

int P_LED = 14;
int P_Reed_Switch = 3;

// Temperature reading is read as float. Use 1 byte for value before comma and one byte for value after comma
struct SMpayload
{
  float state1;
};
typedef struct SMpayload SMpayload;

SMpayload payload;

static const uint8_t FRAMESTART_BYTE = 0xAA;

void setup() {
  Serial.begin(9600);
  blink();

  // START SENSOR MEASUREMENT
  pinMode(P_Reed_Switch, INPUT);
  float state = digitalRead(P_Reed_Switch); 
  payload.state1 = state;
  
  // END SENSOR MEASUREMENT

  uint8_t checksumbyte = 0;

  // Framestart byte
  Serial.write(FRAMESTART_BYTE);
  checksumbyte += FRAMESTART_BYTE;

  // SM type
  Serial.write((uint8_t) SENSORMODULE_TYPE); // Sensormodule type
  checksumbyte += (uint8_t) SENSORMODULE_TYPE;

  // Length of data
  Serial.write((uint8_t) sizeof(payload)); // Sensormodule type
  checksumbyte += (uint8_t) sizeof(payload);

  // Payload
  Serial.write((uint8_t*) &payload, sizeof(payload));
  
  uint8_t* payloadPtr = (uint8_t*) &payload;
  for (uint8_t k=0;k<sizeof(payload);k++)
  {
    checksumbyte += payloadPtr[k];
  }

  checksumbyte = 0xFF - checksumbyte; // such that is sums up to 0xFF
  Serial.write(checksumbyte);
  blink();
}

void loop()
{
  delay(10000);
}

void blink(){

  pinMode(P_LED, OUTPUT);
  digitalWrite(P_LED, HIGH);
  delay(10);
  digitalWrite(P_LED, LOW);
}
