architecture-building-systems/Wireless-Sensor-Network/Sensor_Node/Sensor_modules/Sensor_Module_0x12_U-Value/Arduino/Functiontest_0x12_U-Value_100_meas_with_offset/Functiontest_0x12_U-Value_100_meas_with_offset.ino

/*
  Functiontest_0x12_U-Value_100_meas_with_offset.ino - Advanced functionality sketch for the U-Value board.
  Here a GAIN and and OFFSET calibration is made, but no peripheral sensors on the board are used. 
  Version 1.0
  Created by Ruben J. Stadler, May 10, 2018.
  <rstadler@ethz.ch>

  This sketch is licensed under the GPL 3.0 license.
*/

#include <SPI.h>
#include <arduino.h>
#include <MCP3911.h>

#define ADC_CLK 9       //Pin 9 is the OC1A-Pin of the Arduino Pro Mini and goes to OSC1-Pin of the MCP3911
#define ADC_CS 8        //Pin 8 of the Arduino Pro Mini goes to the CS-Pin of the MCP3911
#define ADC_IN_ENABLE 2
#define ADC_IN_SHORT 4
#define ADC_INTERRUPT 3
#define DEBUG_LED 10

MCP3911 mcp3911;

volatile uint8_t index = 0; //Array-Index
long values_ch0[100] = {};  //Array for the 100 measurements

//Counter the GAIN_Error. 
//Measure a relatively high voltage and enter it's value into "measured_voltage" 
double real_voltage = 23802;          //Measured with Multimeter (Here this equals a "real" voltage of 238.02mV)
double measured_voltage = 24659;      //Initial measurement with MCP3911: Done with script "Functiontest_0x12_U-Value_100_meas_no_offset"

//ADC interrupt function
void ch0_data_interrupt(void)
{
  values_ch0[index] = mcp3911.read_raw_data(REG_CHANNEL0);
  index++;
  if (index > 99)
    mcp3911.enter_reset_mode(); //Enter reset mode to stop any more interrupts
}

//ADC calibration function
long ch0_calibrate(void)
{
  //First we calculate the GAIN-Offset

  //---------------------------------
  mcp3911.write_offset(0, REG_OFFCAL_CH0);  //Write initial offset to zero

  digitalWrite(ADC_IN_ENABLE, LOW);         //Physically ground the input of the uV-Sensor
  digitalWrite(ADC_IN_SHORT, HIGH);
  delay(100);

  //Start 100 measurements with interrupts
  index = 0;
  mcp3911.exit_reset_mode();    //Exit reset mode to start interrupts again.
  while (index < 100);          //Do nothing until 100 measurements are completed

  digitalWrite(ADC_IN_SHORT, LOW);          //Enable connection from Sensor to ADC again
  digitalWrite(ADC_IN_ENABLE, HIGH);

  long sum = 0;             //Calculate average of the 100 measurements
  for (int i = 0; i < 100; i++) {
    sum += values_ch0[i];
  }
  long offset = (sum / 100) * -1; //We multiply by -1 since the offset gets added,
  //but to be correct we want it subtracted

  mcp3911.write_offset(offset, REG_OFFCAL_CH0);   //Write offset to register

  double offset_volt = mcp3911.data_to_voltage((sum / 100), REG_CHANNEL0);

  Serial.print("Offset CH0 = ");
  Serial.print(offset_volt, 8);
  Serial.print(" V     ");

  index = 0;

  delay(100);

  return offset*-1;
}

void setup() {
  pinMode(ADC_IN_ENABLE, OUTPUT);
  pinMode(ADC_IN_SHORT, OUTPUT);
  pinMode(DEBUG_LED, OUTPUT);

  digitalWrite(ADC_IN_ENABLE, HIGH);  //Enable physical connection between ADC and Sensor.
  digitalWrite(ADC_IN_SHORT, LOW);
  digitalWrite(DEBUG_LED, LOW);

  Serial.begin(9600);
  mcp3911.begin(ADC_CLK, ADC_CS);     //Initialize MCP3911
  mcp3911.generate_CLK();               //Generate 4MHZ clock on CLOCK_PIN

  REGISTER_SETTINGS settings = {};
  //PHASE-SETTINGS
  settings.PHASE    = 0;           //Phase shift between CH0/CH1 is 0
  //GAIN-SETTINGS
  settings.BOOST     = 0b10;       //Current boost is 1
  settings.PGA_CH1   = 0b000;      //CH1 gain is 1
  settings.PGA_CH0   = 0b000;      //CH0 gain is 1
  //STATUSCOM-SETTINGS
  settings.MODOUT    = 0b00;       //No modulator output enabled
  settings.DR_HIZ    = 0b1;        //DR pin state is logic high when data is not ready
  settings.DRMODE    = 0b00;       //Data ready pulses from lagging ADC are output on DR-Pin
  settings.READ      = 0b10;       //Adress counter loops register types
  settings.WRITE     = 0b1;        //Adress counter loops entire register map
  settings.WIDTH     = 0b11;       //CH0 and CH1 are in 24bit-mode
  settings.EN_OFFCAL = 0b1;        //Digital offset calibration on both channels enabled
  settings.EN_GAINCAL = 0b1;       //Gain calibration on both channels enabled
  //CONFIG-SETTINGS
  settings.PRE       = 0b00;       //AMCLK = MCLK
  settings.OSR       = 0b111;      //Oversamplingratio is set to 4096 (Default 256)
  settings.DITHER    = 0b11;       //Dithering on both channels maximal
  settings.AZ_FREQ   = 0b0;        //Auto-zeroing running at lower speed
  settings.RESET     = 0b00;       //Neither ADC in Reset mode
  settings.SHUTDOWN  = 0b00;       //Neither ADC in Shutdown
  settings.VREFEXT   = 0b0;        //Internal voltage reference enabled
  settings.CLKEXT    = 0b1;        //External clock drive on OSC1-Pin enabled

  mcp3911.configure(settings);     //Configure the MCP3911 with the settings above
  mcp3911.enter_reset_mode();      //Enter reset mode to prevent any measurements from being taken

  attachInterrupt(digitalPinToInterrupt(ADC_INTERRUPT), ch0_data_interrupt, FALLING);  //Call "ch0_data_interrupt" whenever an edge on the DR-Pin occurs

  delay(100);                      //Add a delay until the interrupt routine has started


  //Initially write gain-offset once!
  
  long offcal = ch0_calibrate();          //Initially calibrate offset of MCP3911 (and retrieve initial GND-Offset)

  double gain_error = (real_voltage/(measured_voltage + offcal))-1;   //MCP3911 Datasheet equation 5.8
  //gain_error = (real_voltage/measured_voltage) - 1;                 //Calculation without including the offcal
  long gain_error_24bit = gain_error * 8388608;                       //MCP3911 Datasheet equation 5.10

  mcp3911.write_offset(gain_error_24bit, REG_GAINCAL_CH0);  //Write gain-offset to GAINCAL_Register
  //mcp3911.write_offset(0, REG_GAINCAL_CH0);
  
  mcp3911.exit_reset_mode();       //Exit reset mode to start interrupts again.
}

void loop() {
  //If 100 measurement interrupts have taken place
  //calculate the average of all the measurements that were taken into "values_ch0[]".
  if (index > 99) {
    
    //digitalWrite(DEBUG_LED, !digitalRead(DEBUG_LED)); //Toggle DEBUG-LED (Don't do this, since it influences measurement)

    double average = 0;
    for (int i = 0; i < 100; i++) {
      average += values_ch0[i];
    }

    double voltage_ch0 = mcp3911.data_to_voltage(average / 100, REG_CHANNEL0); //Data to voltage needs the gain setting of the chosen channel

    Serial.print("Voltage CH0 = ");
    Serial.print(voltage_ch0, 8);
    Serial.print(" V \r");
    Serial.println("");


    index = 0;
    
    ch0_calibrate();           //Calibrate MCP3911 for next measurement
    delay(100);
    mcp3911.exit_reset_mode();        //Exit reset mode to start next measurement cycle
  }
}
