architecture-building-systems/Wireless-Sensor-Network/Gateway/Gateway_Feather/Arduino/test_soft_serial_tx_v1/test_soft_serial_tx_v1.ino

#include <SoftwareSerial.h>

//SoftwareSerial mySerial(12, 11); // RX, TX
SoftwareSerial mySerial(10, 11); // RX, TX
int counter =0;

void setup() {
  // put your setup code here, to run once:
  Serial.begin(115200);
  Serial.println("HardSerial initialized.");
  mySerial.begin(9600);
  mySerial.println("SoftSerial initialized.");
}

void loop() {
  // put your main code here, to run repeatedly:
  Serial.print("HardSerial: ");
  Serial.println(counter);
  
  mySerial.print("SoftSerial: ");
  mySerial.println(counter);
  counter++;
  delay(705);
}
